ThingySticks/PiBlade/Boards/PiBackPlaneConnector/Images/bottom.png

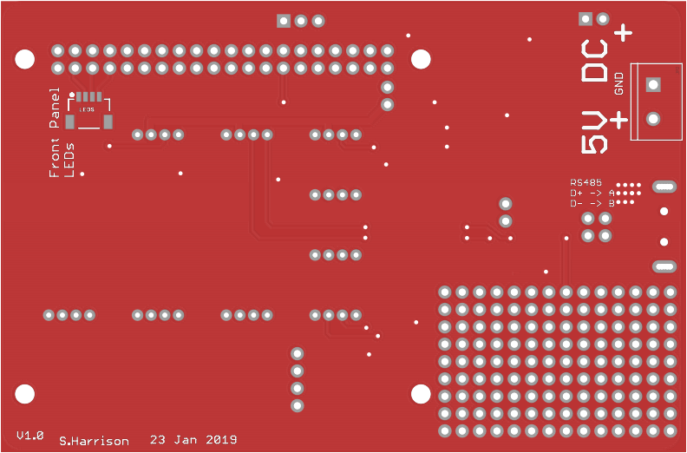
Boards/PiBackPlaneConnector/Images/bottom.png
