ThingySticks/PiBlade/Boards/PiBackPlaneConnector/Images/bottom_copper.png

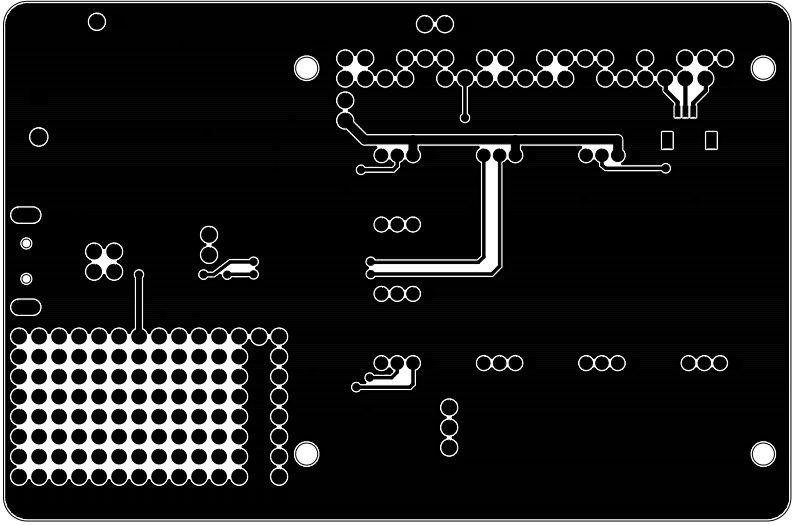
Boards/PiBackPlaneConnector/Images/bottom_copper.png
