ThingySticks/PiBlade/Boards/PiBackPlaneConnector/Images/bottom_silkscreen.png

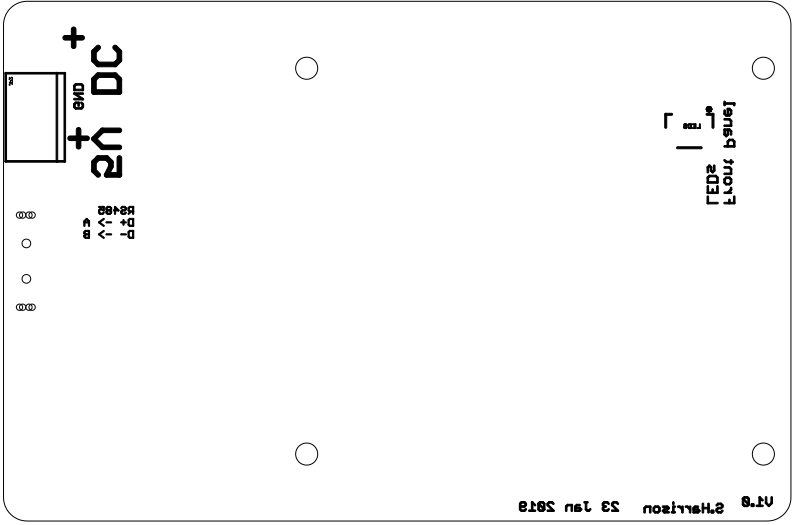
Boards/PiBackPlaneConnector/Images/bottom_silkscreen.png
