ThingySticks/PiBlade/Boards/PiBackPlaneConnector/Images/mill.png

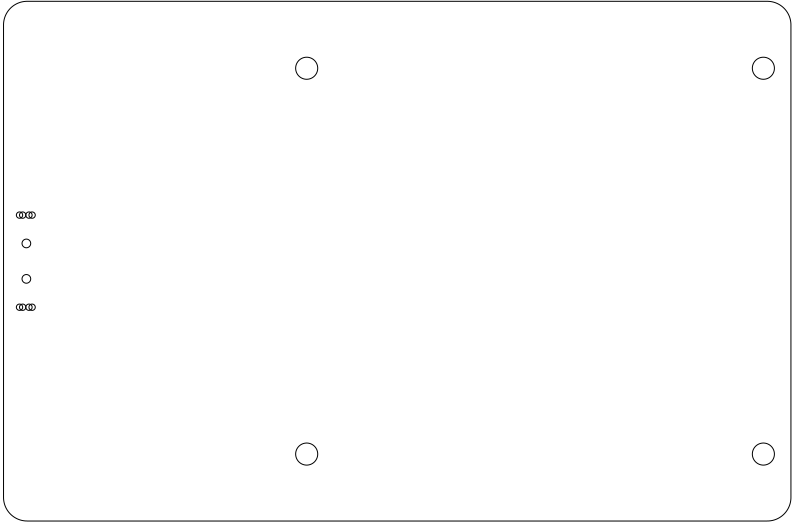
Boards/PiBackPlaneConnector/Images/mill.png
