ThingySticks/PiBlade/Boards/PiBackPlaneConnector/Images/PcbAllLayersDesign.png

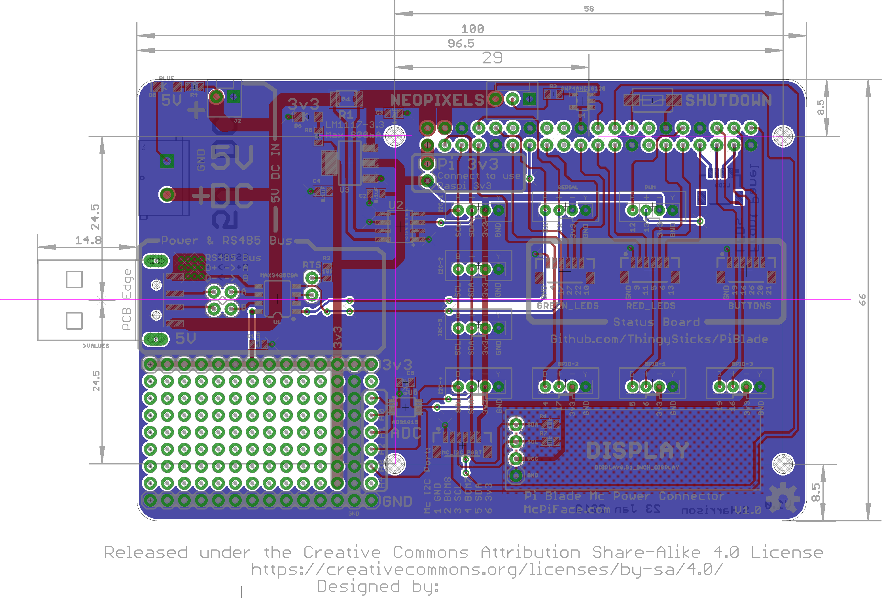
Boards/PiBackPlaneConnector/Images/PcbAllLayersDesign.png
