ThingySticks/PiBlade/Boards/PiBackPlaneConnector/Images/PcbTopDesign.png

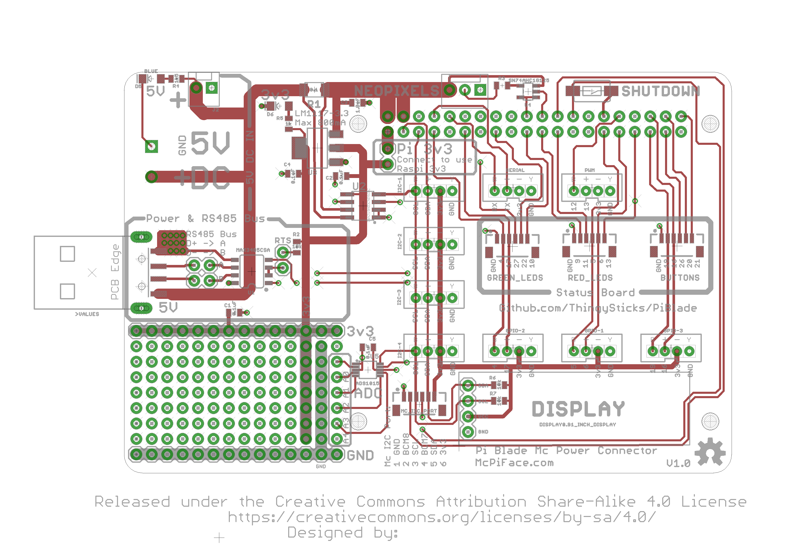
Boards/PiBackPlaneConnector/Images/PcbTopDesign.png
