ThingySticks/PiBlade/Boards/PiBackPlaneConnector/Images/Schematic.png

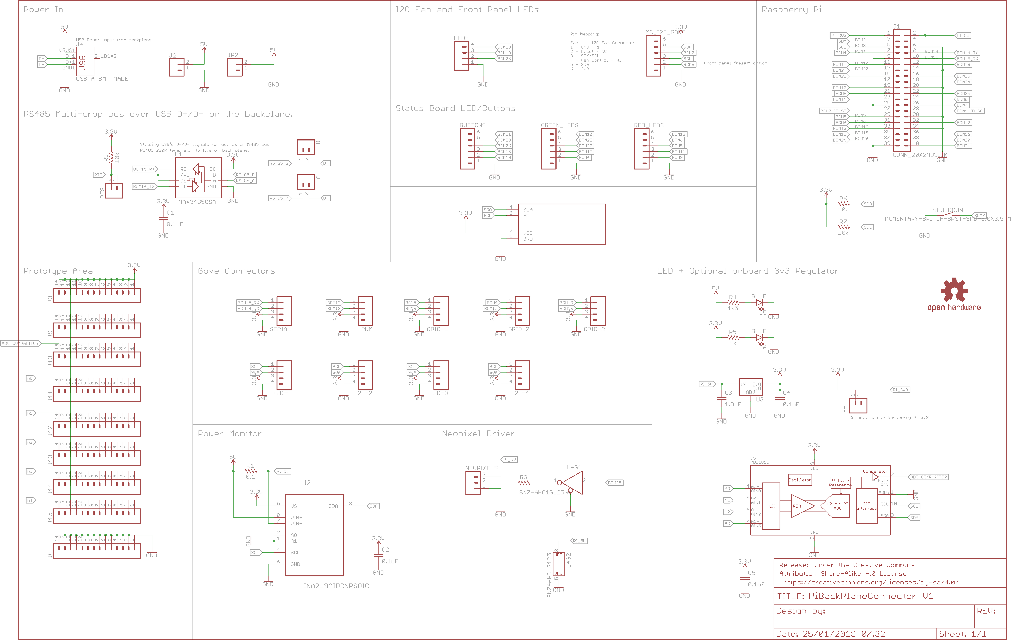
Boards/PiBackPlaneConnector/Images/Schematic.png
