ThingySticks/PiBlade/Boards/PiBackPlaneConnector/Images/top.png

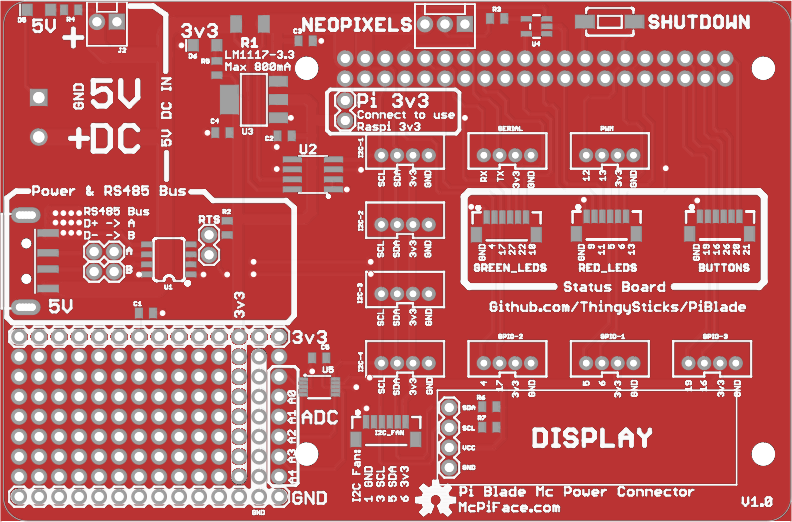
Boards/PiBackPlaneConnector/Images/top.png
