ThingySticks/PiBlade/Boards/PiBackPlaneConnector/Images/top_copper.png

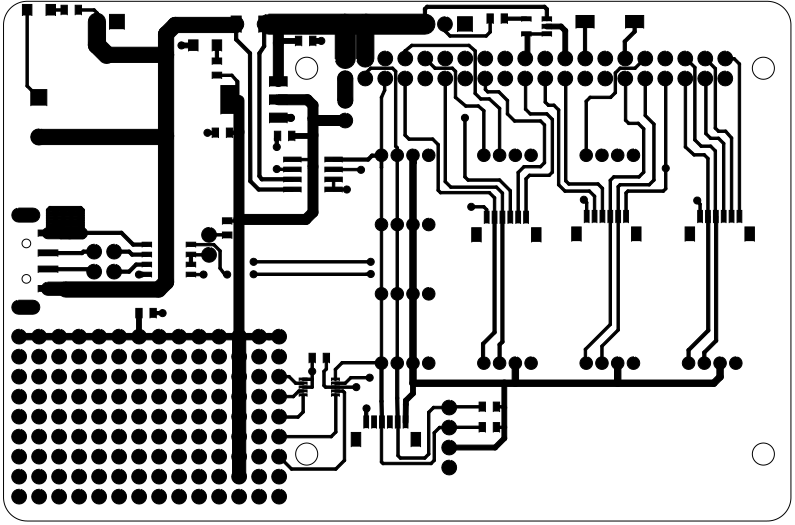
Boards/PiBackPlaneConnector/Images/top_copper.png
