ThingySticks/PiBlade/Boards/PiBackPlaneConnector/Images/top_silkscreen.png

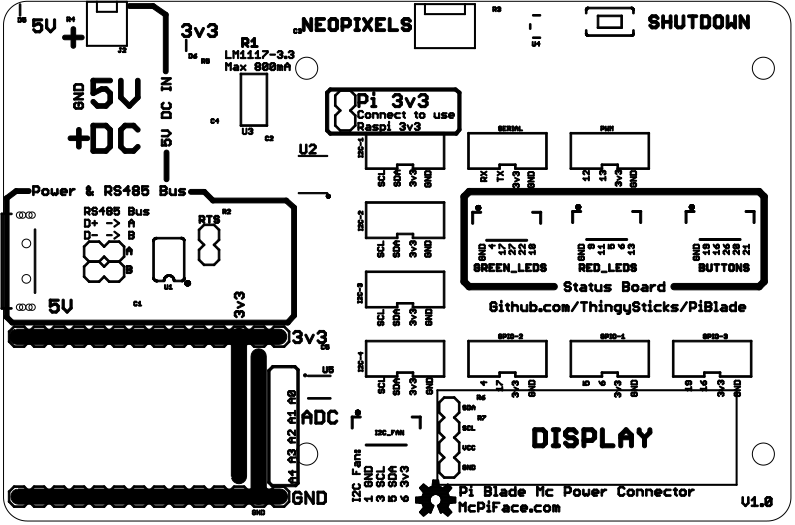
Boards/PiBackPlaneConnector/Images/top_silkscreen.png
