ThingySticks/PiBlade/Boards/PiBladeBackPlane/Images/PcbAllLayersDesign.png

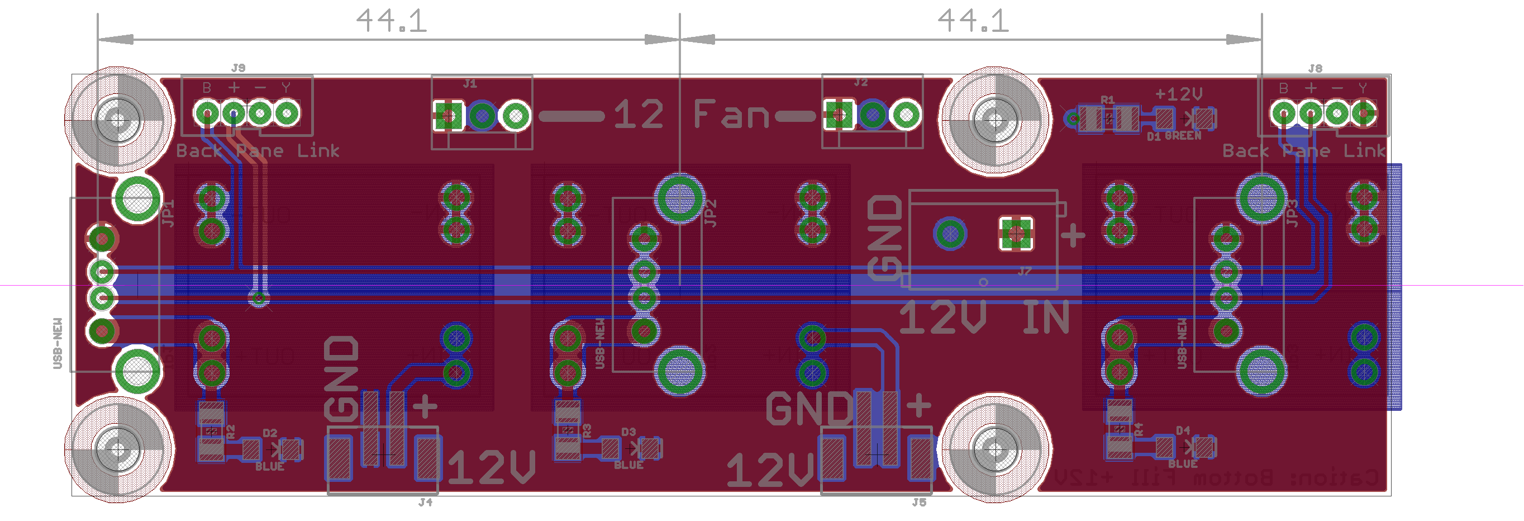
Boards/PiBladeBackPlane/Images/PcbAllLayersDesign.png
