ThingySticks/PiBlade/Boards/PiBladeBackPlane/Images/PcbBottomDesign.png

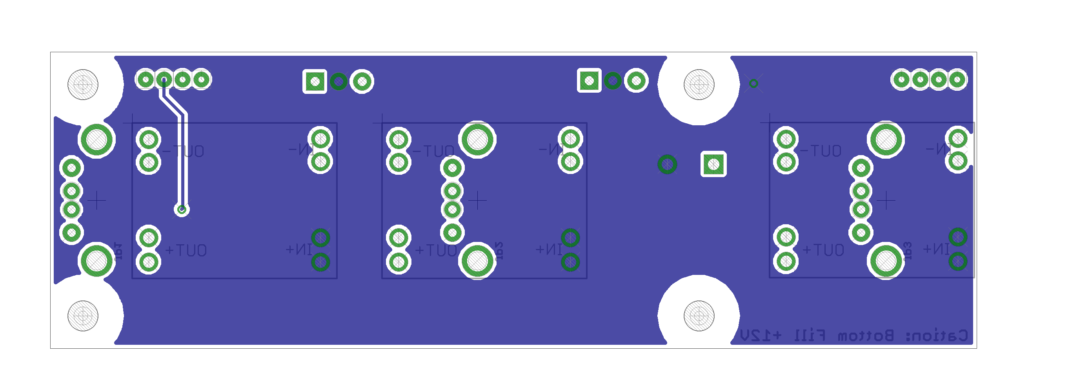
Boards/PiBladeBackPlane/Images/PcbBottomDesign.png
