ThingySticks/PiBlade/Boards/PiBladeBackPlane/Images/PcbTopDesign.png

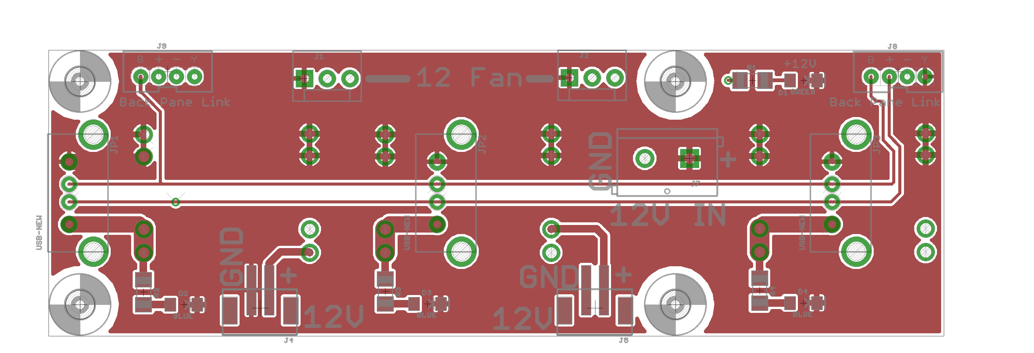
Boards/PiBladeBackPlane/Images/PcbTopDesign.png
