ThingySticks/PiBlade/Boards/PiBladeBackPlane/Images/Schematic.png

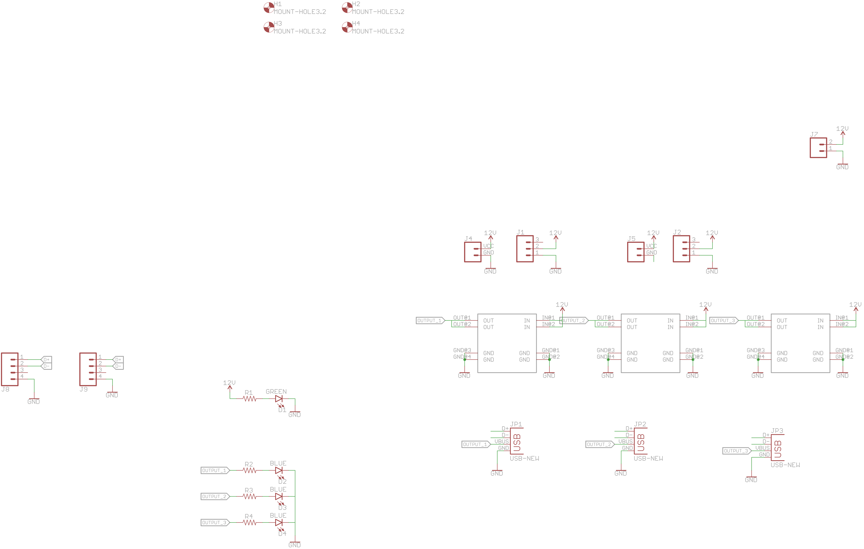
Boards/PiBladeBackPlane/Images/Schematic.png
