ThingySticks/PiBlade/Boards/PSU/Images/bottom.png

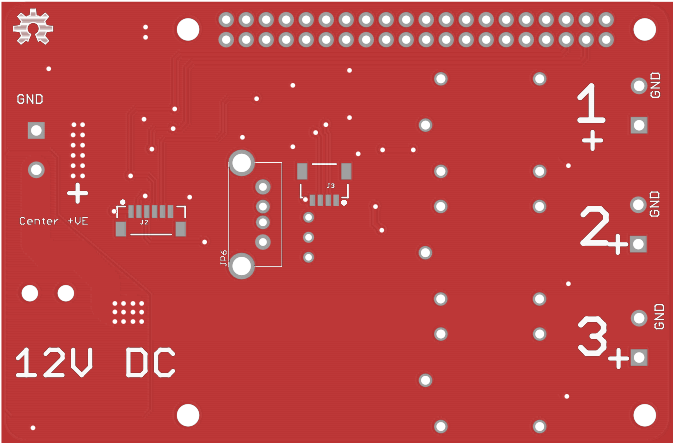
Boards/PSU/Images/bottom.png
