ThingySticks/PiBlade/Boards/PSU/Images/bottom_copper.png

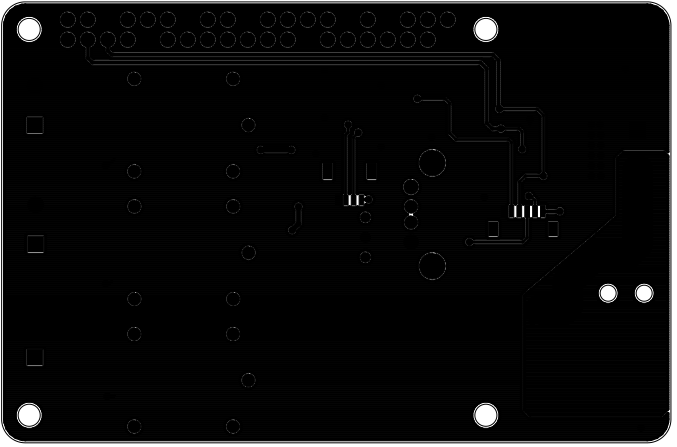
Boards/PSU/Images/bottom_copper.png
