ThingySticks/PiBlade/Boards/PSU/Images/bottom_silkscreen.png

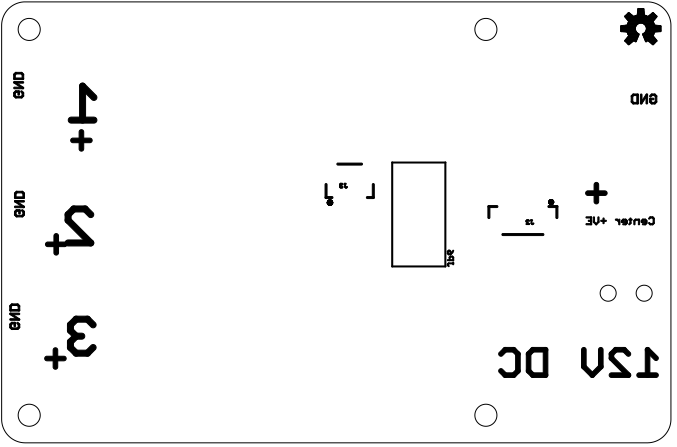
Boards/PSU/Images/bottom_silkscreen.png
