ThingySticks/PiBlade/Boards/PSU/Images/mill.png

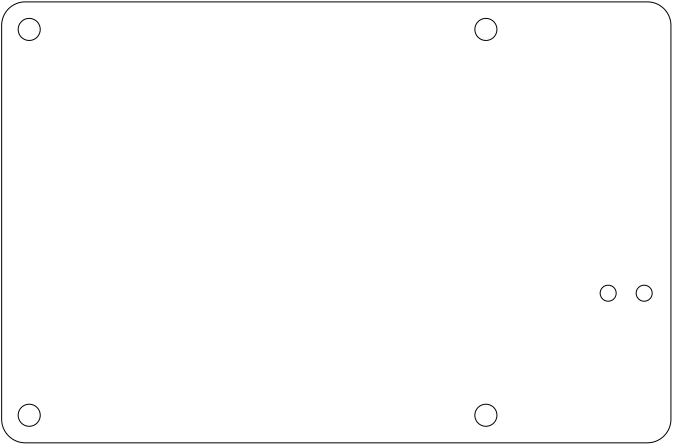
Boards/PSU/Images/mill.png
