ThingySticks/PiBlade/Boards/PSU/Images/PcbAllLayersDesign.png

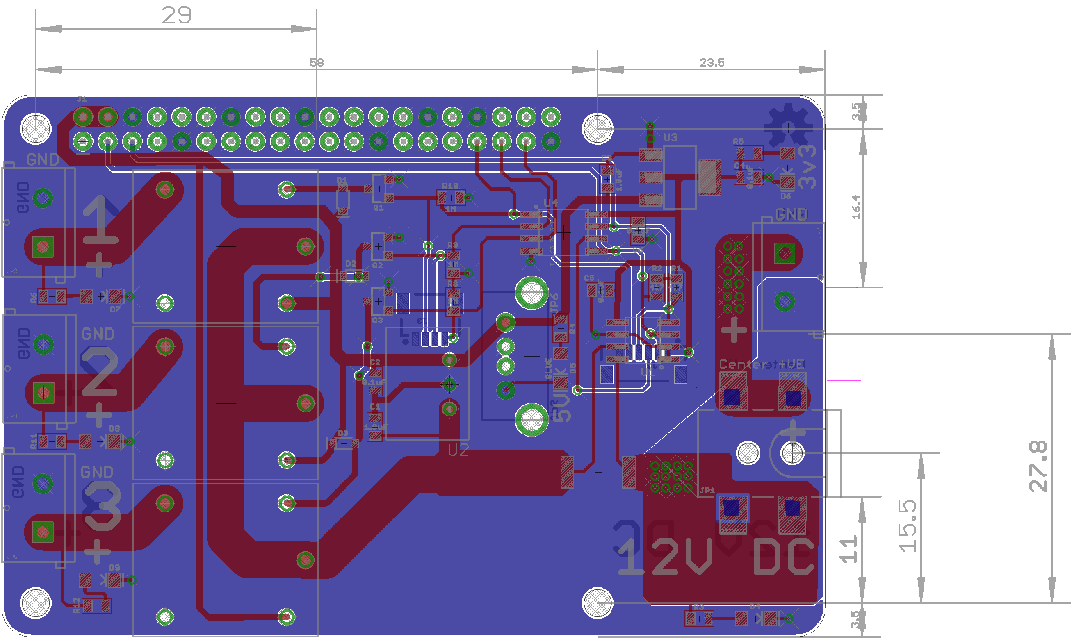
Boards/PSU/Images/PcbAllLayersDesign.png
