ThingySticks/PiBlade/Boards/PSU/Images/PcbBottomDesign.png

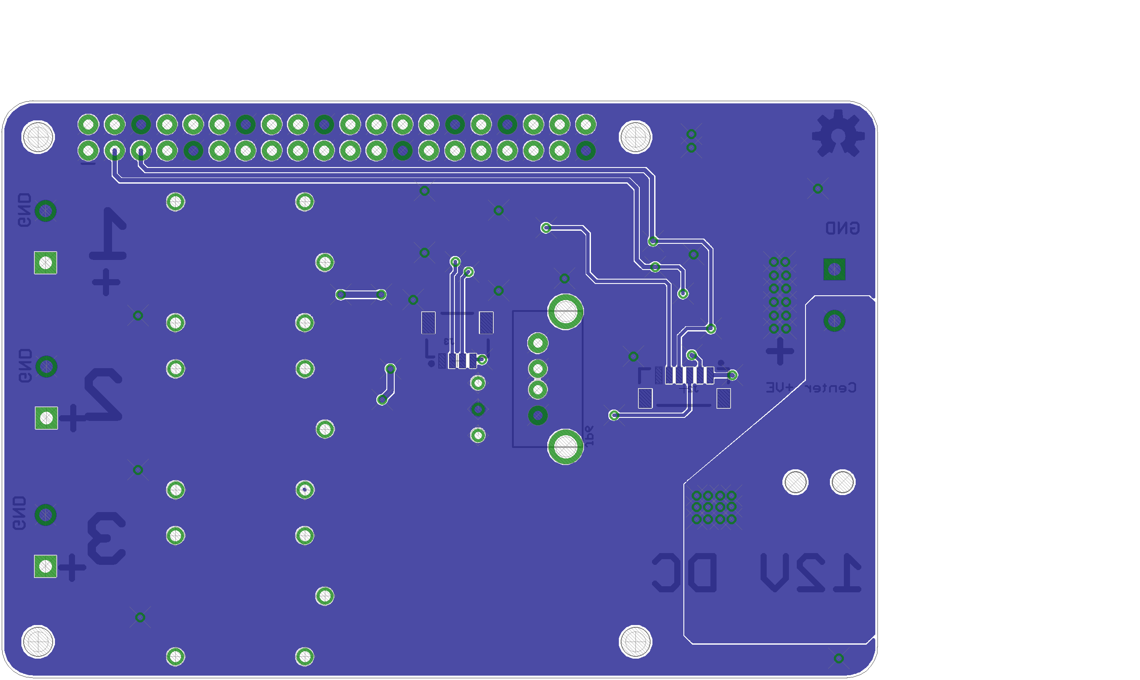
Boards/PSU/Images/PcbBottomDesign.png
