ThingySticks/PiBlade/Boards/PSU/Images/PcbTopDesign.png

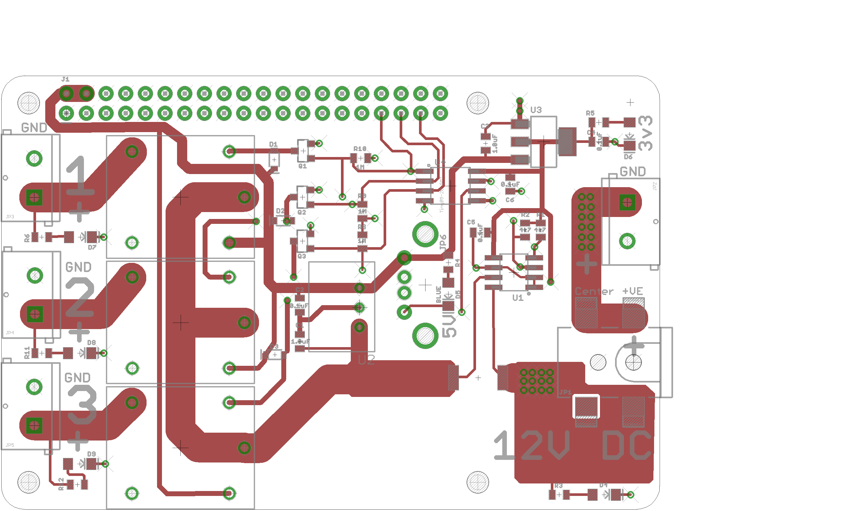
Boards/PSU/Images/PcbTopDesign.png
