ThingySticks/PiBlade/Boards/PSU/Images/Schematic.png

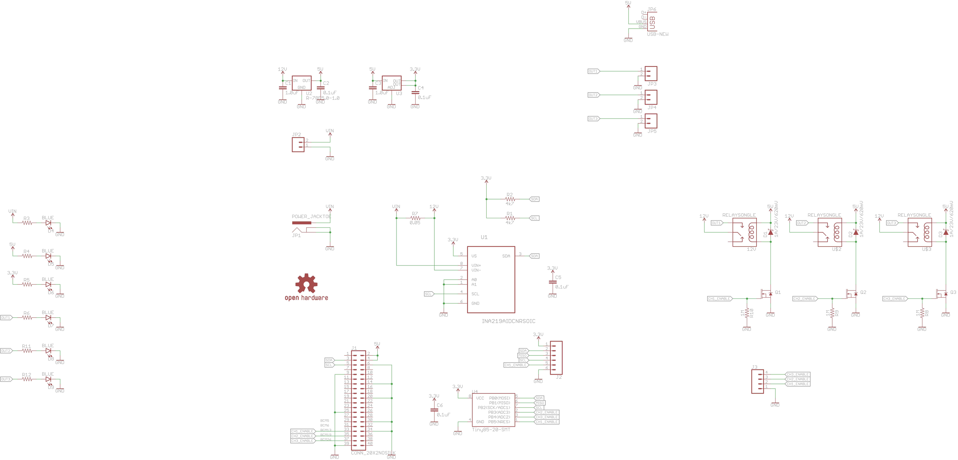
Boards/PSU/Images/Schematic.png
