ThingySticks/PiBlade/Boards/PSU/Images/top.png

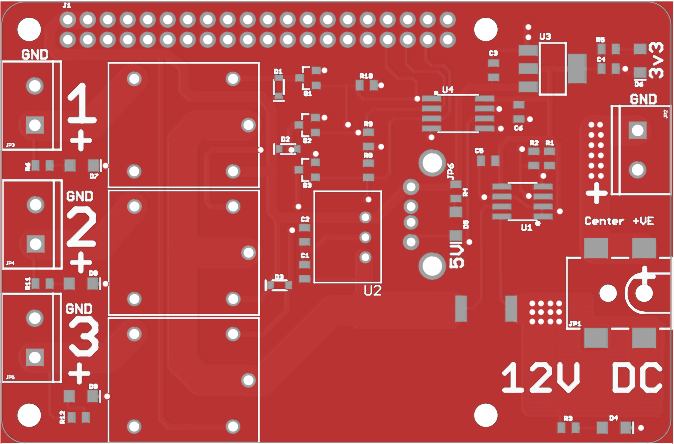
Boards/PSU/Images/top.png
