ThingySticks/PiBlade/Boards/PSU/Images/top_copper.png

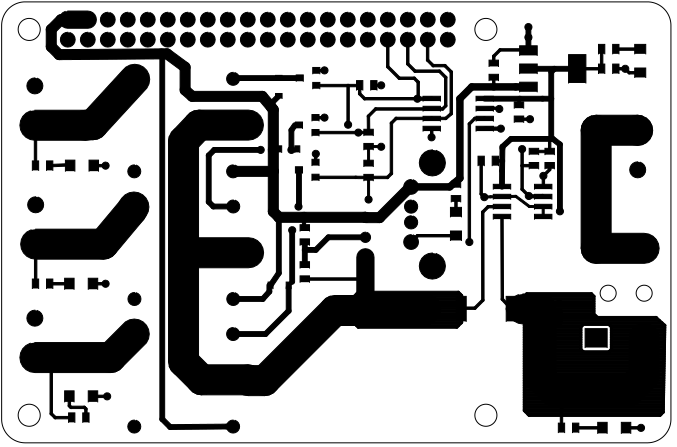
Boards/PSU/Images/top_copper.png
