ThingySticks/PiBlade/Boards/PSU/Images/top_silkscreen.png

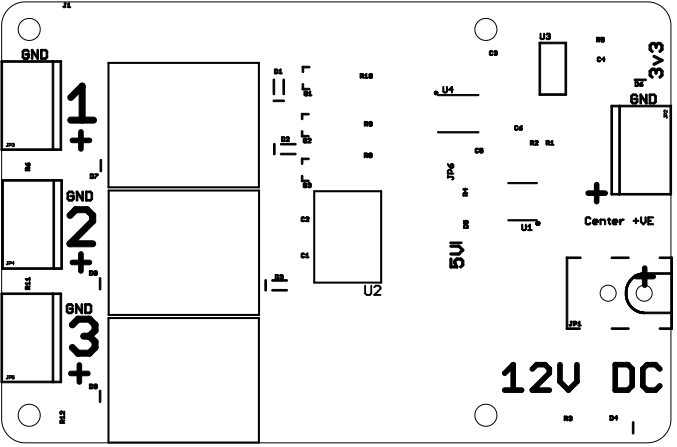
Boards/PSU/Images/top_silkscreen.png
