ThingySticks/PiBlade/FrontPanels/McPiFace/Images/Audio/bottom.png

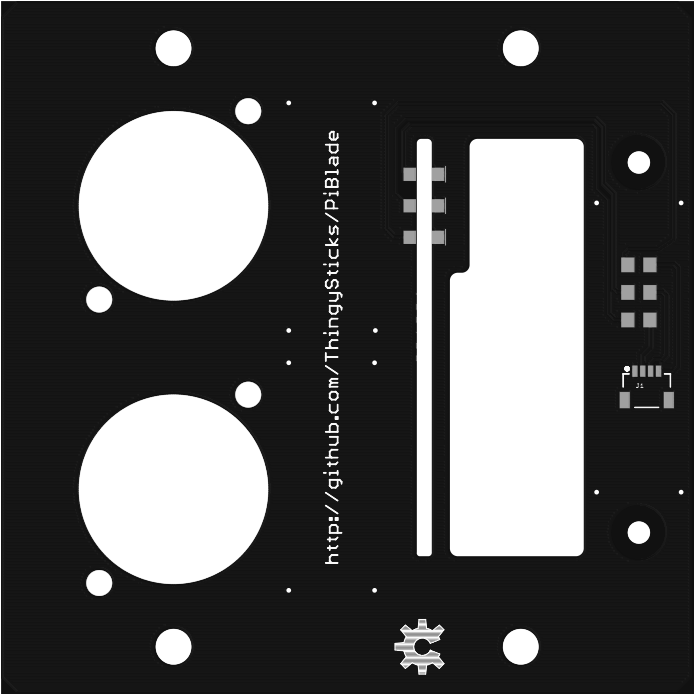
FrontPanels/McPiFace/Images/Audio/bottom.png
