ThingySticks/PiBlade/FrontPanels/McPiFace/Images/Audio/bottom_copper.png

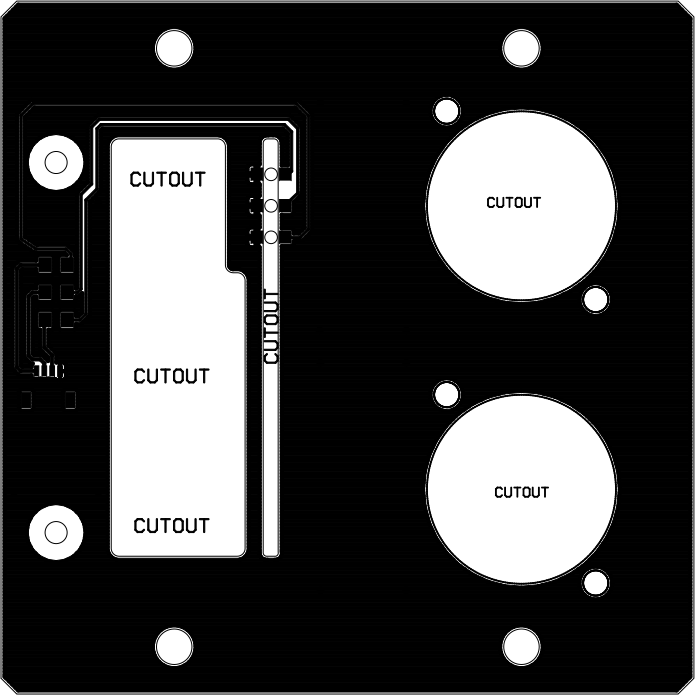
FrontPanels/McPiFace/Images/Audio/bottom_copper.png
