ThingySticks/PiBlade/FrontPanels/McPiFace/Images/Audio/bottom_silkscreen.png

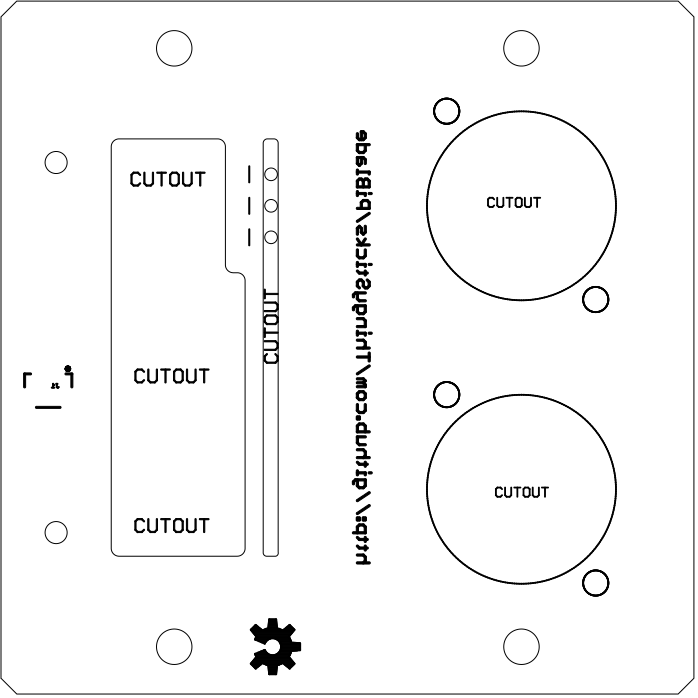
FrontPanels/McPiFace/Images/Audio/bottom_silkscreen.png
