ThingySticks/PiBlade/FrontPanels/McPiFace/Images/Audio/mill.png

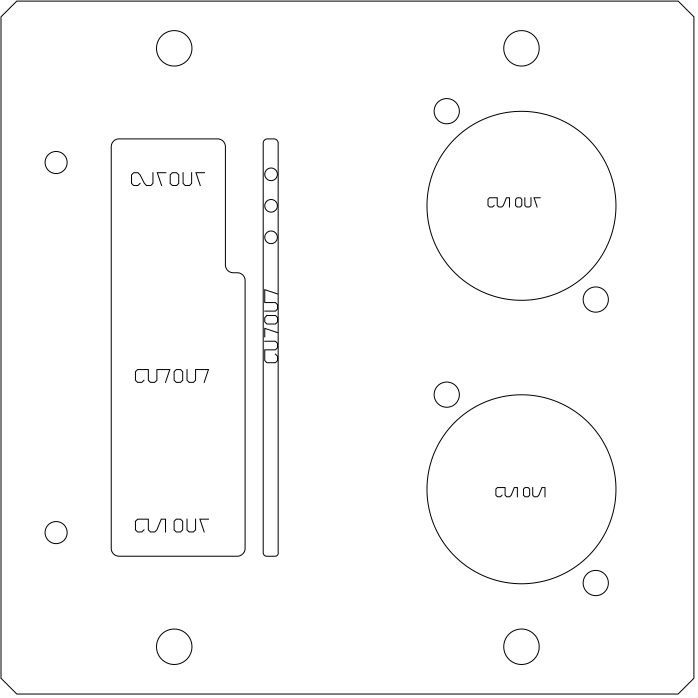
FrontPanels/McPiFace/Images/Audio/mill.png
