ThingySticks/PiBlade/FrontPanels/McPiFace/Images/Audio/PcbAllLayersDesign.png

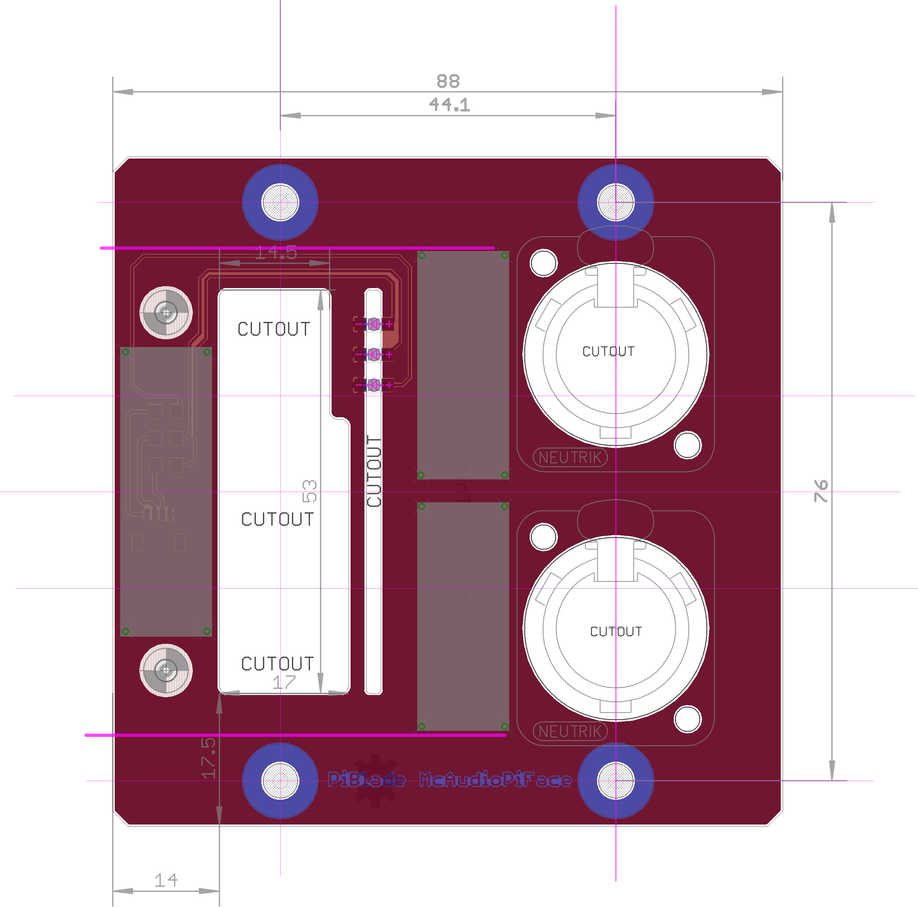
FrontPanels/McPiFace/Images/Audio/PcbAllLayersDesign.png
