ThingySticks/PiBlade/FrontPanels/McPiFace/Images/Audio/Schematic.png

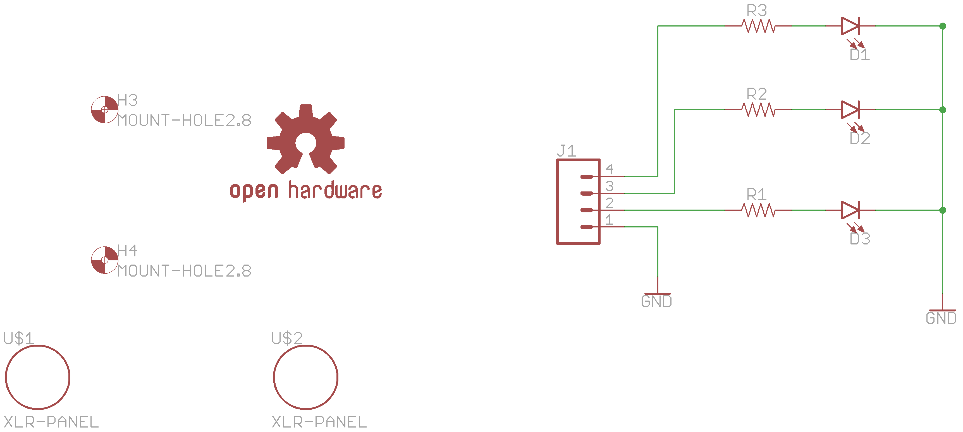
FrontPanels/McPiFace/Images/Audio/Schematic.png
