ThingySticks/PiBlade/FrontPanels/McPiFace/Images/Audio/top.png

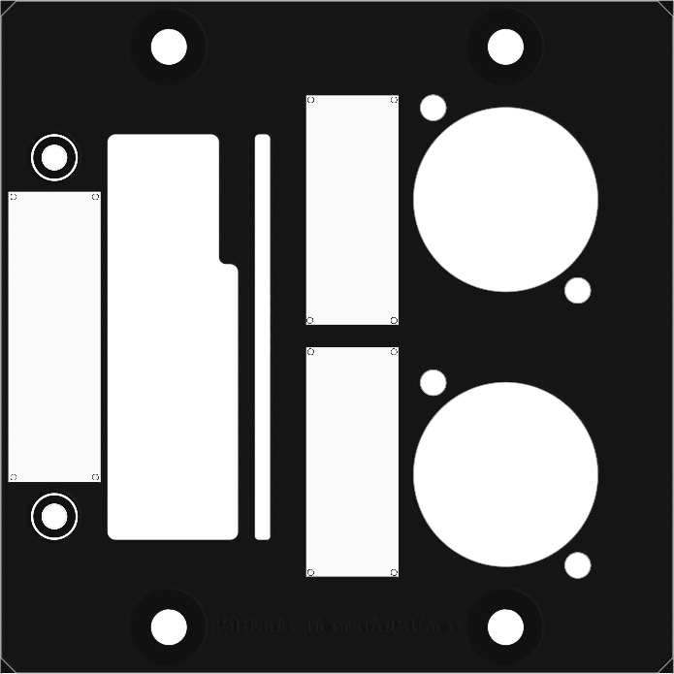
FrontPanels/McPiFace/Images/Audio/top.png
