ThingySticks/PiBlade/FrontPanels/McPiFace/Images/Audio/top_copper.png

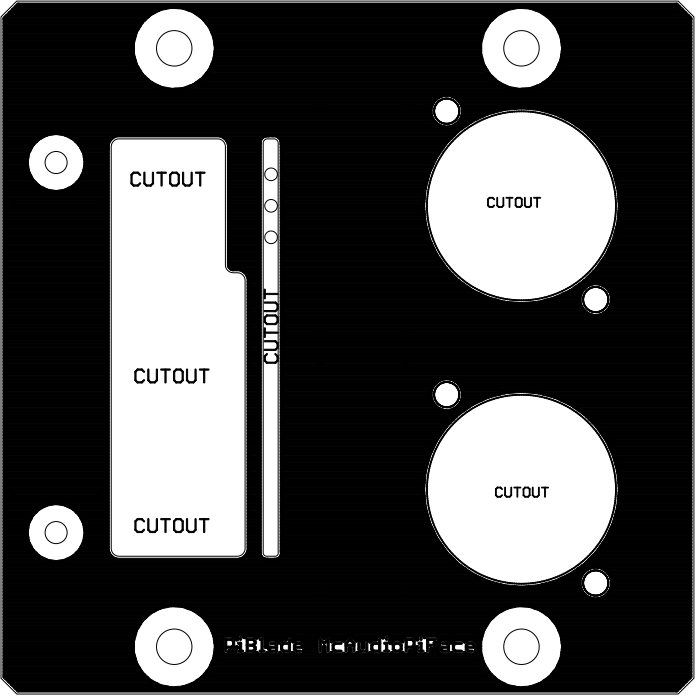
FrontPanels/McPiFace/Images/Audio/top_copper.png
