ThingySticks/PiBlade/FrontPanels/McPiFace/Images/Audio/top_silkscreen.png

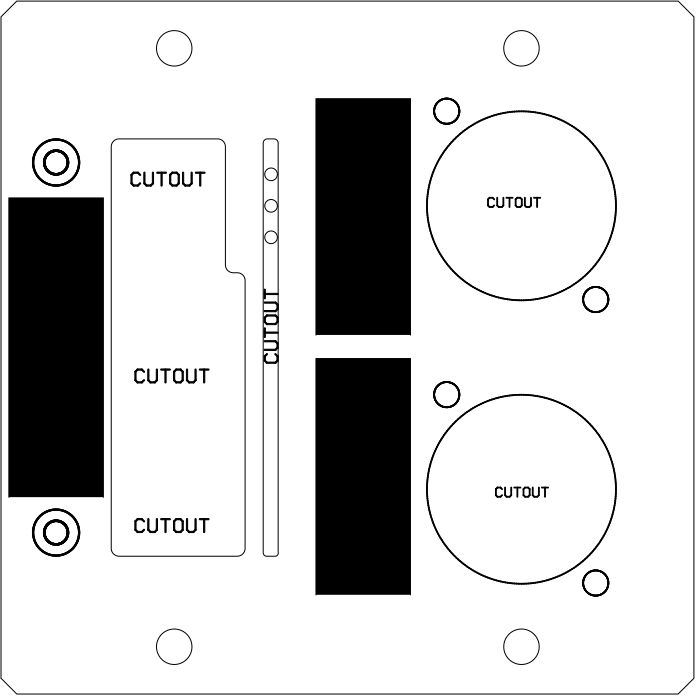
FrontPanels/McPiFace/Images/Audio/top_silkscreen.png
