ThingySticks/PiBlade/FrontPanels/McPiFace/Images/Camera/bottom.png

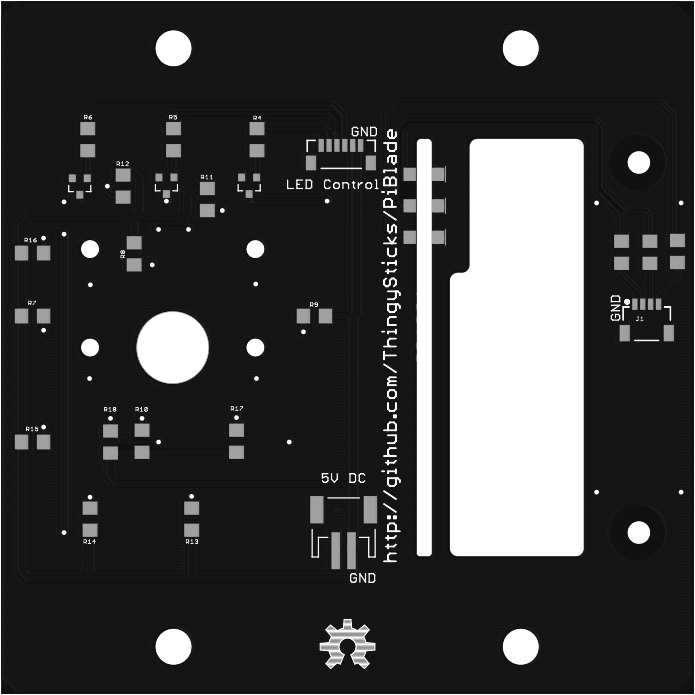
FrontPanels/McPiFace/Images/Camera/bottom.png
