ThingySticks/PiBlade/FrontPanels/McPiFace/Images/Camera/bottom_copper.png

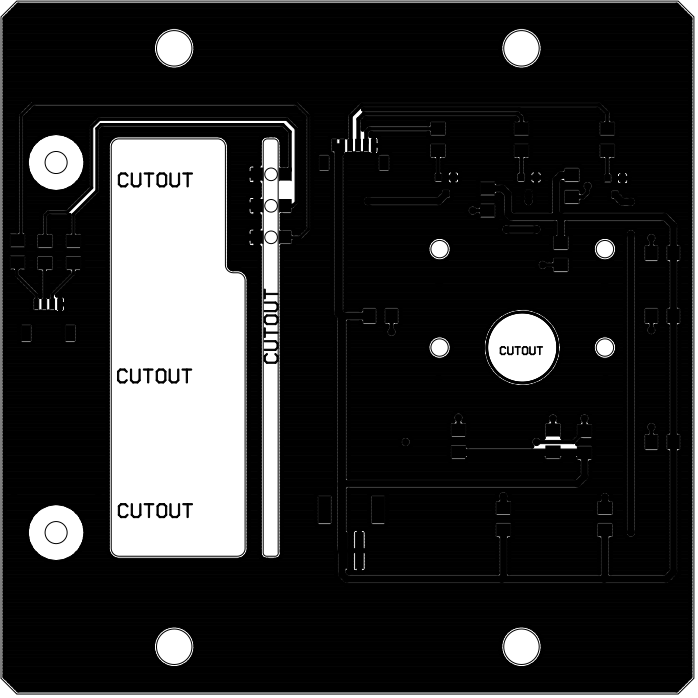
FrontPanels/McPiFace/Images/Camera/bottom_copper.png
