ThingySticks/PiBlade/FrontPanels/McPiFace/Images/Camera/bottom_silkscreen.png

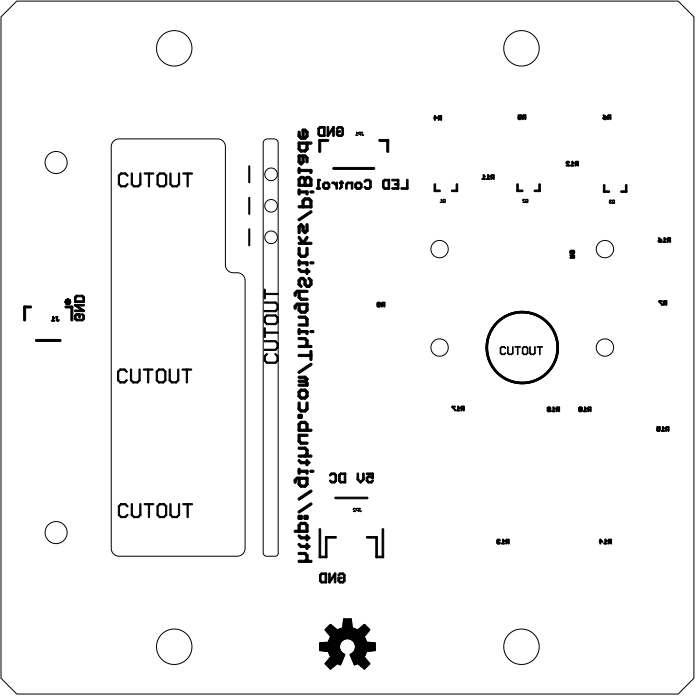
FrontPanels/McPiFace/Images/Camera/bottom_silkscreen.png
