ThingySticks/PiBlade/FrontPanels/McPiFace/Images/Camera/mill.png

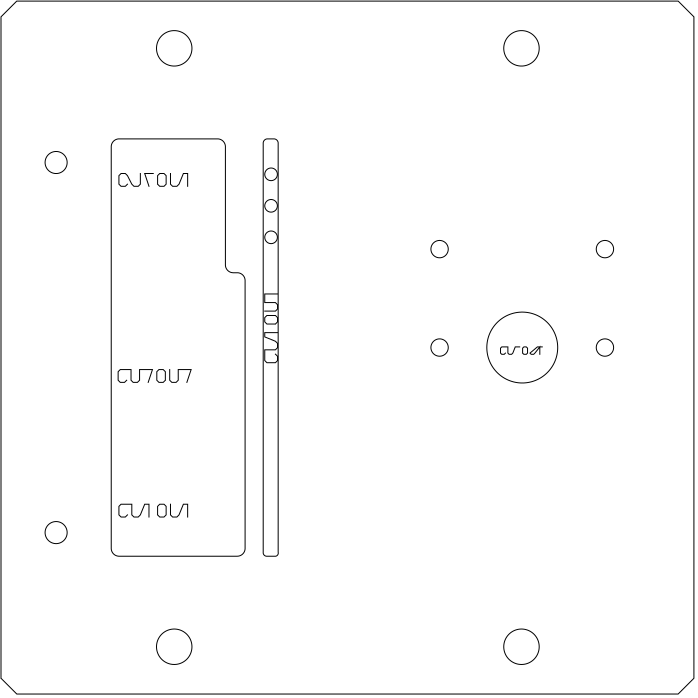
FrontPanels/McPiFace/Images/Camera/mill.png
