ThingySticks/PiBlade/FrontPanels/McPiFace/Images/Camera/PcbAllLayersDesign.png

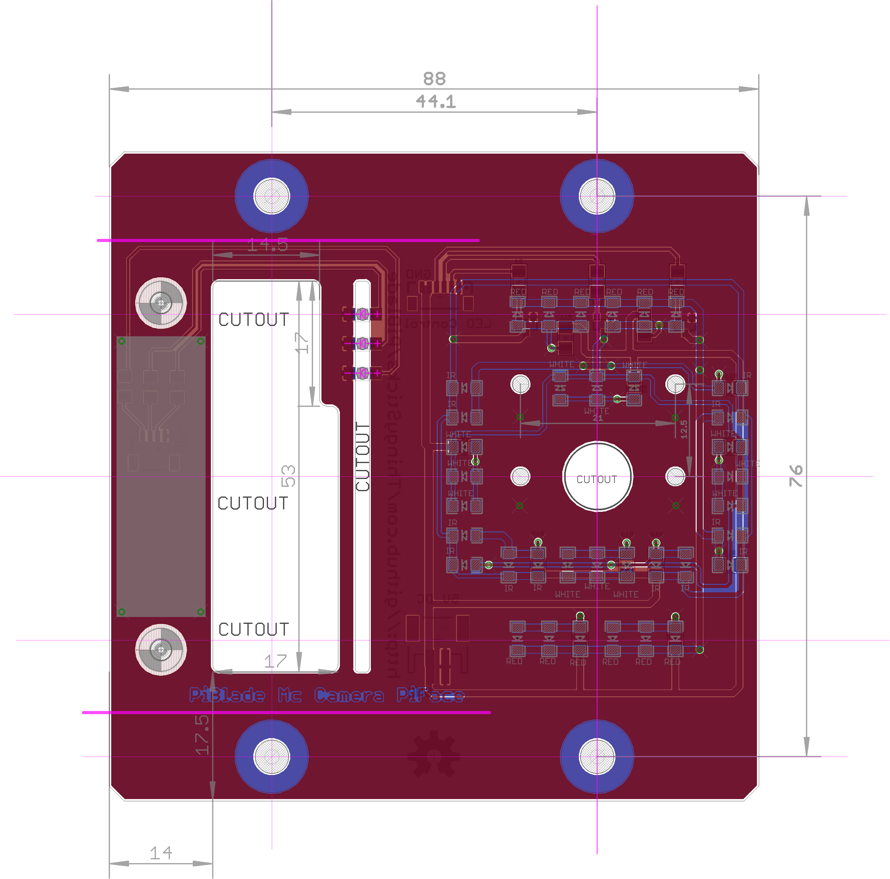
FrontPanels/McPiFace/Images/Camera/PcbAllLayersDesign.png
