ThingySticks/PiBlade/FrontPanels/McPiFace/Images/Camera/PcbBottomDesign.png

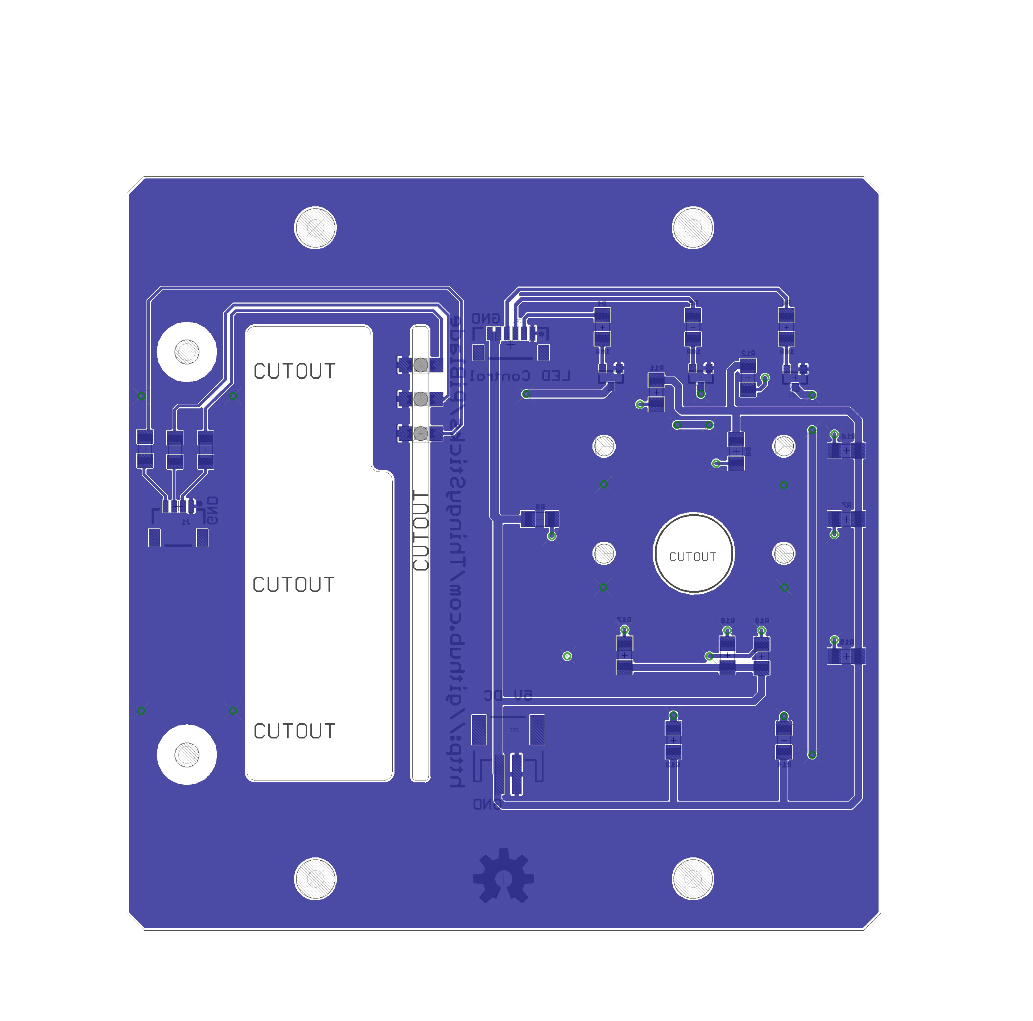
FrontPanels/McPiFace/Images/Camera/PcbBottomDesign.png
