ThingySticks/PiBlade/FrontPanels/McPiFace/Images/Camera/PcbTopDesign.png

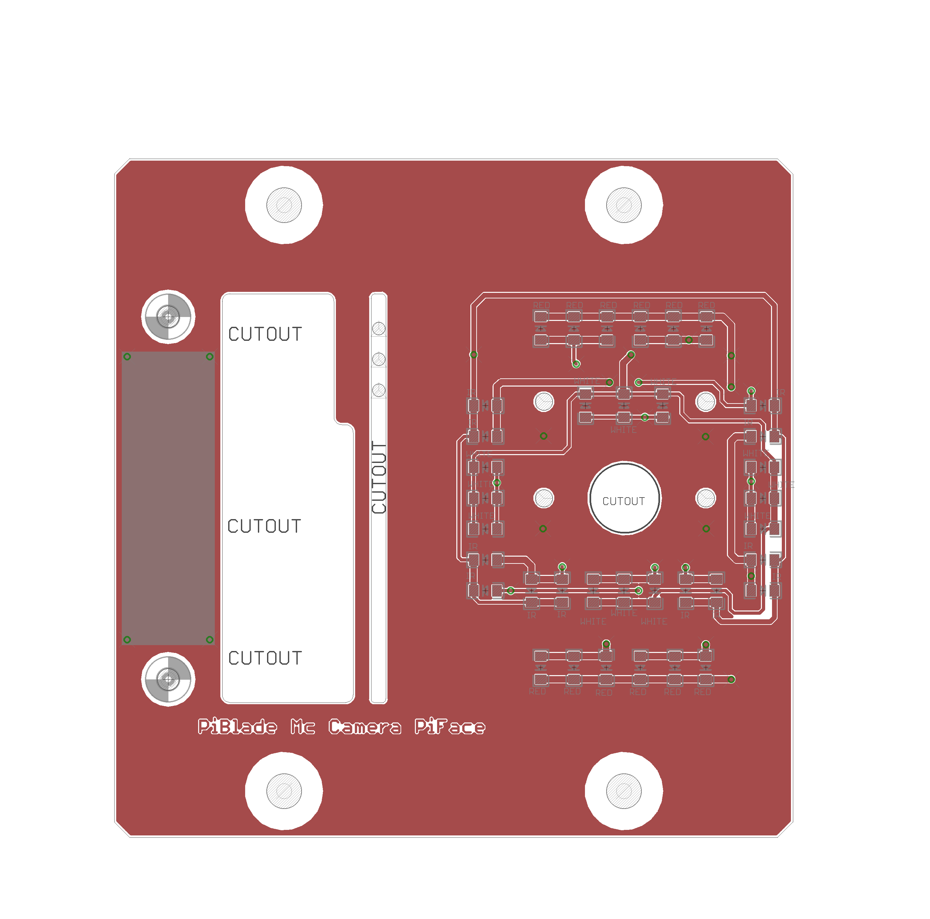
FrontPanels/McPiFace/Images/Camera/PcbTopDesign.png
