ThingySticks/PiBlade/FrontPanels/McPiFace/Images/Camera/Schematic.png

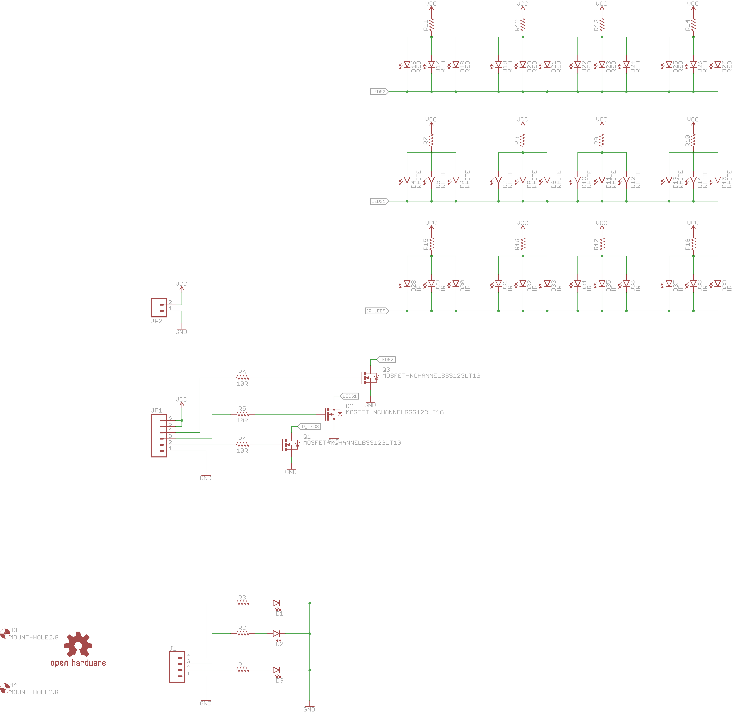
FrontPanels/McPiFace/Images/Camera/Schematic.png
