ThingySticks/PiBlade/FrontPanels/McPiFace/Images/Camera/top.png

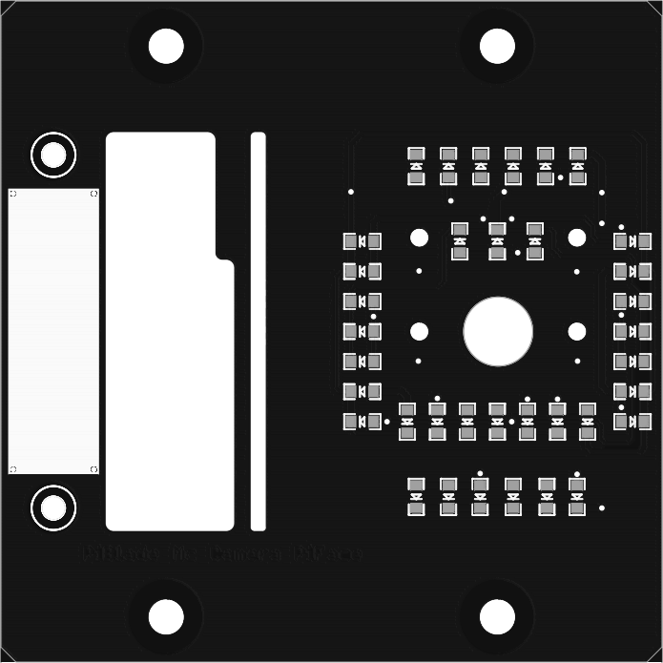
FrontPanels/McPiFace/Images/Camera/top.png
