ThingySticks/PiBlade/FrontPanels/McPiFace/Images/Camera/top_copper.png

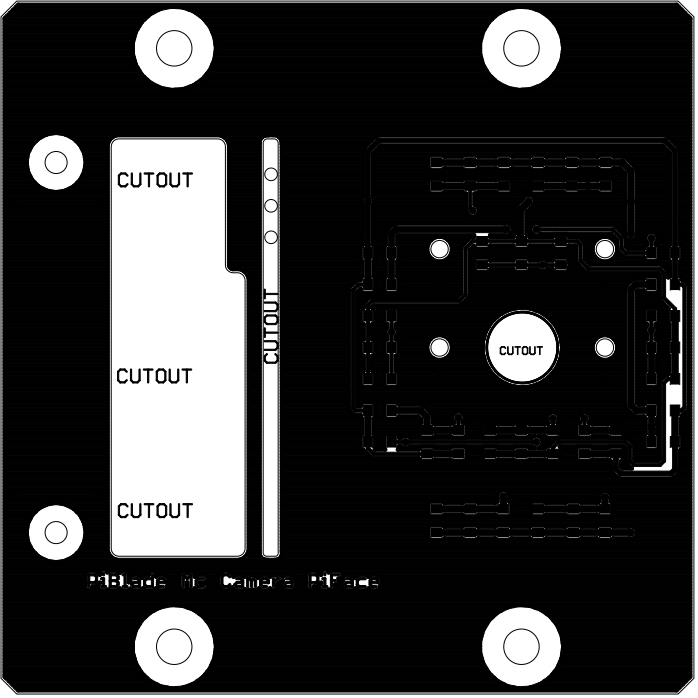
FrontPanels/McPiFace/Images/Camera/top_copper.png
