ThingySticks/PiBlade/FrontPanels/McPiFace/Images/Camera/top_silkscreen.png

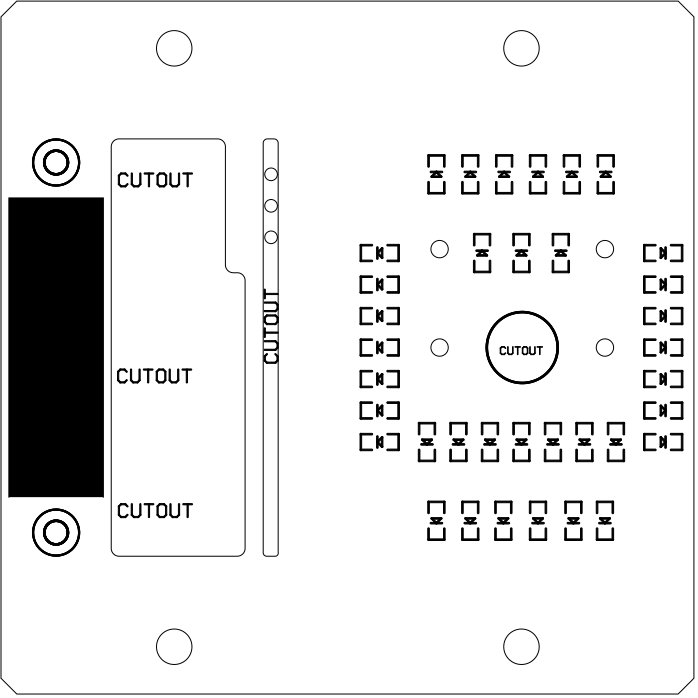
FrontPanels/McPiFace/Images/Camera/top_silkscreen.png
