ThingySticks/PiBlade/FrontPanels/McPiFace/Images/Double - Aerial/bottom.png

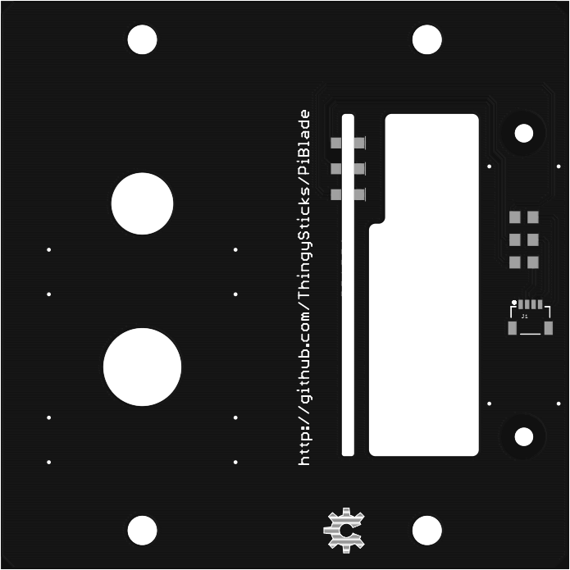
FrontPanels/McPiFace/Images/Double - Aerial/bottom.png
