ThingySticks/PiBlade/FrontPanels/McPiFace/Images/Double - Aerial/bottom_copper.png

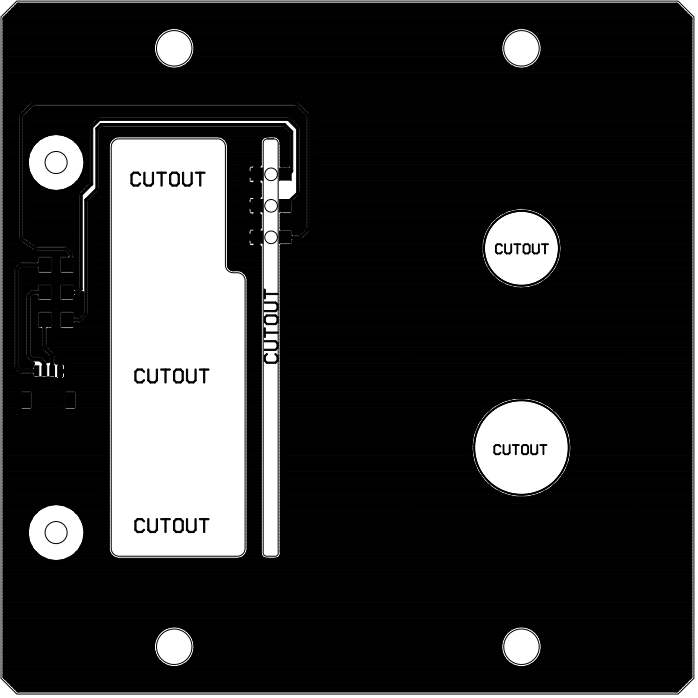
FrontPanels/McPiFace/Images/Double - Aerial/bottom_copper.png
