ThingySticks/PiBlade/FrontPanels/McPiFace/Images/Double - Aerial/bottom_silkscreen.png

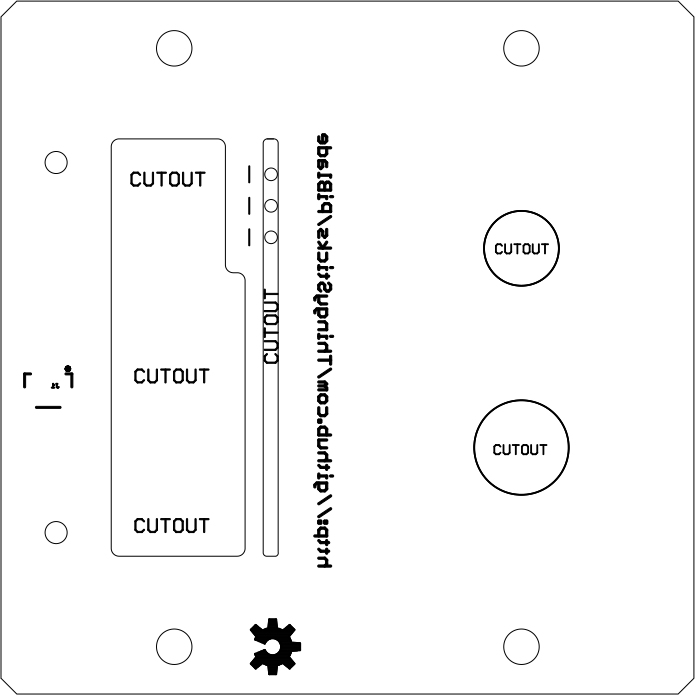
FrontPanels/McPiFace/Images/Double - Aerial/bottom_silkscreen.png
