ThingySticks/PiBlade/FrontPanels/McPiFace/Images/Double - Aerial/mill.png

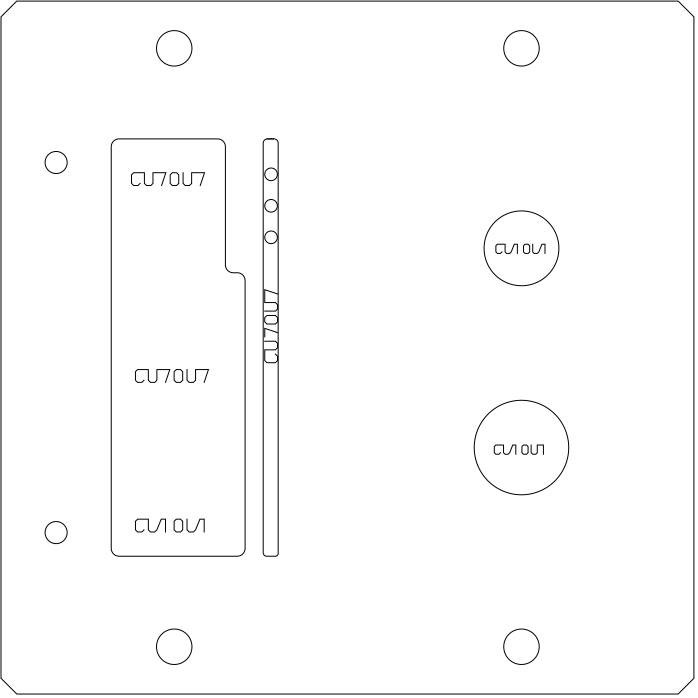
FrontPanels/McPiFace/Images/Double - Aerial/mill.png
