ThingySticks/PiBlade/FrontPanels/McPiFace/Images/Double - Aerial/PcbAllLayersDesign.png

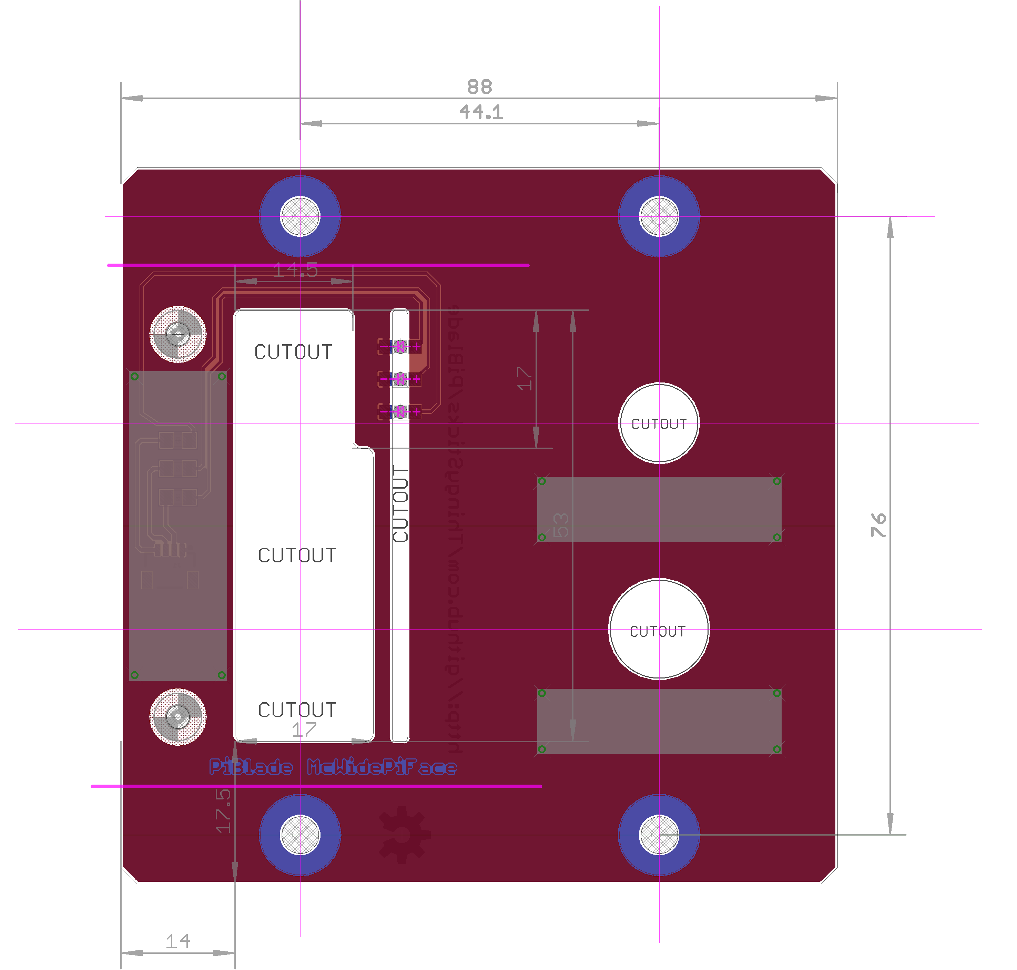
FrontPanels/McPiFace/Images/Double - Aerial/PcbAllLayersDesign.png
