ThingySticks/PiBlade/FrontPanels/McPiFace/Images/Double - Aerial/PcbBottomDesign.png

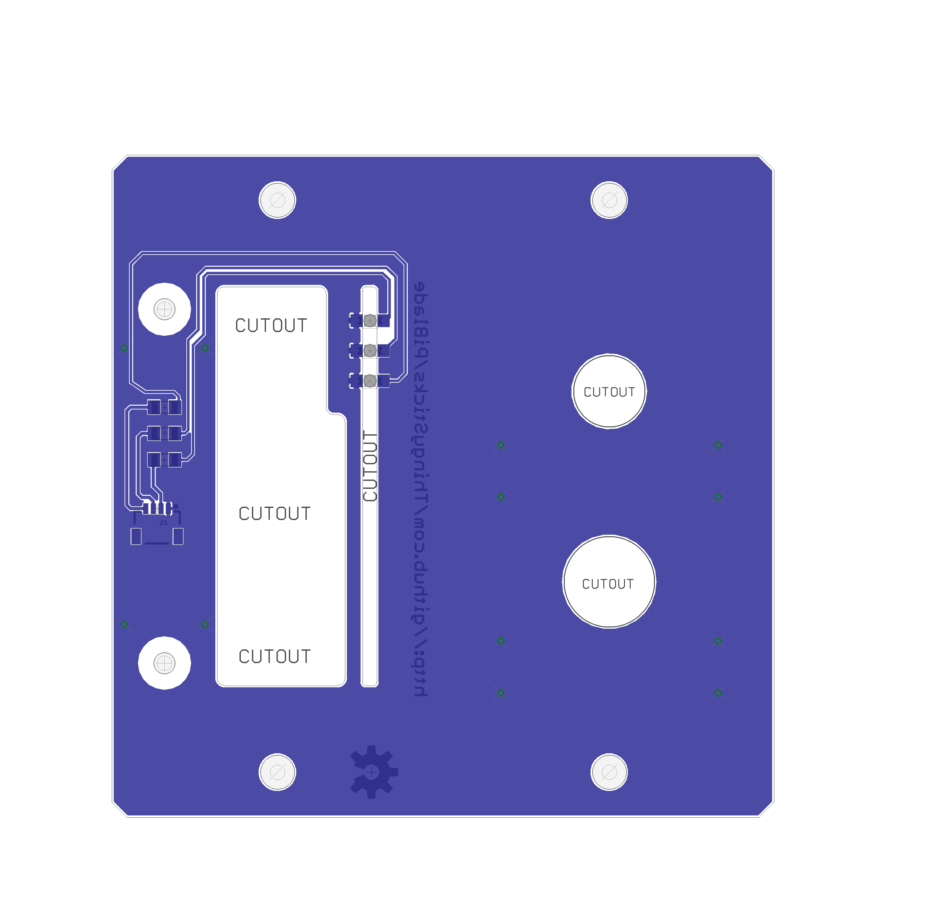
FrontPanels/McPiFace/Images/Double - Aerial/PcbBottomDesign.png
