ThingySticks/PiBlade/FrontPanels/McPiFace/Images/Double - Aerial/Schematic.png

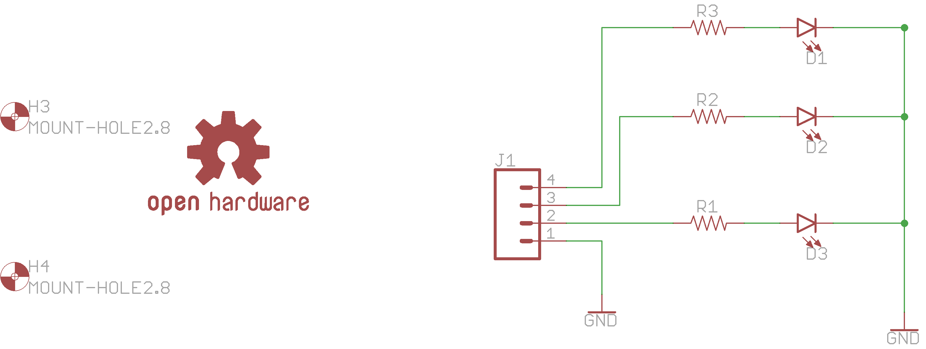
FrontPanels/McPiFace/Images/Double - Aerial/Schematic.png
