ThingySticks/PiBlade/FrontPanels/McPiFace/Images/Double - Aerial/top.png

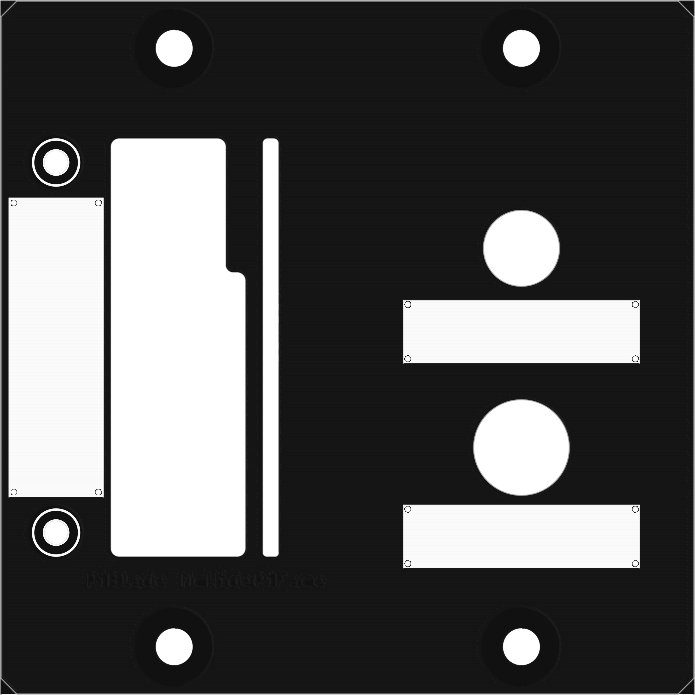
FrontPanels/McPiFace/Images/Double - Aerial/top.png
