ThingySticks/PiBlade/FrontPanels/McPiFace/Images/Double - Aerial/top_copper.png

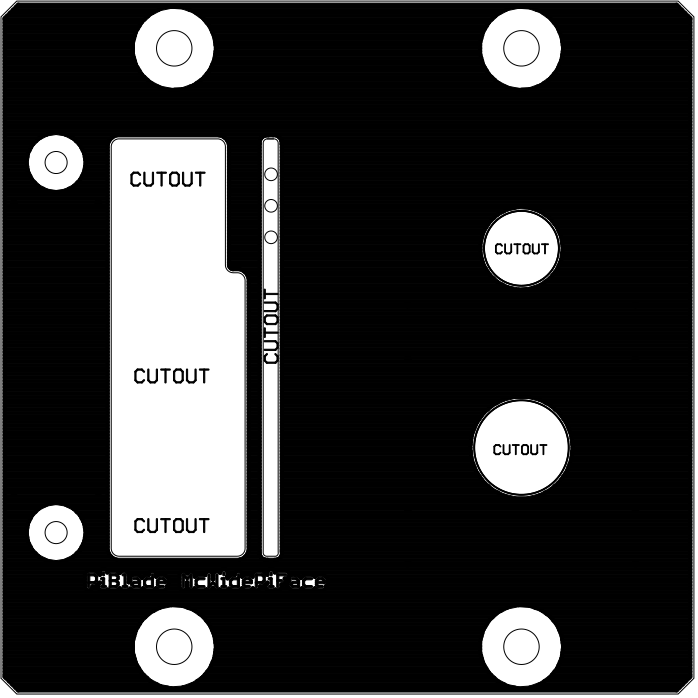
FrontPanels/McPiFace/Images/Double - Aerial/top_copper.png
