ThingySticks/PiBlade/FrontPanels/McPiFace/Images/Double - Aerial/top_silkscreen.png

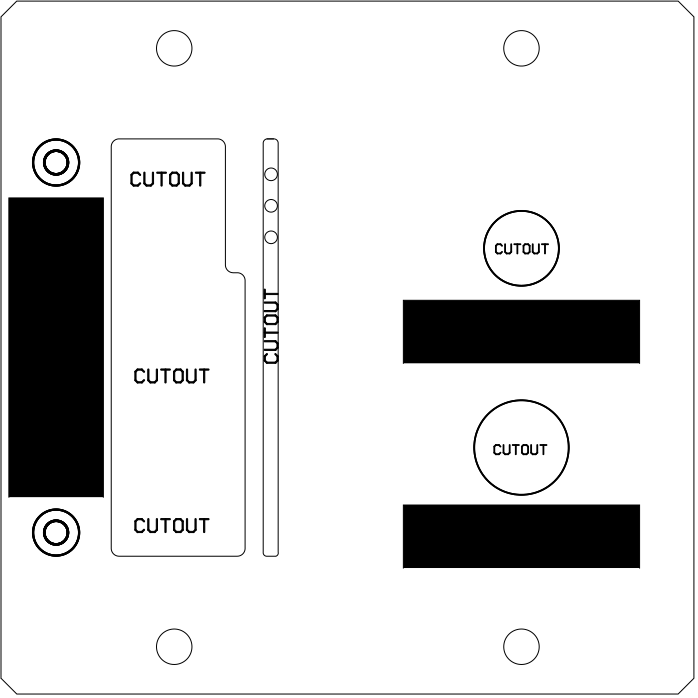
FrontPanels/McPiFace/Images/Double - Aerial/top_silkscreen.png
