ThingySticks/PiBlade/FrontPanels/McPiFace/Images/Environment-V1/bottom.png

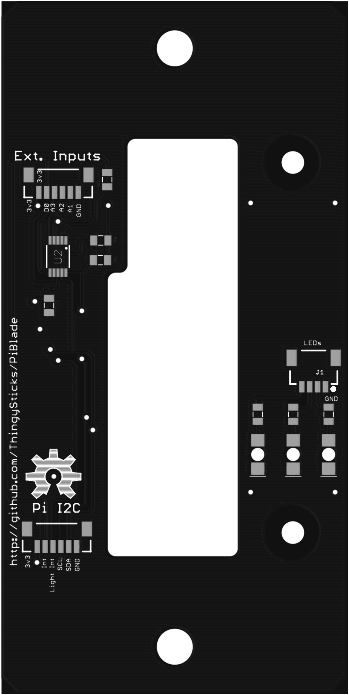
FrontPanels/McPiFace/Images/Environment-V1/bottom.png
