ThingySticks/PiBlade/FrontPanels/McPiFace/Images/Environment-V1/bottom_copper.png

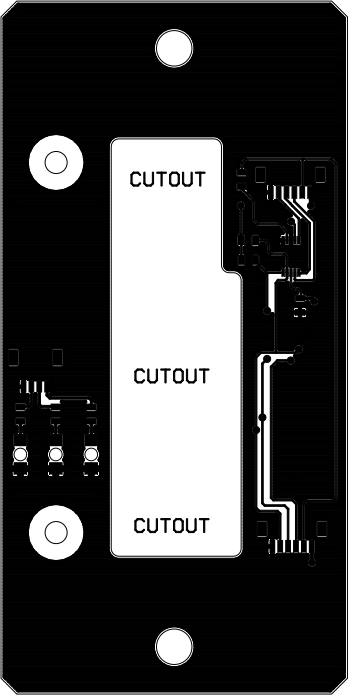
FrontPanels/McPiFace/Images/Environment-V1/bottom_copper.png
