ThingySticks/PiBlade/FrontPanels/McPiFace/Images/Environment-V1/bottom_silkscreen.png

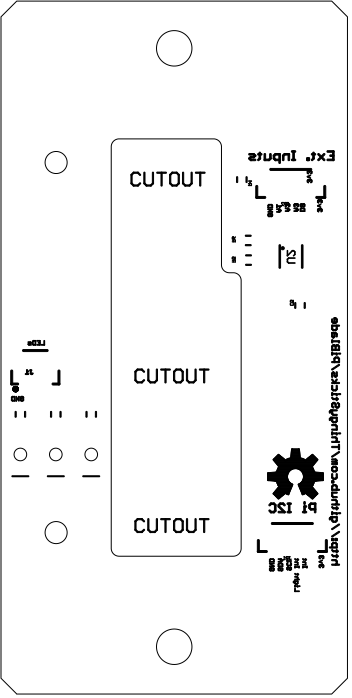
FrontPanels/McPiFace/Images/Environment-V1/bottom_silkscreen.png
