ThingySticks/PiBlade/FrontPanels/McPiFace/Images/Environment-V1/mill.png

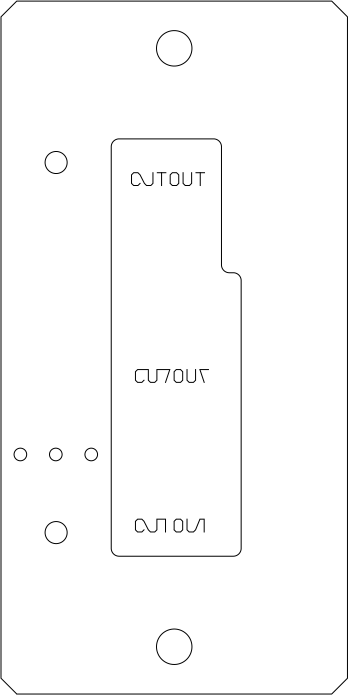
FrontPanels/McPiFace/Images/Environment-V1/mill.png
