ThingySticks/PiBlade/FrontPanels/McPiFace/Images/Environment-V1/PcbAllLayersDesign.png

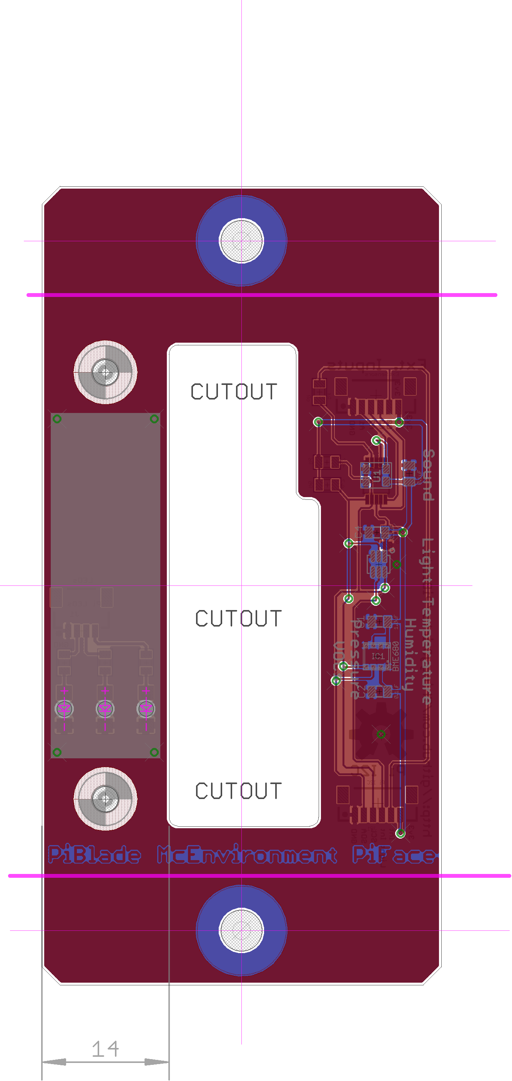
FrontPanels/McPiFace/Images/Environment-V1/PcbAllLayersDesign.png
