ThingySticks/PiBlade/FrontPanels/McPiFace/Images/Environment-V1/Schematic.png

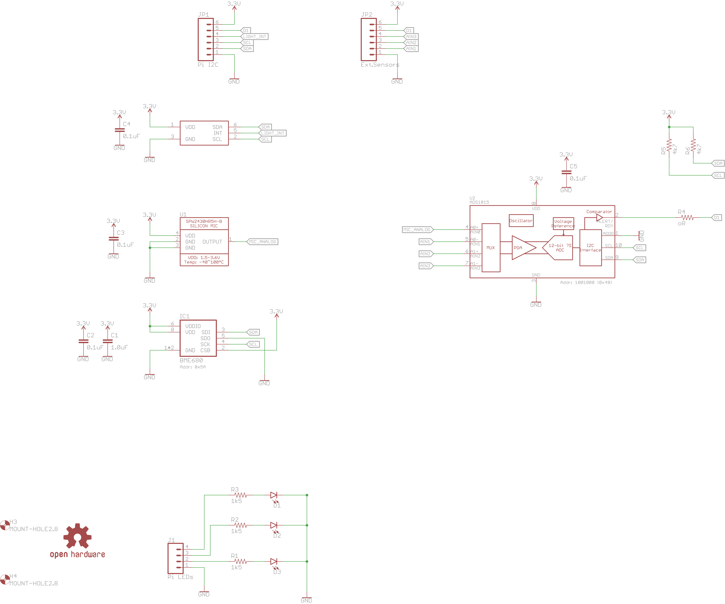
FrontPanels/McPiFace/Images/Environment-V1/Schematic.png
