ThingySticks/PiBlade/FrontPanels/McPiFace/Images/Environment-V1/top.png

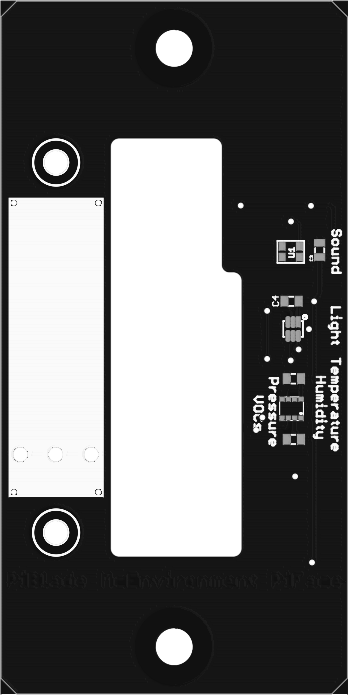
FrontPanels/McPiFace/Images/Environment-V1/top.png
