ThingySticks/PiBlade/FrontPanels/McPiFace/Images/Environment-V1/top_silkscreen.png

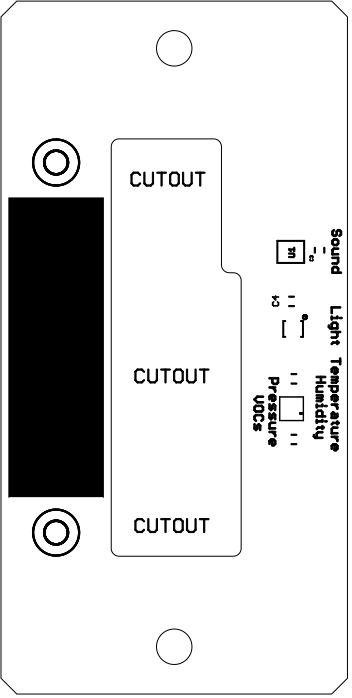
FrontPanels/McPiFace/Images/Environment-V1/top_silkscreen.png
