ThingySticks/PiBlade/FrontPanels/McPiFace/Images/Ethernet/bottom_copper.png

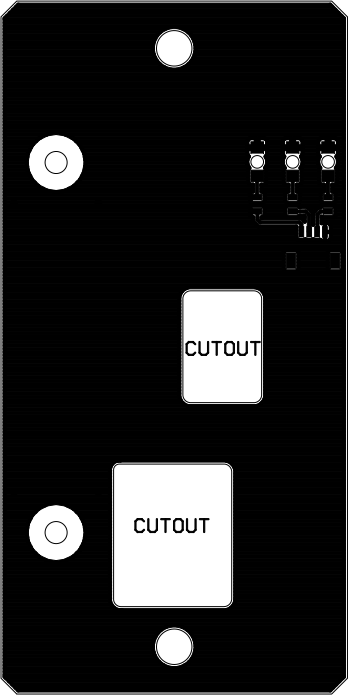
FrontPanels/McPiFace/Images/Ethernet/bottom_copper.png
