ThingySticks/PiBlade/FrontPanels/McPiFace/Images/Ethernet/top_copper.png

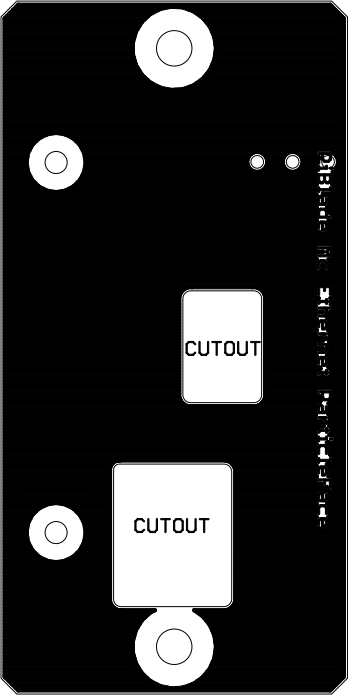
FrontPanels/McPiFace/Images/Ethernet/top_copper.png
