ThingySticks/PiBlade/FrontPanels/McPiFace/Images/Fan-V3/bottom.png

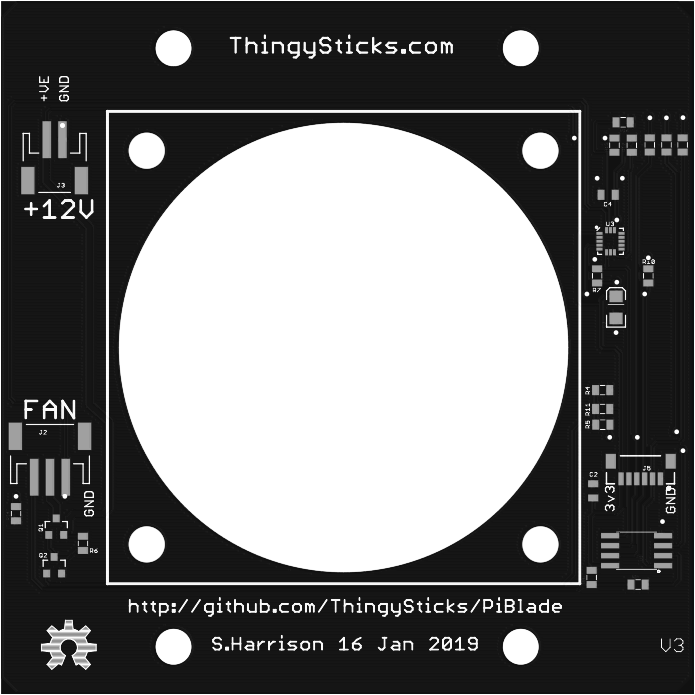
FrontPanels/McPiFace/Images/Fan-V3/bottom.png
