ThingySticks/PiBlade/FrontPanels/McPiFace/Images/Fan-V3/bottom_copper.png

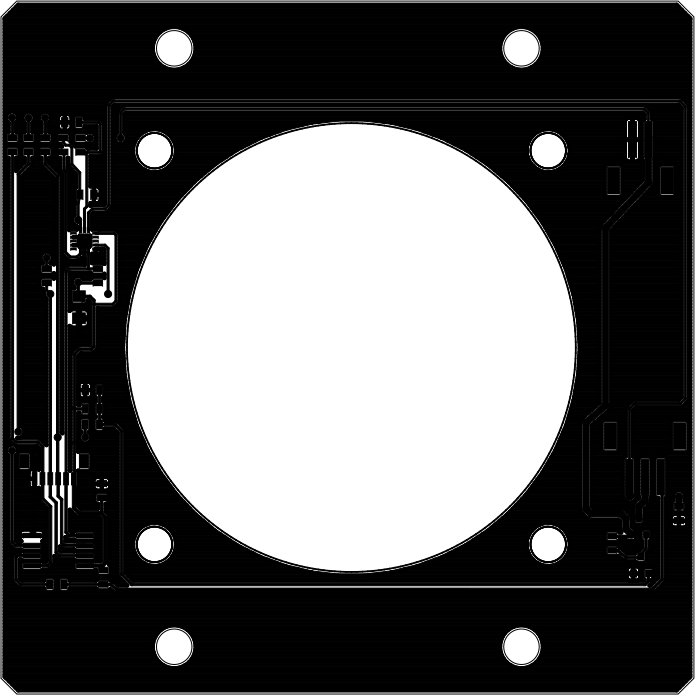
FrontPanels/McPiFace/Images/Fan-V3/bottom_copper.png
