ThingySticks/PiBlade/FrontPanels/McPiFace/Images/Fan-V3/bottom_silkscreen.png

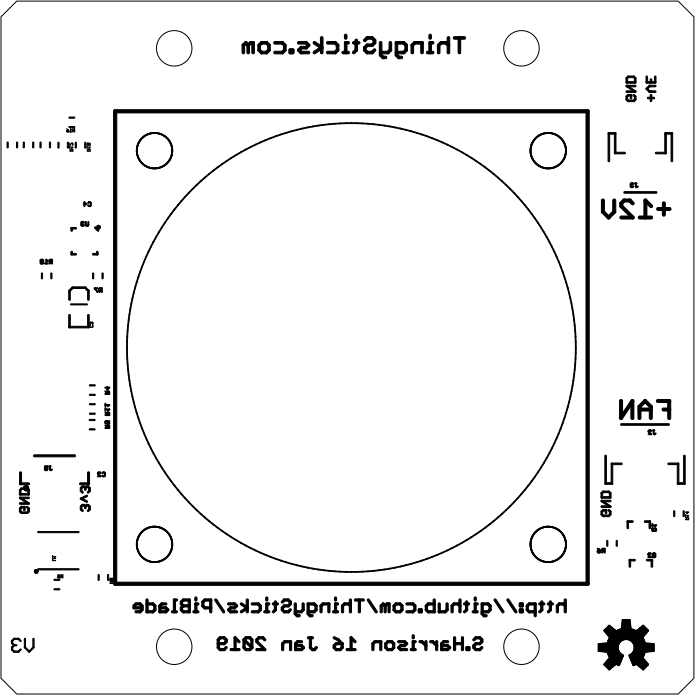
FrontPanels/McPiFace/Images/Fan-V3/bottom_silkscreen.png
