ThingySticks/PiBlade/FrontPanels/McPiFace/Images/Fan-V3/mill.png

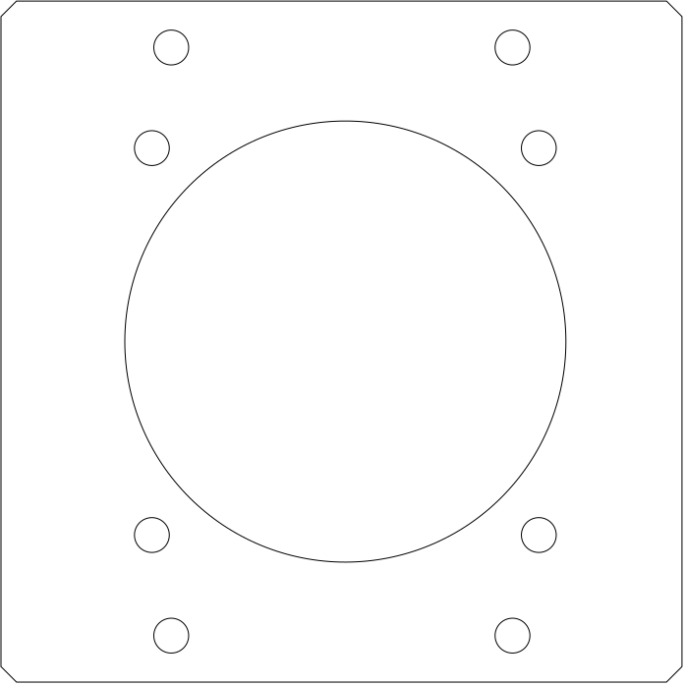
FrontPanels/McPiFace/Images/Fan-V3/mill.png
