ThingySticks/PiBlade/FrontPanels/McPiFace/Images/Fan-V3/PcbBottomDesign.png

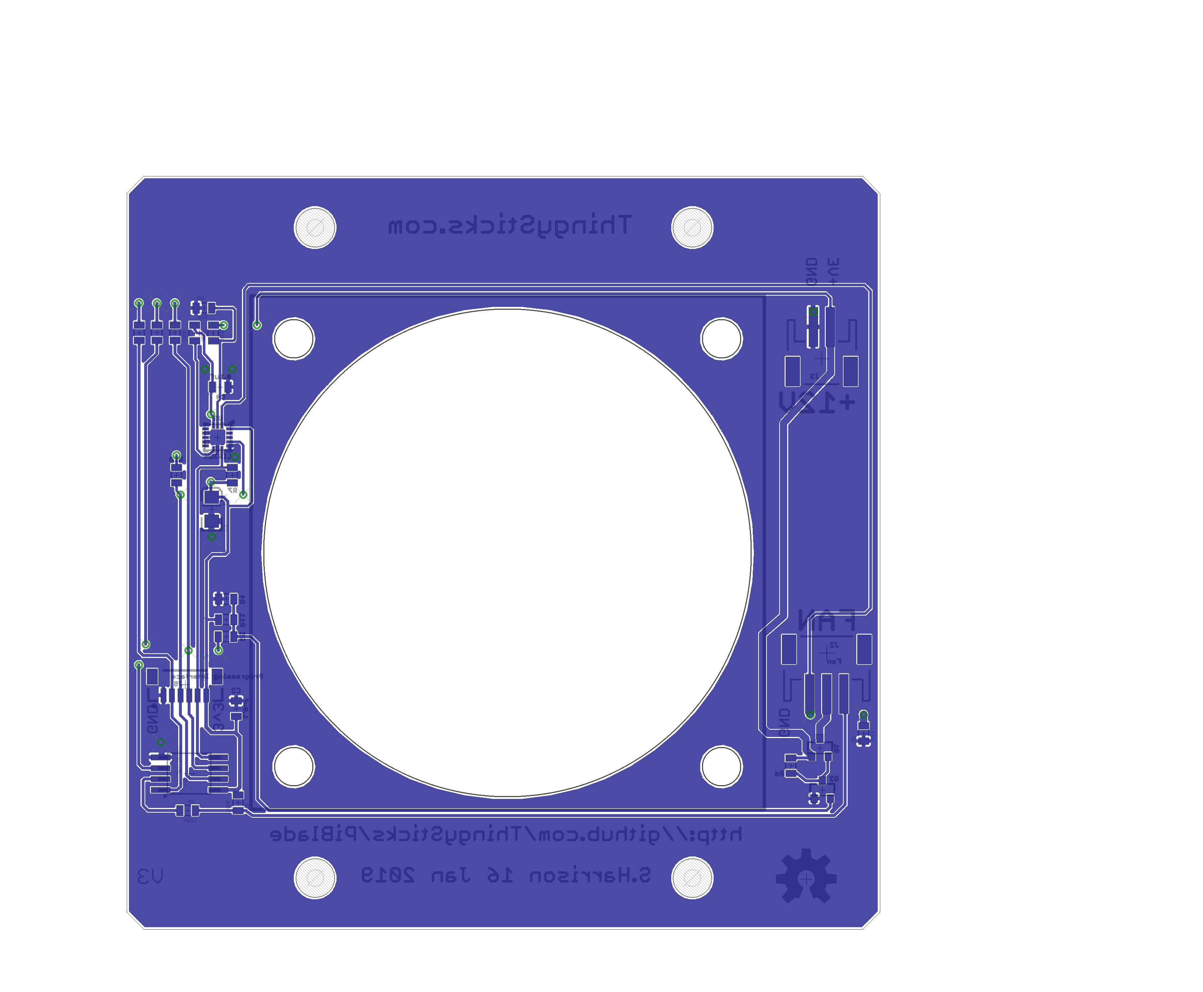
FrontPanels/McPiFace/Images/Fan-V3/PcbBottomDesign.png
