ThingySticks/PiBlade/FrontPanels/McPiFace/Images/Fan-V3/Schematic.png

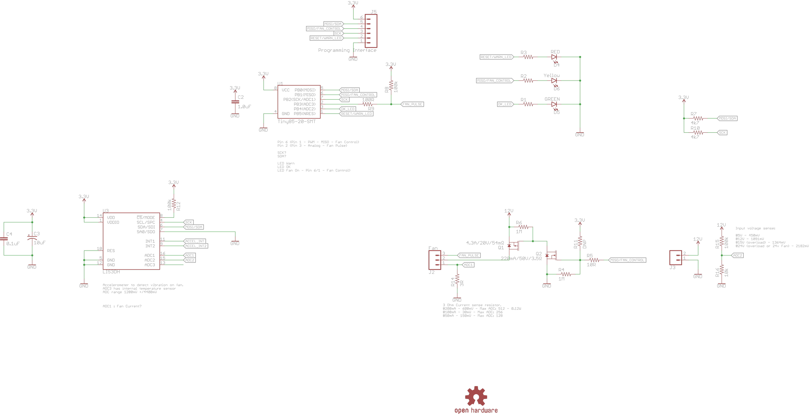
FrontPanels/McPiFace/Images/Fan-V3/Schematic.png
