ThingySticks/PiBlade/FrontPanels/McPiFace/Images/Fan-V3/top_copper.png

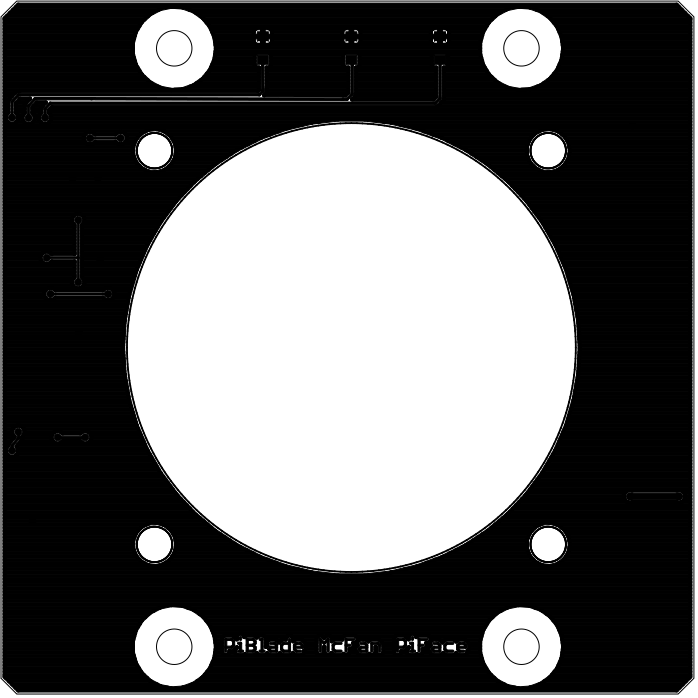
FrontPanels/McPiFace/Images/Fan-V3/top_copper.png
