ThingySticks/PiBlade/FrontPanels/McPiFace/Images/Fan-V3/top_silkscreen.png

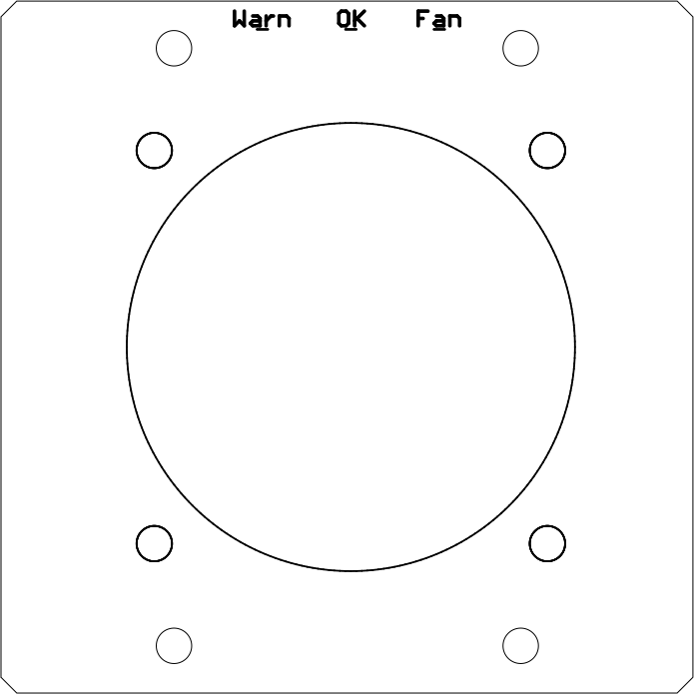
FrontPanels/McPiFace/Images/Fan-V3/top_silkscreen.png
