ThingySticks/PiBlade/FrontPanels/McPiFace/Images/MiniOled-USBCover/bottom.png

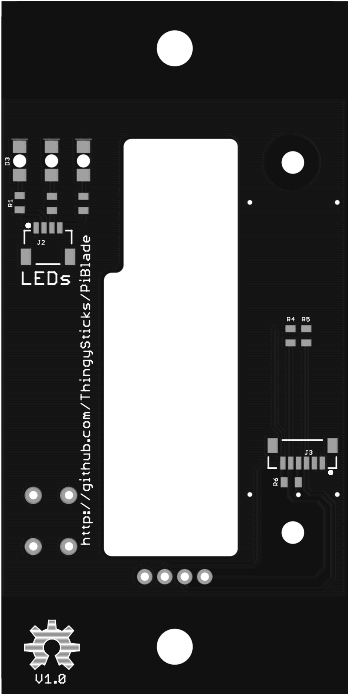
FrontPanels/McPiFace/Images/MiniOled-USBCover/bottom.png
