ThingySticks/PiBlade/FrontPanels/McPiFace/Images/MiniOled-USBCover/bottom_silkscreen.png

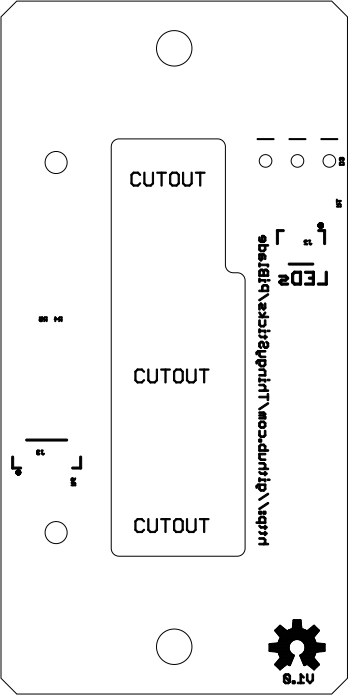
FrontPanels/McPiFace/Images/MiniOled-USBCover/bottom_silkscreen.png
