ThingySticks/PiBlade/FrontPanels/McPiFace/Images/MiniOled-USBCover/PcbAllLayersDesign.png

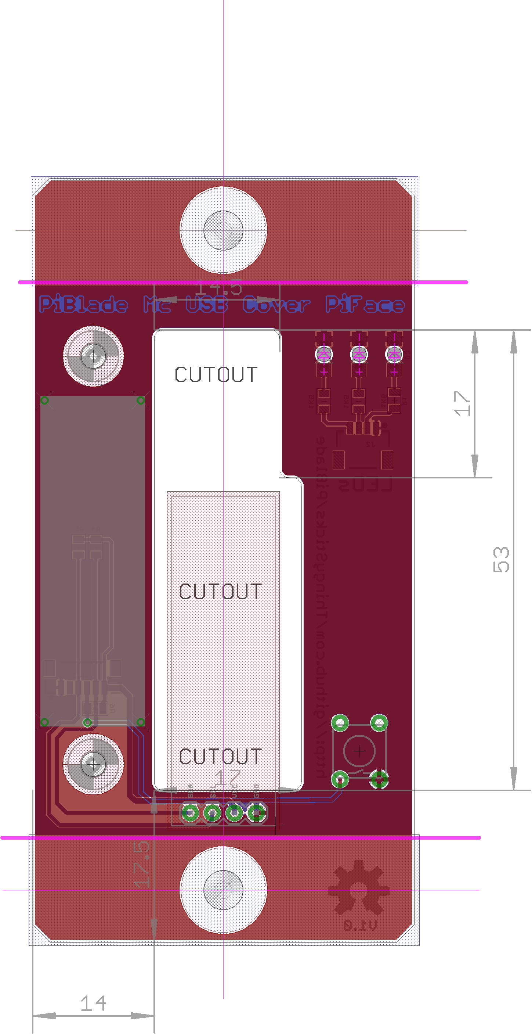
FrontPanels/McPiFace/Images/MiniOled-USBCover/PcbAllLayersDesign.png
