ThingySticks/PiBlade/FrontPanels/McPiFace/Images/MiniOled-USBCover/PcbBottomDesign.png

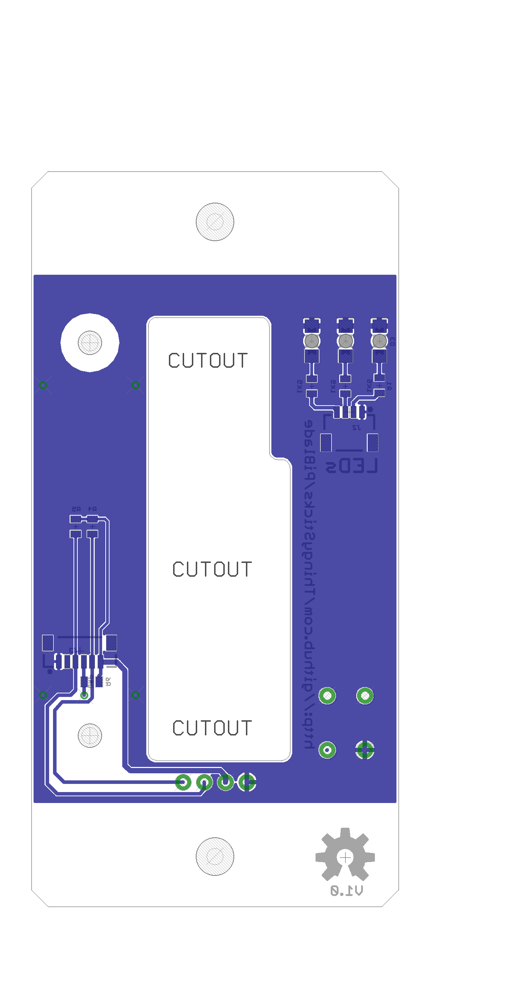
FrontPanels/McPiFace/Images/MiniOled-USBCover/PcbBottomDesign.png
