ThingySticks/PiBlade/FrontPanels/McPiFace/Images/MiniOled-USBCover/PcbTopDesign.png

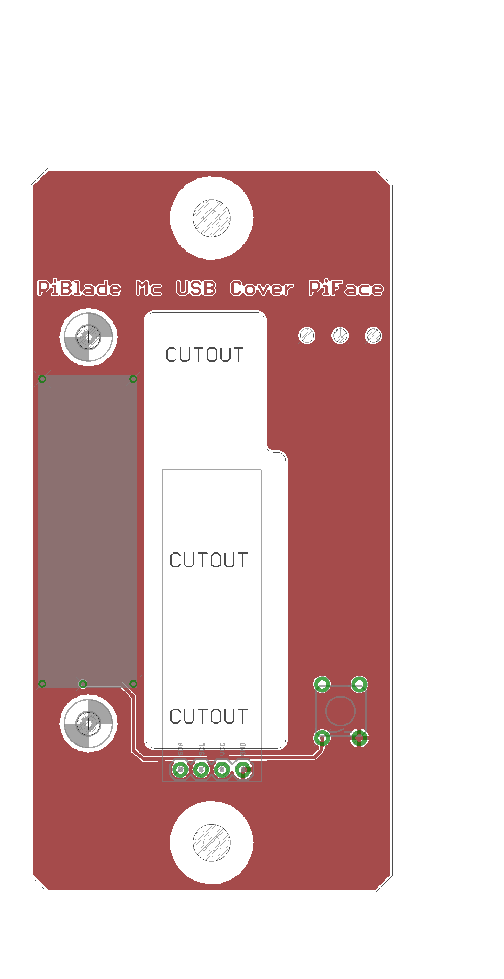
FrontPanels/McPiFace/Images/MiniOled-USBCover/PcbTopDesign.png
