ThingySticks/PiBlade/FrontPanels/McPiFace/Images/MiniOled-USBCover/Schematic.png

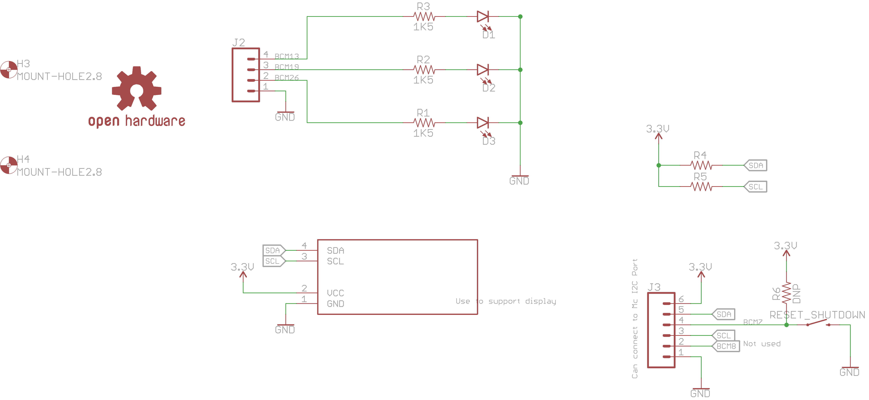
FrontPanels/McPiFace/Images/MiniOled-USBCover/Schematic.png
