ThingySticks/PiBlade/FrontPanels/McPiFace/Images/MiniOled-USBCover/top (1).png

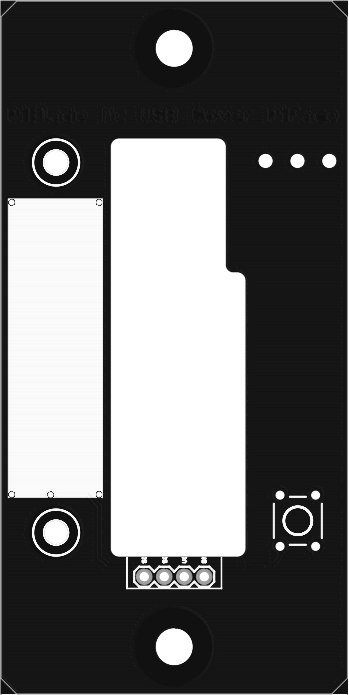
FrontPanels/McPiFace/Images/MiniOled-USBCover/top (1).png
