ThingySticks/PiBlade/FrontPanels/McPiFace/Images/MiniOled-USBCover/top_silkscreen.png

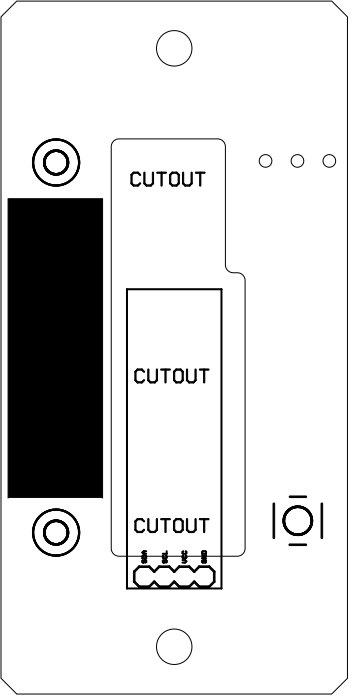
FrontPanels/McPiFace/Images/MiniOled-USBCover/top_silkscreen.png
