ThingySticks/PiBlade/FrontPanels/McPiFace/Images/MiniOled/bottom_silkscreen.png

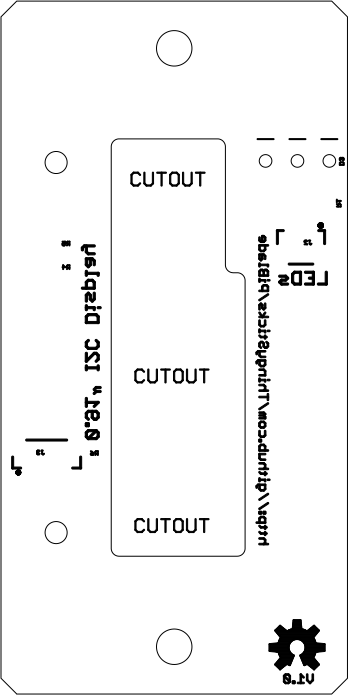
FrontPanels/McPiFace/Images/MiniOled/bottom_silkscreen.png
