ThingySticks/PiBlade/FrontPanels/McPiFace/Images/MiniOled/top.png

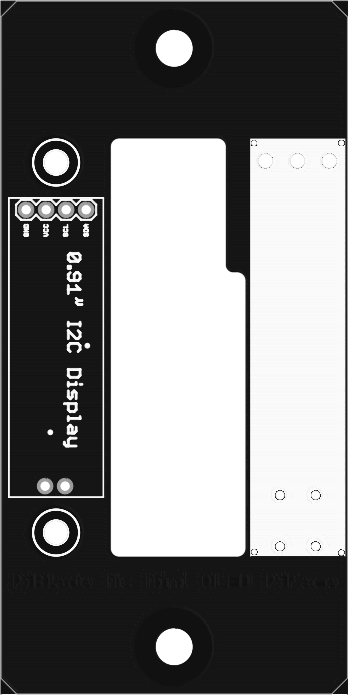
FrontPanels/McPiFace/Images/MiniOled/top.png
