ThingySticks/PiBlade/FrontPanels/McPiFace/Images/MiniOled/top_silkscreen.png

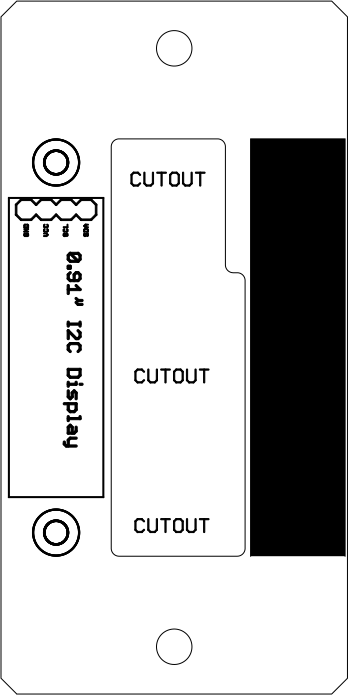
FrontPanels/McPiFace/Images/MiniOled/top_silkscreen.png
