ThingySticks/PiBlade/FrontPanels/McPiFace/Images/ParticleEthernet/PcbAllLayersDesign.png

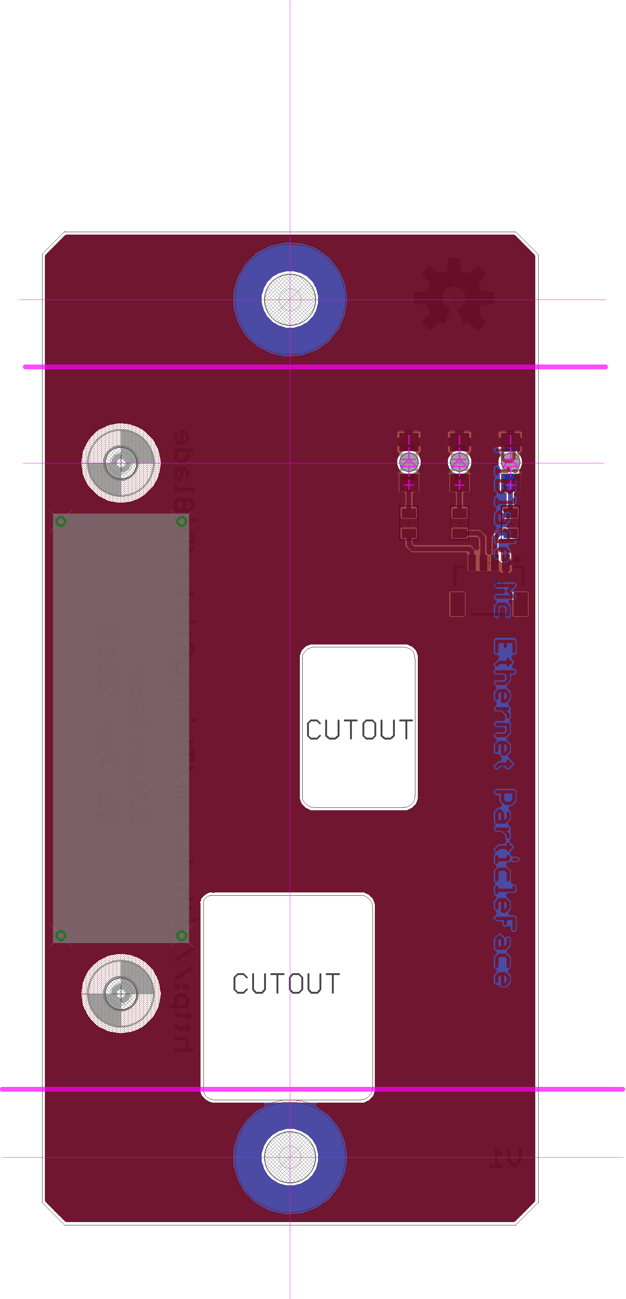
FrontPanels/McPiFace/Images/ParticleEthernet/PcbAllLayersDesign.png
