ThingySticks/PiBlade/FrontPanels/McPiFace/Images/ParticleEthernet/PcbBottomDesign.png

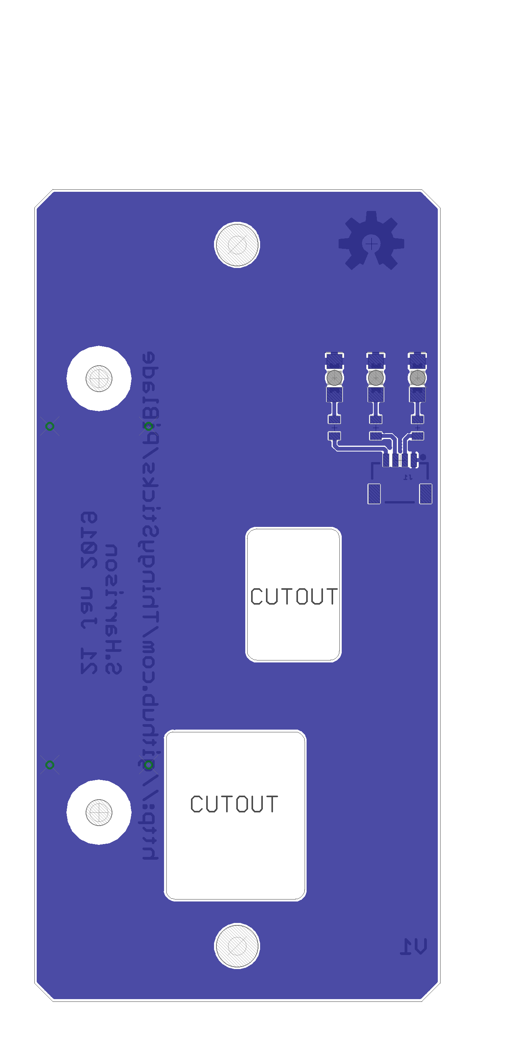
FrontPanels/McPiFace/Images/ParticleEthernet/PcbBottomDesign.png
