ThingySticks/PiBlade/FrontPanels/McPiFace/Images/RGB-V1/bottom.png

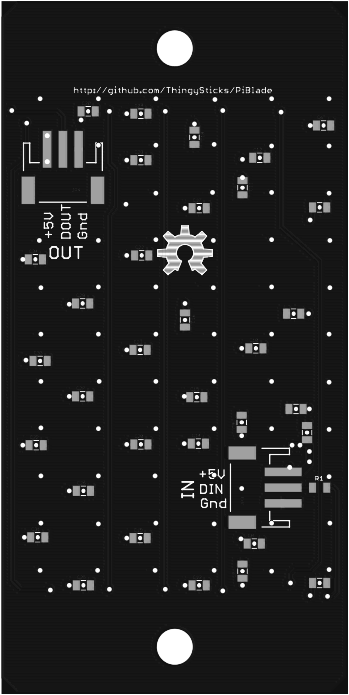
FrontPanels/McPiFace/Images/RGB-V1/bottom.png
