ThingySticks/PiBlade/FrontPanels/McPiFace/Images/RGB-V1/bottom_copper.png

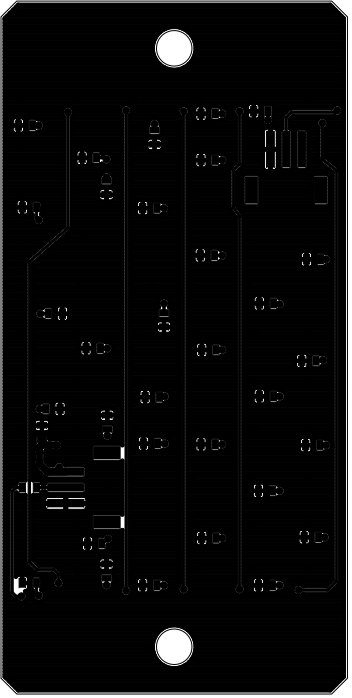
FrontPanels/McPiFace/Images/RGB-V1/bottom_copper.png
