ThingySticks/PiBlade/FrontPanels/McPiFace/Images/RGB-V1/bottom_silkscreen.png

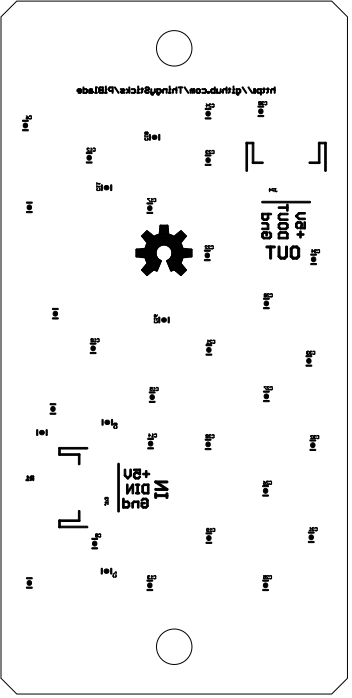
FrontPanels/McPiFace/Images/RGB-V1/bottom_silkscreen.png
