ThingySticks/PiBlade/FrontPanels/McPiFace/Images/RGB-V1/mill.png

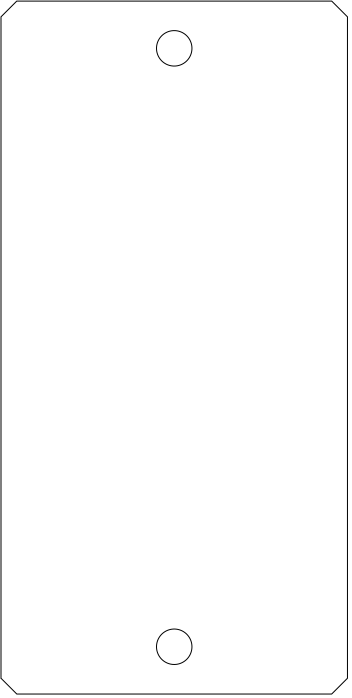
FrontPanels/McPiFace/Images/RGB-V1/mill.png
