ThingySticks/PiBlade/FrontPanels/McPiFace/Images/RGB-V1/PcbAllLayersDesign.png

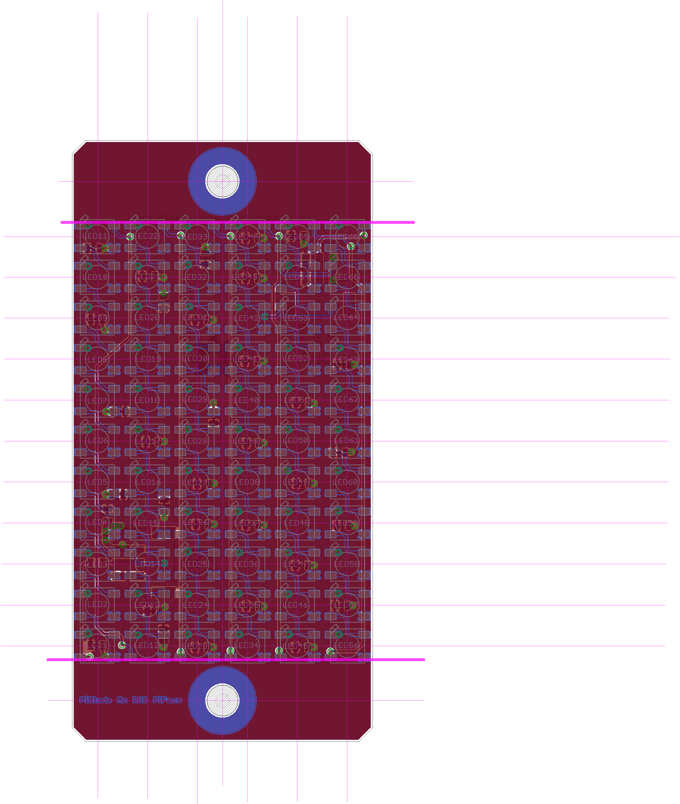
FrontPanels/McPiFace/Images/RGB-V1/PcbAllLayersDesign.png
