ThingySticks/PiBlade/FrontPanels/McPiFace/Images/RGB-V1/PcbBottomDesign.png

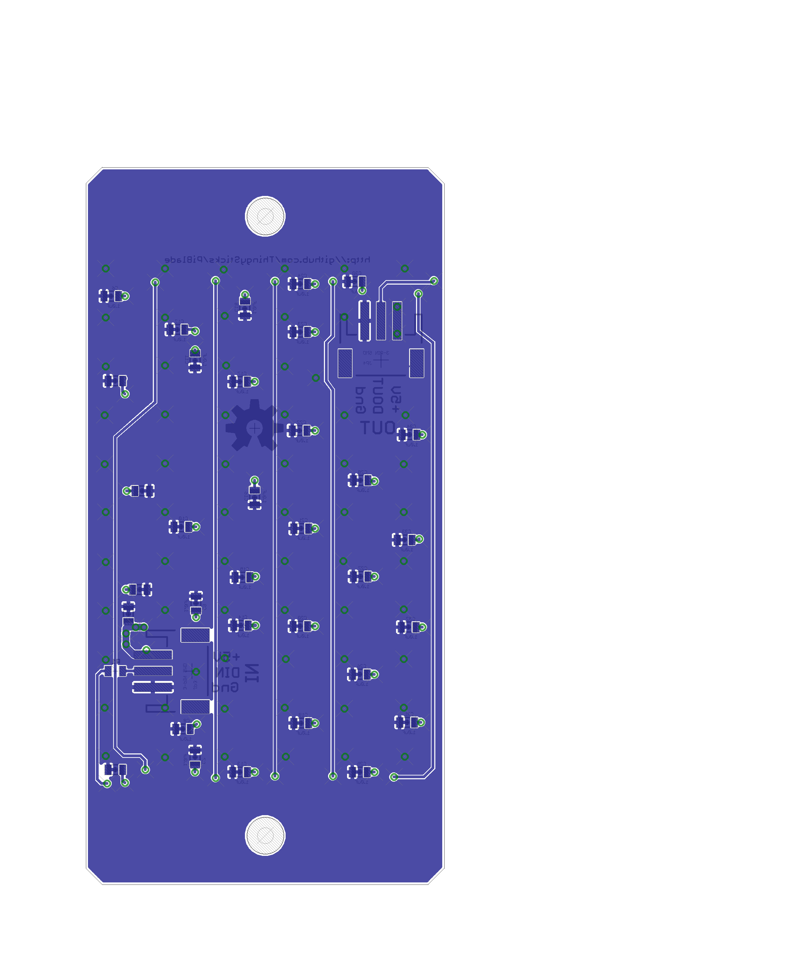
FrontPanels/McPiFace/Images/RGB-V1/PcbBottomDesign.png
