ThingySticks/PiBlade/FrontPanels/McPiFace/Images/RGB-V1/PcbTopDesign.png

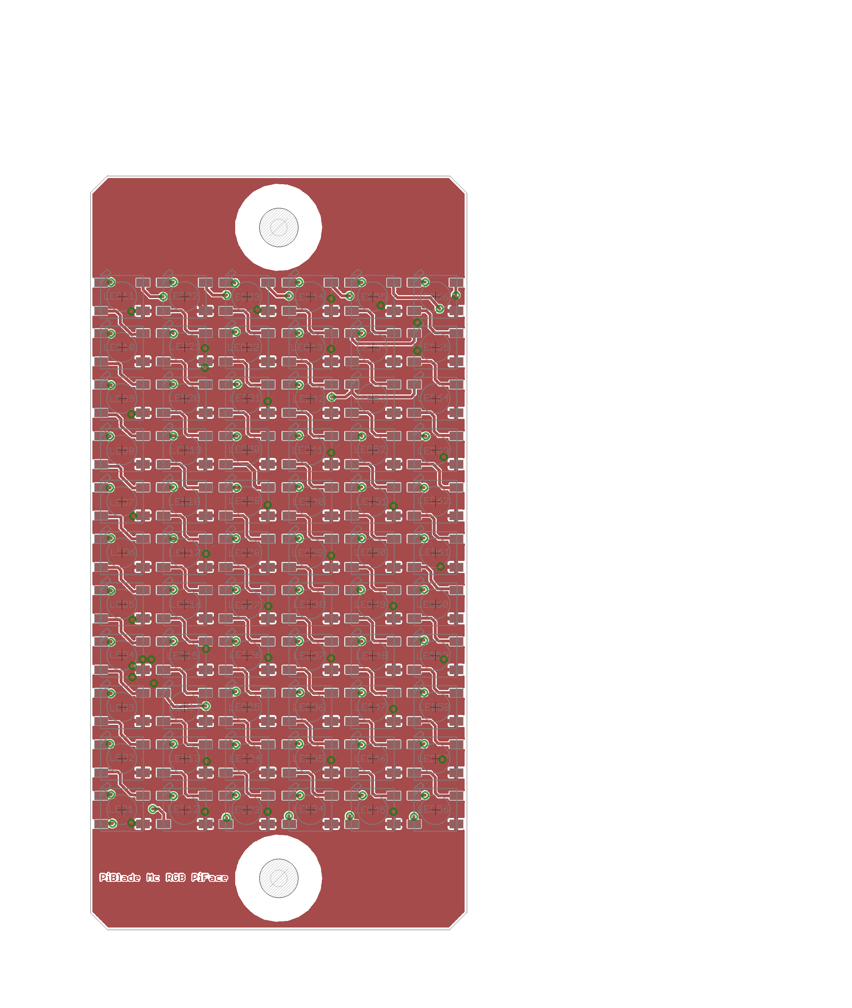
FrontPanels/McPiFace/Images/RGB-V1/PcbTopDesign.png
