ThingySticks/PiBlade/FrontPanels/McPiFace/Images/RGB-V1/top.png

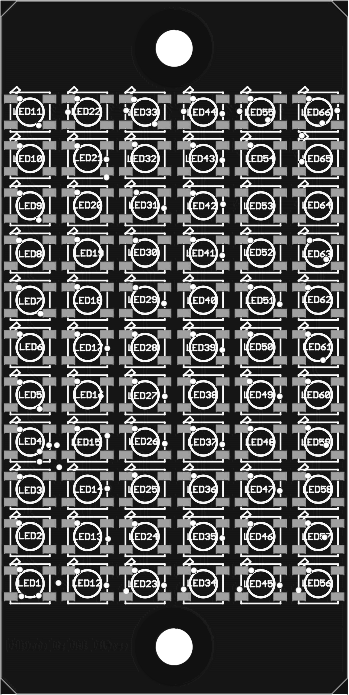
FrontPanels/McPiFace/Images/RGB-V1/top.png
