ThingySticks/PiBlade/FrontPanels/McPiFace/Images/RGB-V1/top_copper.png

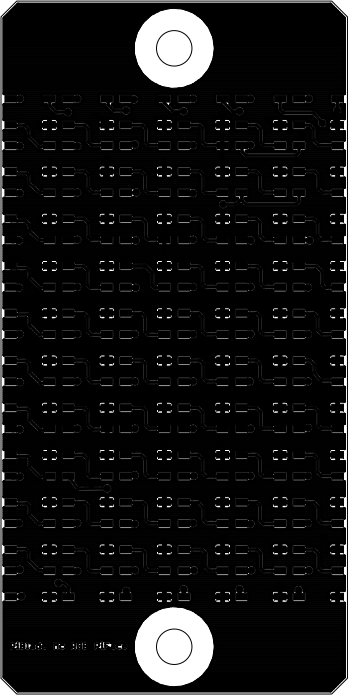
FrontPanels/McPiFace/Images/RGB-V1/top_copper.png
