ThingySticks/PiBlade/FrontPanels/McPiFace/Images/RGB-V1/top_silkscreen.png

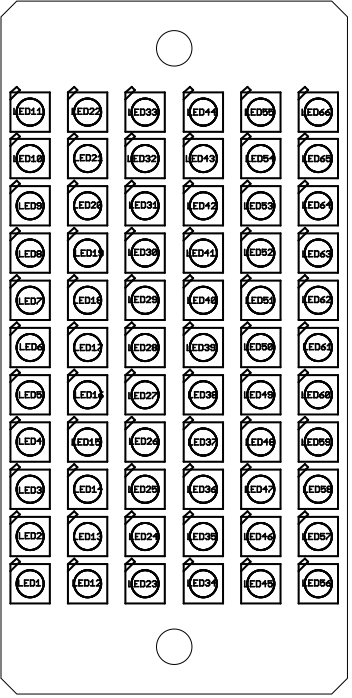
FrontPanels/McPiFace/Images/RGB-V1/top_silkscreen.png
