ThingySticks/PiBlade/FrontPanels/McPiFace/Images/SevenSegment/bottom.png

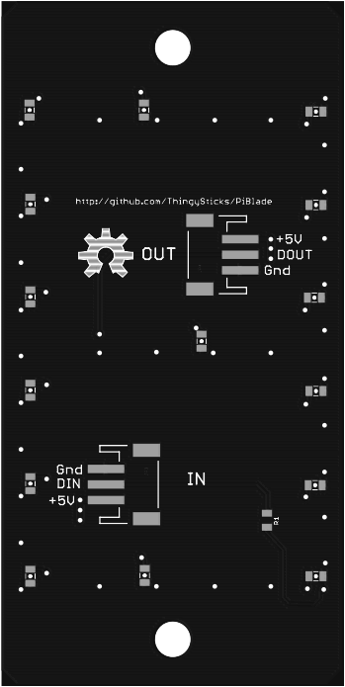
FrontPanels/McPiFace/Images/SevenSegment/bottom.png
