ThingySticks/PiBlade/FrontPanels/McPiFace/Images/SevenSegment/bottom_copper.png

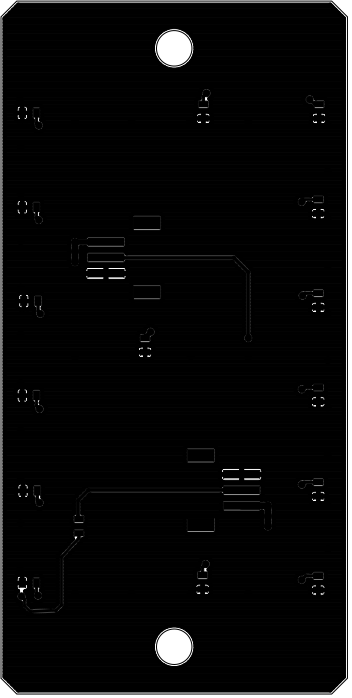
FrontPanels/McPiFace/Images/SevenSegment/bottom_copper.png
