ThingySticks/PiBlade/FrontPanels/McPiFace/Images/SevenSegment/bottom_silkscreen.png

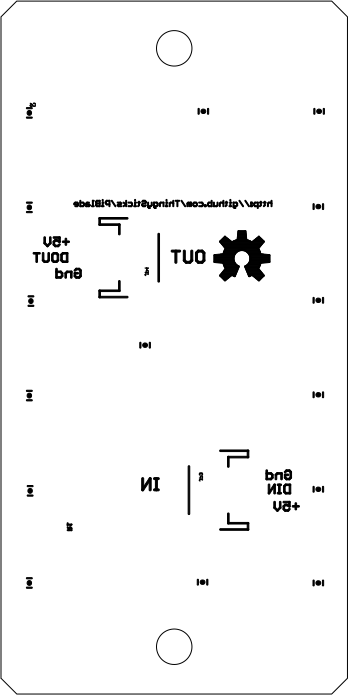
FrontPanels/McPiFace/Images/SevenSegment/bottom_silkscreen.png
