ThingySticks/PiBlade/FrontPanels/McPiFace/Images/SevenSegment/PcbAllLayersDesign.png

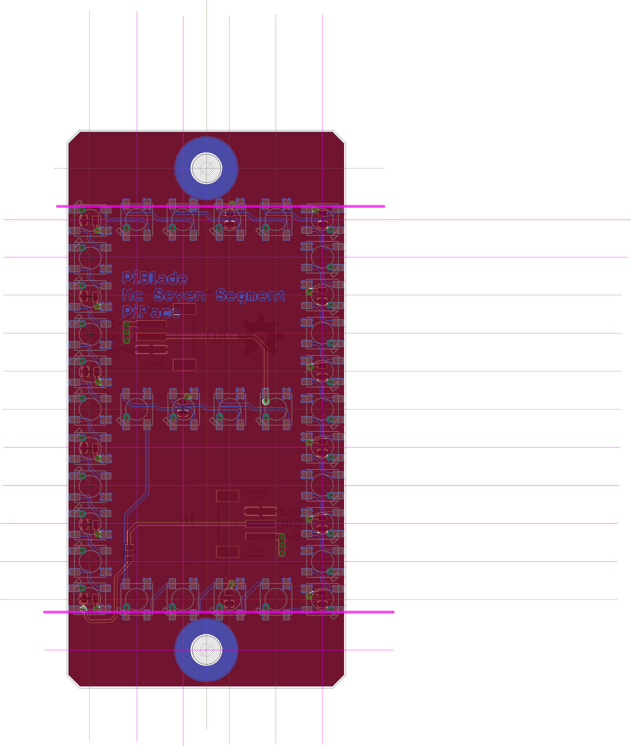
FrontPanels/McPiFace/Images/SevenSegment/PcbAllLayersDesign.png
