ThingySticks/PiBlade/FrontPanels/McPiFace/Images/SevenSegment/PcbBottomDesign.png

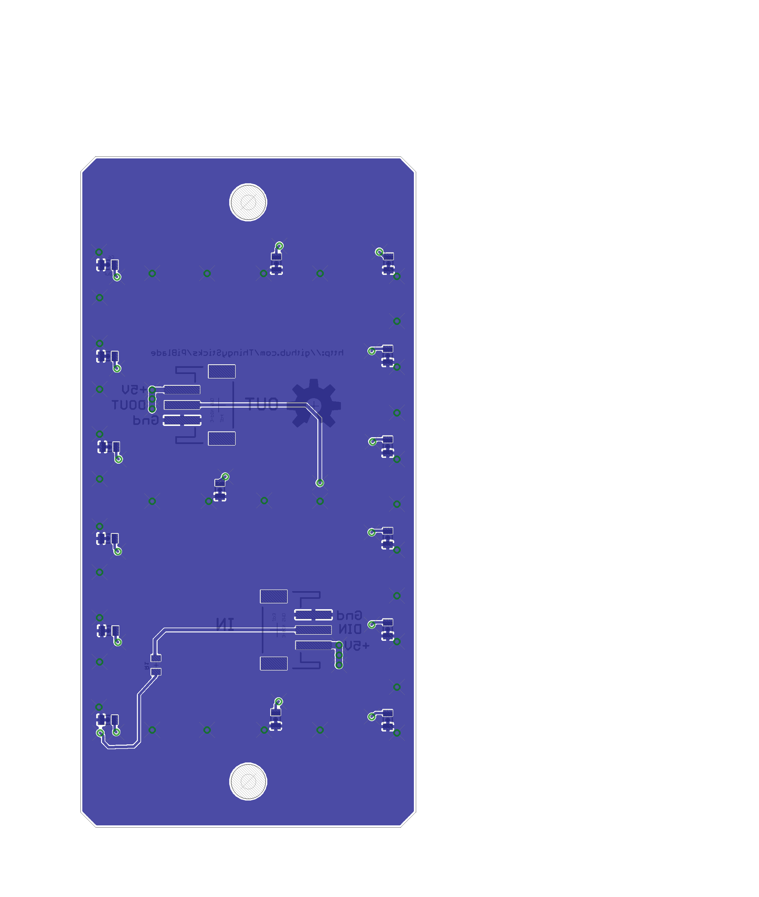
FrontPanels/McPiFace/Images/SevenSegment/PcbBottomDesign.png
