ThingySticks/PiBlade/FrontPanels/McPiFace/Images/SevenSegment/Schematic.png

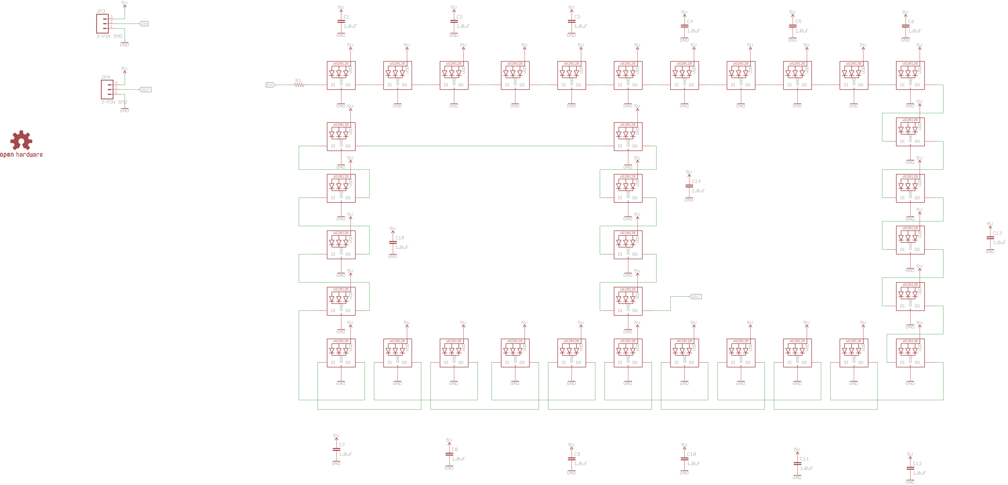
FrontPanels/McPiFace/Images/SevenSegment/Schematic.png
