ThingySticks/PiBlade/FrontPanels/McPiFace/Images/SevenSegment/top.png

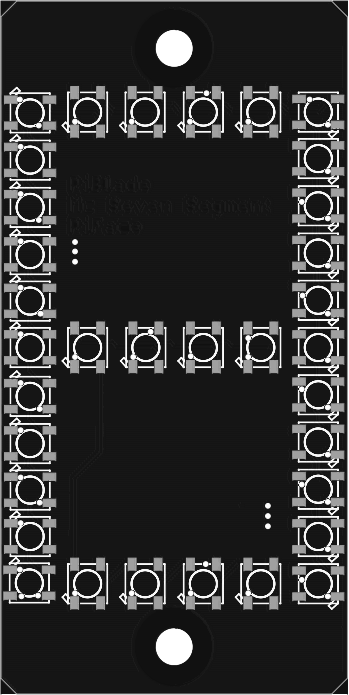
FrontPanels/McPiFace/Images/SevenSegment/top.png
