ThingySticks/PiBlade/FrontPanels/McPiFace/Images/SevenSegment/top_copper.png

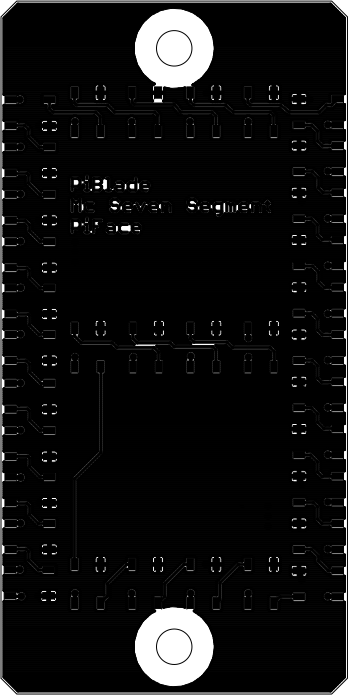
FrontPanels/McPiFace/Images/SevenSegment/top_copper.png
