ThingySticks/PiBlade/FrontPanels/McPiFace/Images/SevenSegment/top_silkscreen.png

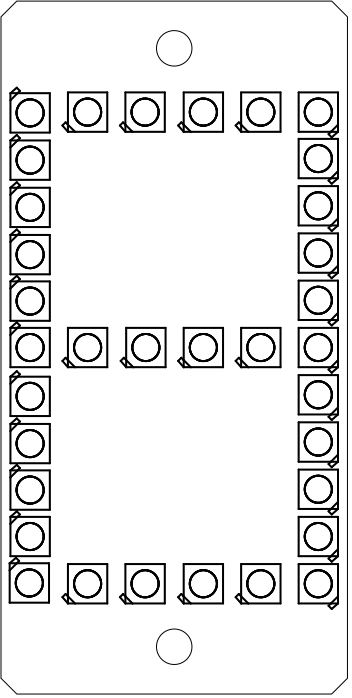
FrontPanels/McPiFace/Images/SevenSegment/top_silkscreen.png
