ThingySticks/PiBlade/FrontPanels/McPiFace/Images/Status/bottom.png

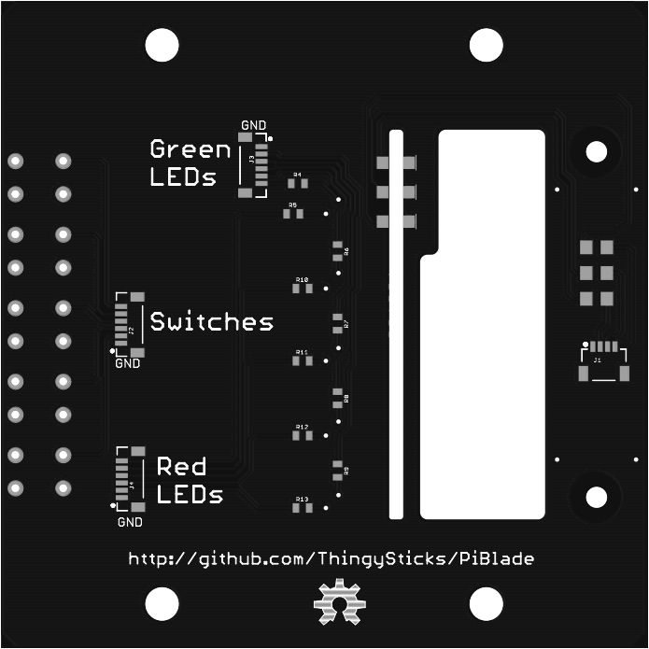
FrontPanels/McPiFace/Images/Status/bottom.png
