ThingySticks/PiBlade/FrontPanels/McPiFace/Images/Status/bottom_copper.png

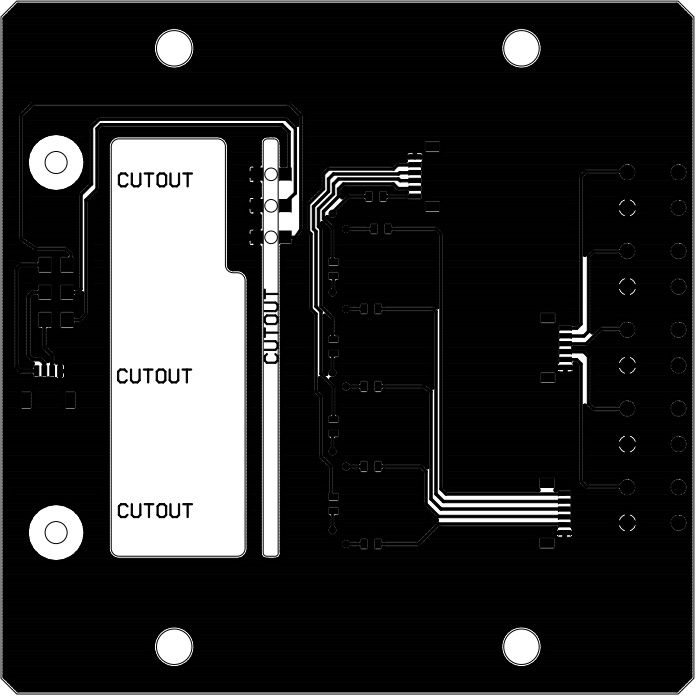
FrontPanels/McPiFace/Images/Status/bottom_copper.png
