ThingySticks/PiBlade/FrontPanels/McPiFace/Images/Status/bottom_silkscreen.png

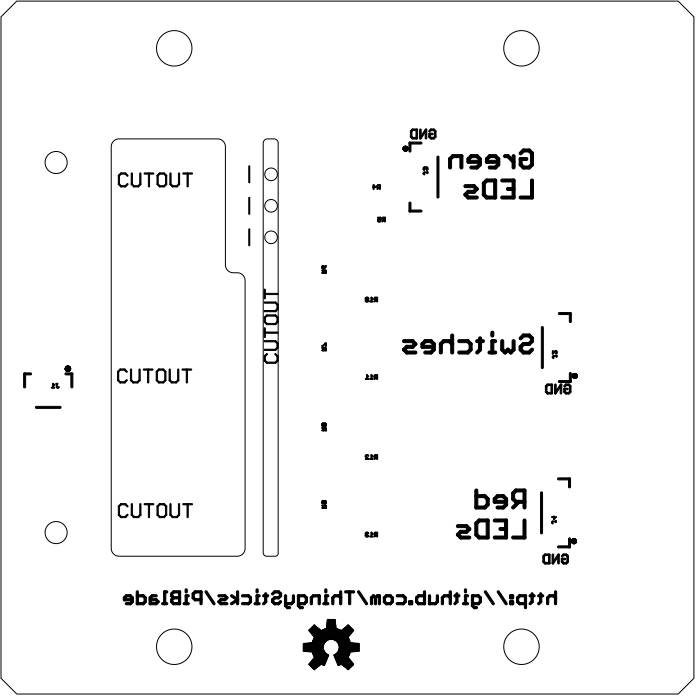
FrontPanels/McPiFace/Images/Status/bottom_silkscreen.png
