ThingySticks/PiBlade/FrontPanels/McPiFace/Images/Status/mill.png

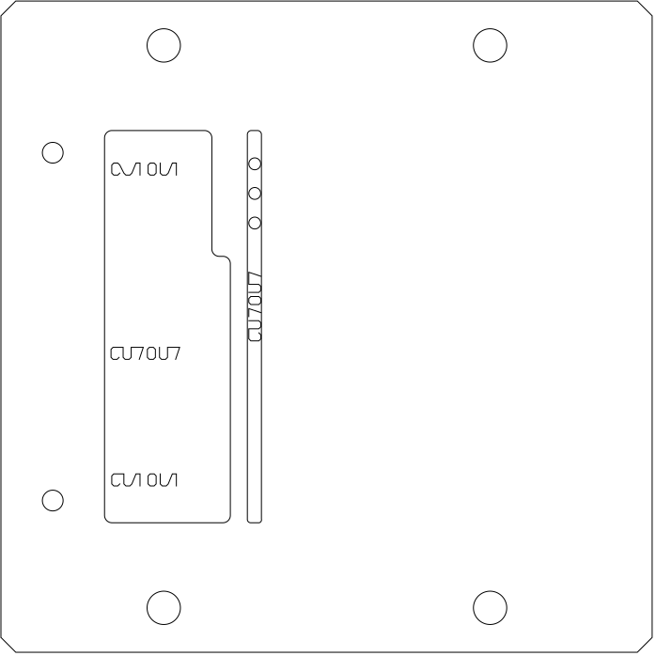
FrontPanels/McPiFace/Images/Status/mill.png
