ThingySticks/PiBlade/FrontPanels/McPiFace/Images/Status/PcbAllLayersDesign.png

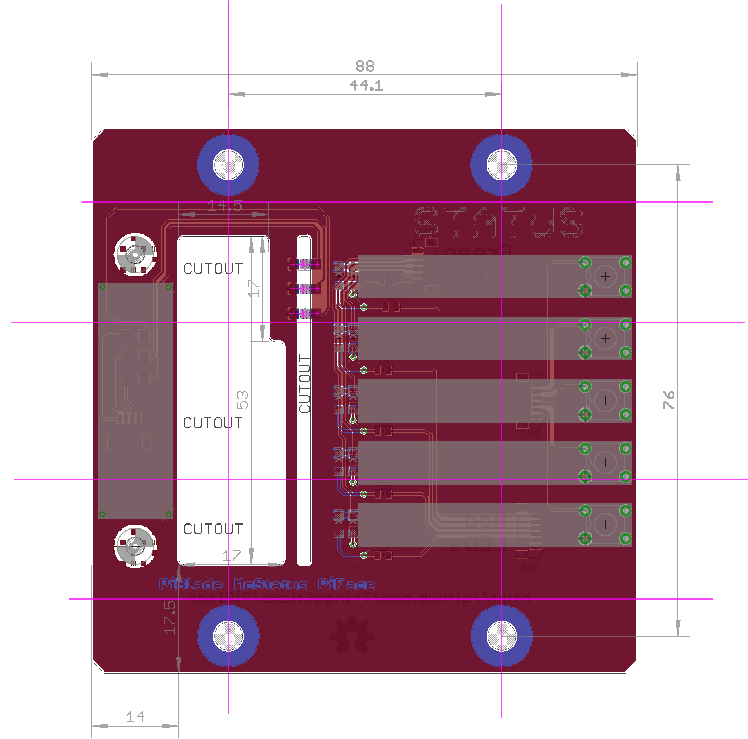
FrontPanels/McPiFace/Images/Status/PcbAllLayersDesign.png
