ThingySticks/PiBlade/FrontPanels/McPiFace/Images/Status/PcbBottomDesign.png

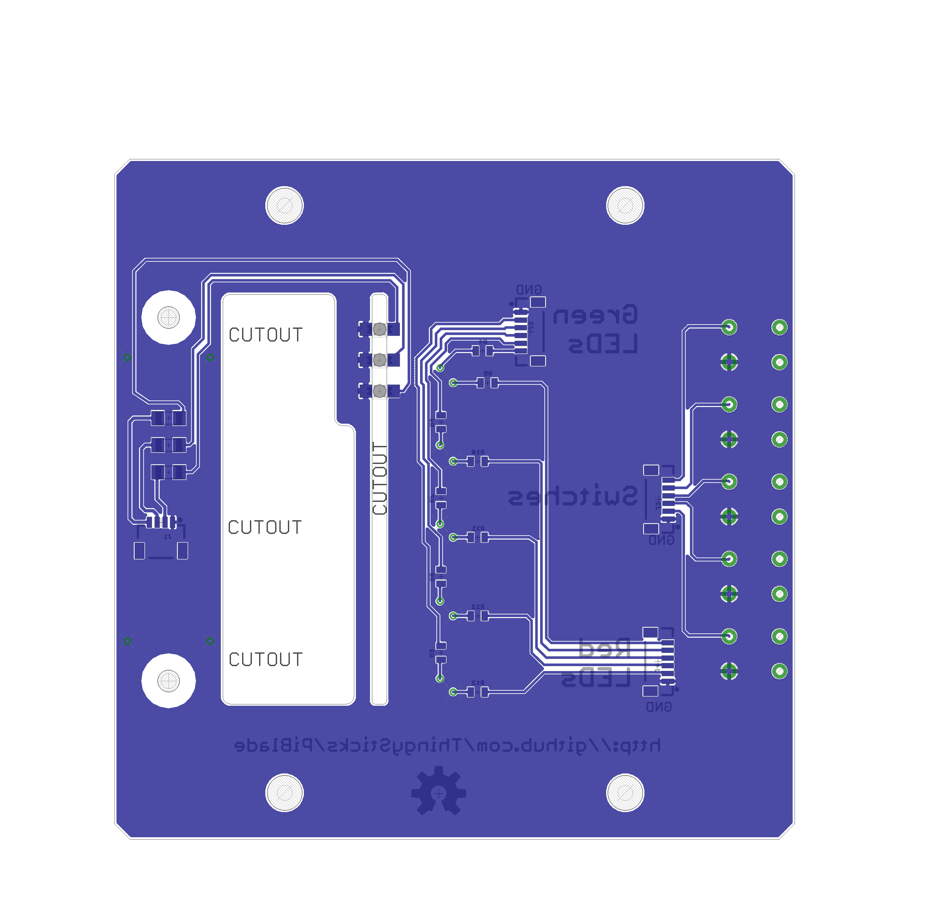
FrontPanels/McPiFace/Images/Status/PcbBottomDesign.png
