ThingySticks/PiBlade/FrontPanels/McPiFace/Images/Status/PcbTopDesign.png

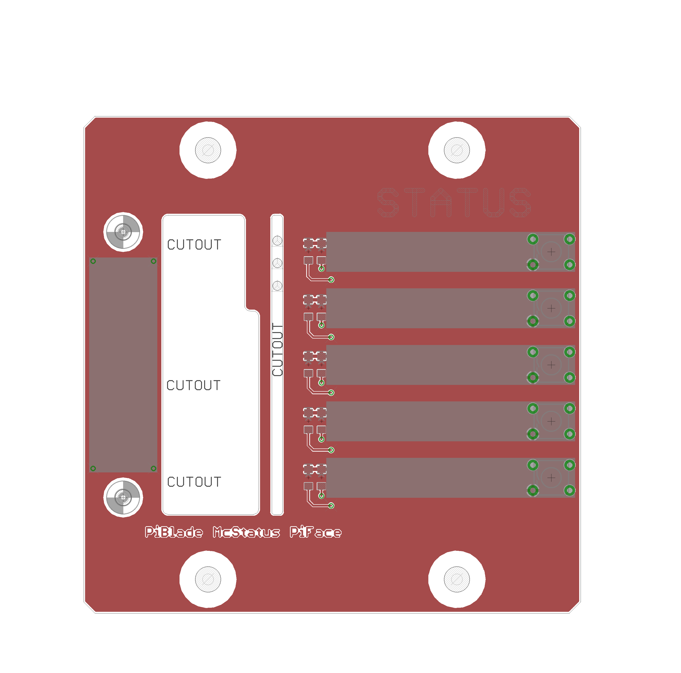
FrontPanels/McPiFace/Images/Status/PcbTopDesign.png
