ThingySticks/PiBlade/FrontPanels/McPiFace/Images/Status/Schematic.png

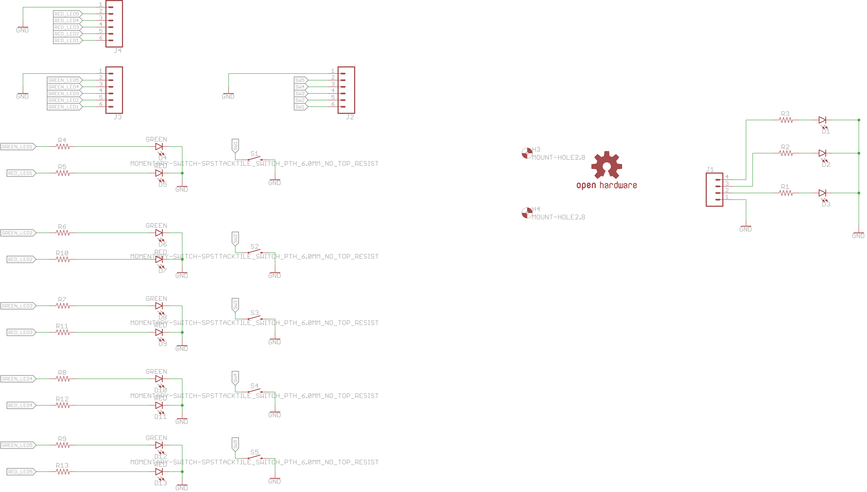
FrontPanels/McPiFace/Images/Status/Schematic.png
