ThingySticks/PiBlade/FrontPanels/McPiFace/Images/Status/top.png

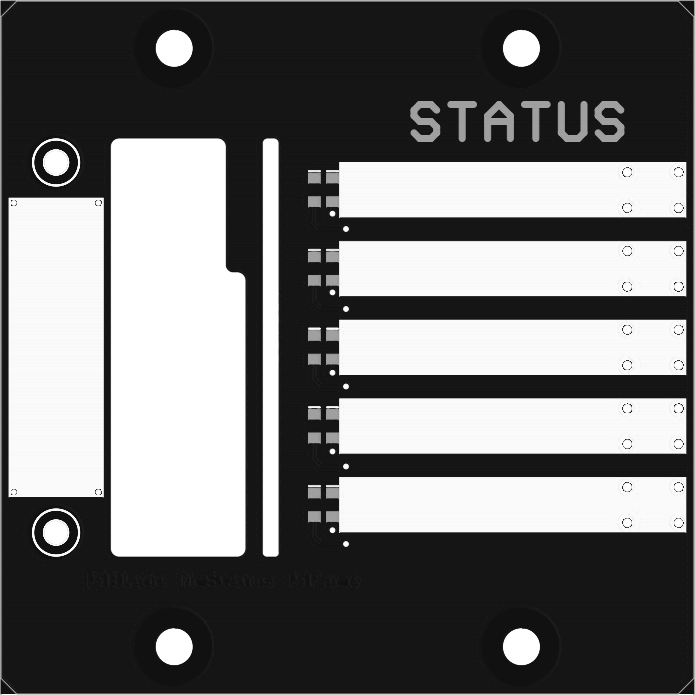
FrontPanels/McPiFace/Images/Status/top.png
