ThingySticks/PiBlade/FrontPanels/McPiFace/Images/Status/top_copper.png

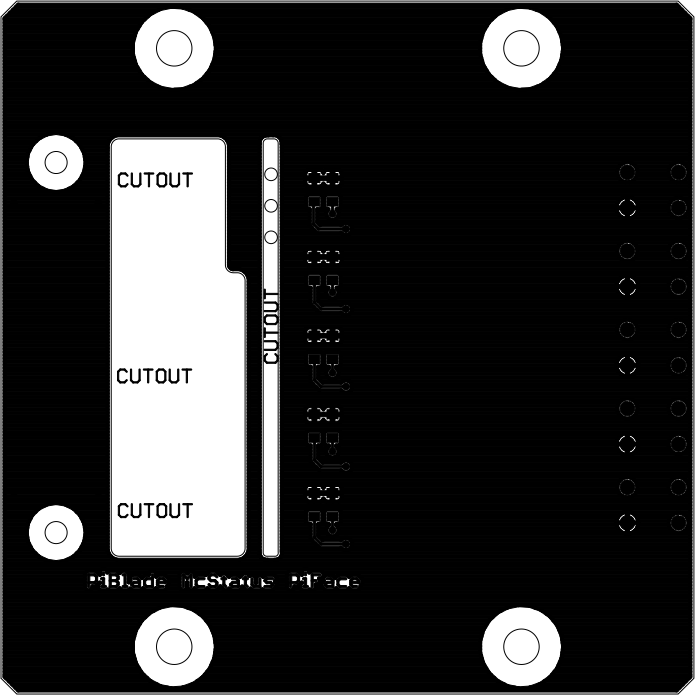
FrontPanels/McPiFace/Images/Status/top_copper.png
