ThingySticks/PiBlade/FrontPanels/McPiFace/Images/Status/top_silkscreen.png

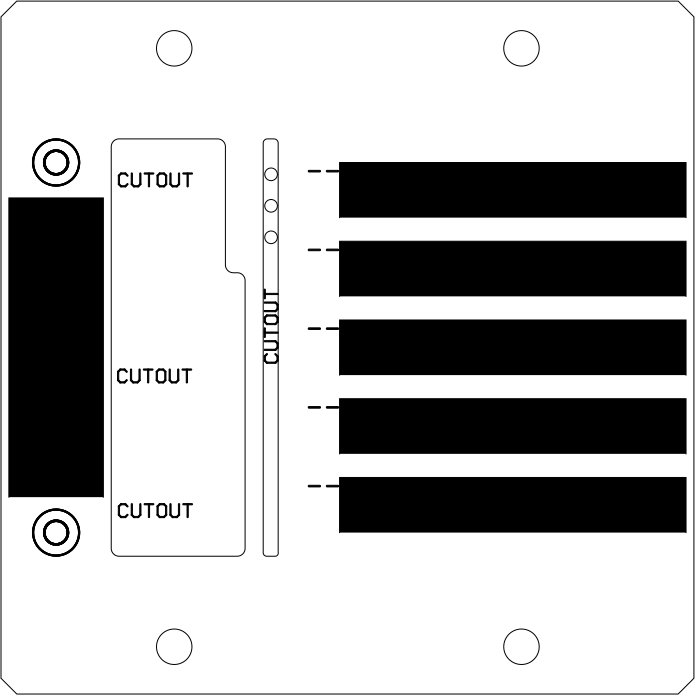
FrontPanels/McPiFace/Images/Status/top_silkscreen.png
