ThingySticks/PiBlade/FrontPanels/McPiFace/Images/TFT/bottom.png

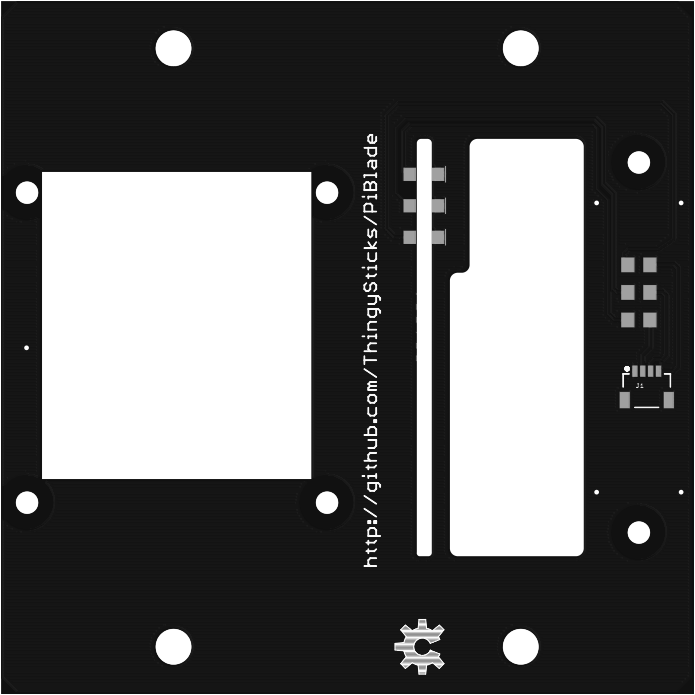
FrontPanels/McPiFace/Images/TFT/bottom.png
