ThingySticks/PiBlade/FrontPanels/McPiFace/Images/TFT/bottom_copper.png

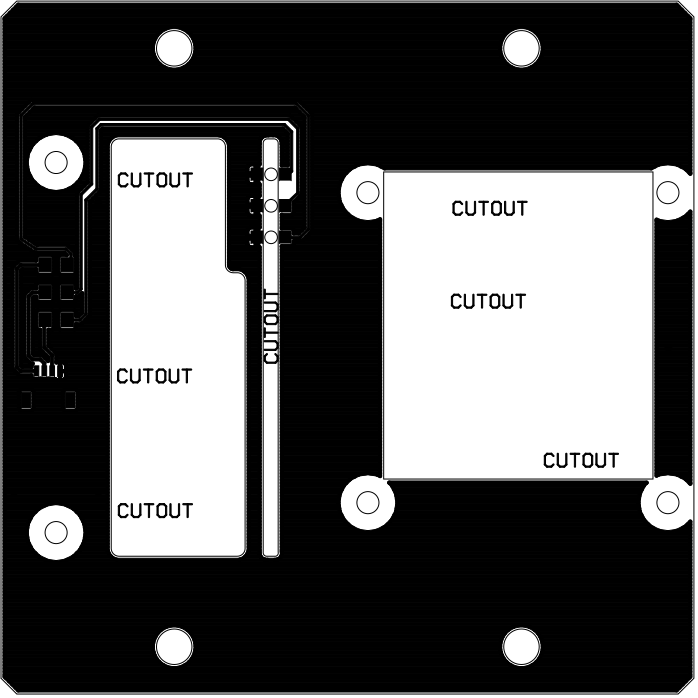
FrontPanels/McPiFace/Images/TFT/bottom_copper.png
