ThingySticks/PiBlade/FrontPanels/McPiFace/Images/TFT/bottom_silkscreen.png

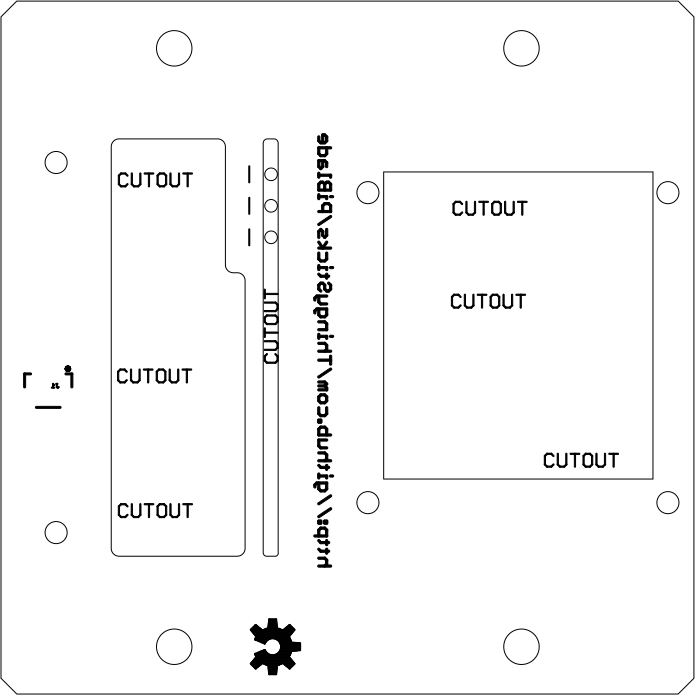
FrontPanels/McPiFace/Images/TFT/bottom_silkscreen.png
