ThingySticks/PiBlade/FrontPanels/McPiFace/Images/TFT/mill.png

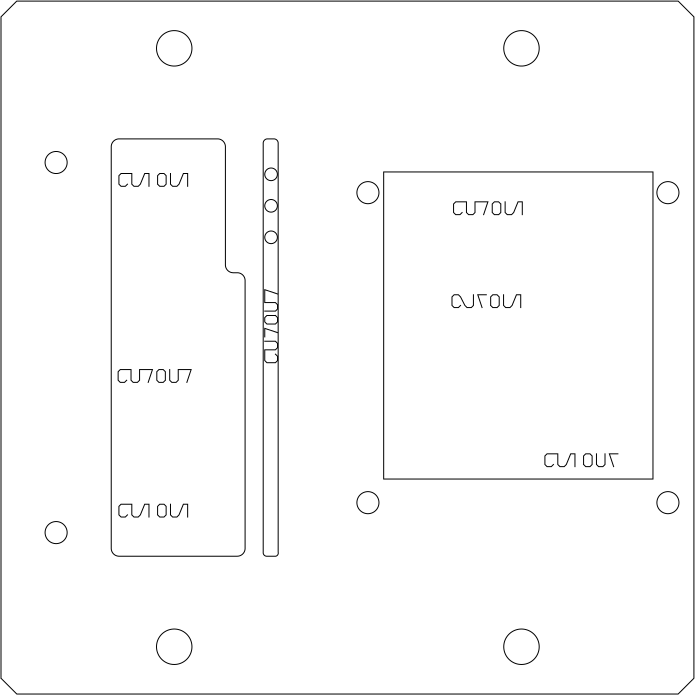
FrontPanels/McPiFace/Images/TFT/mill.png
