ThingySticks/PiBlade/FrontPanels/McPiFace/Images/TFT/PcbAllLayersDesign.png

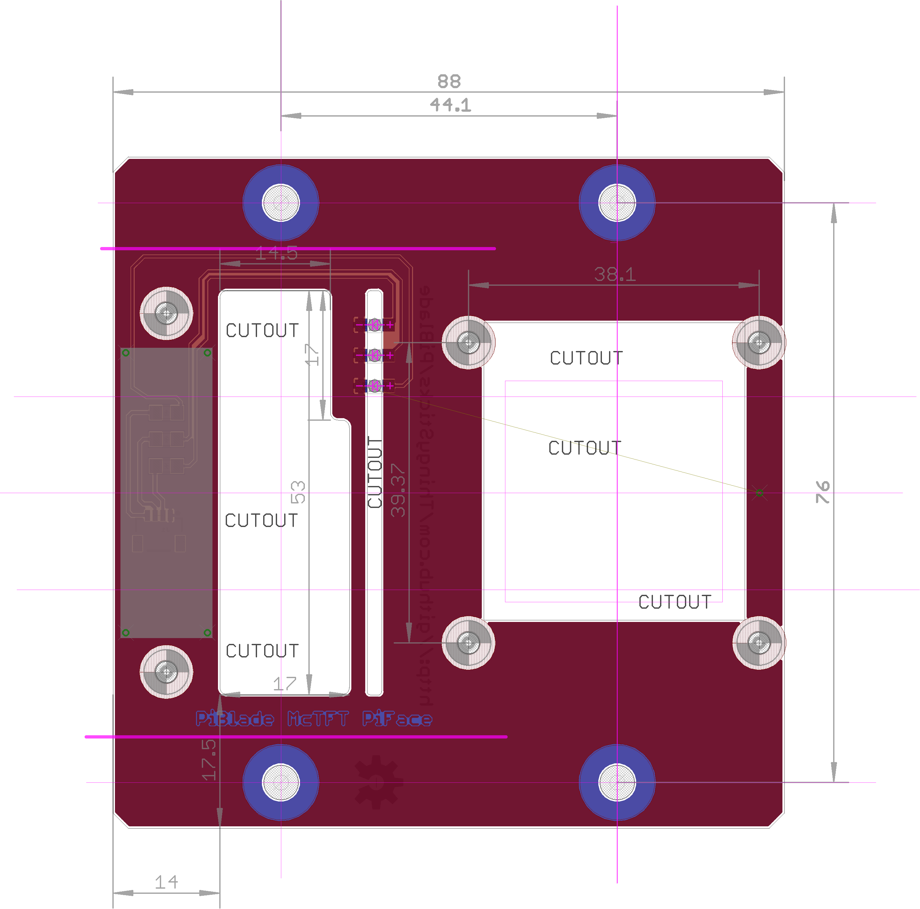
FrontPanels/McPiFace/Images/TFT/PcbAllLayersDesign.png
