ThingySticks/PiBlade/FrontPanels/McPiFace/Images/TFT/PcbBottomDesign.png

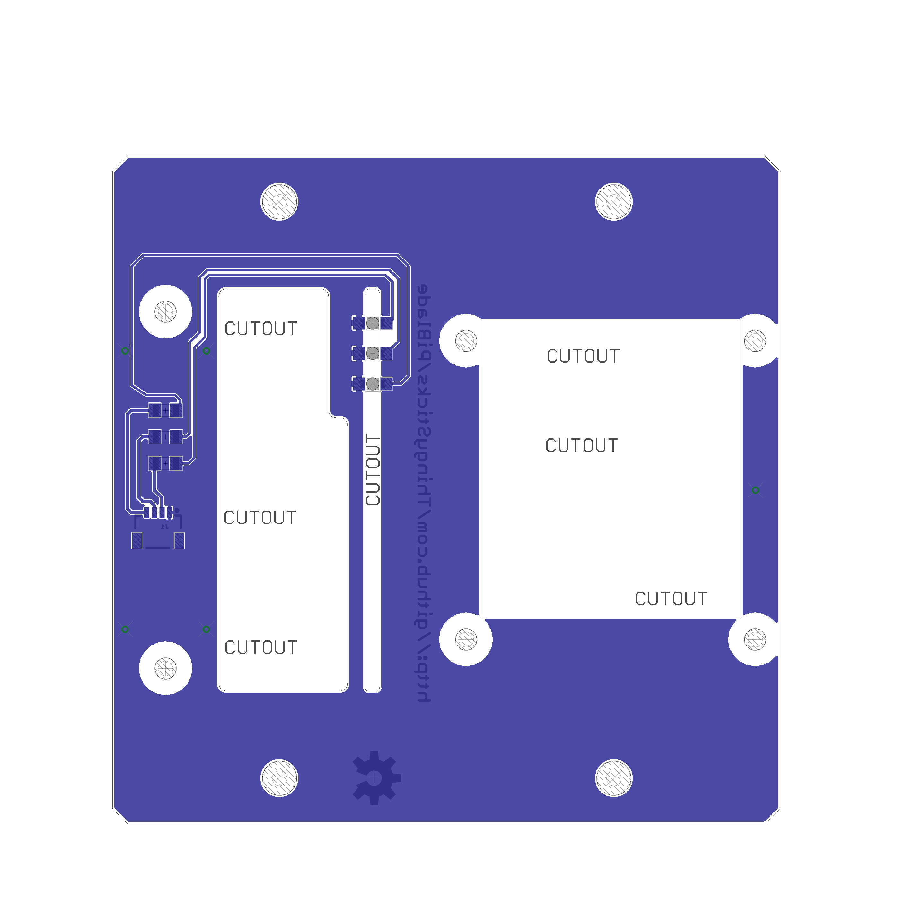
FrontPanels/McPiFace/Images/TFT/PcbBottomDesign.png
