ThingySticks/PiBlade/FrontPanels/McPiFace/Images/TFT/PcbTopDesign.png

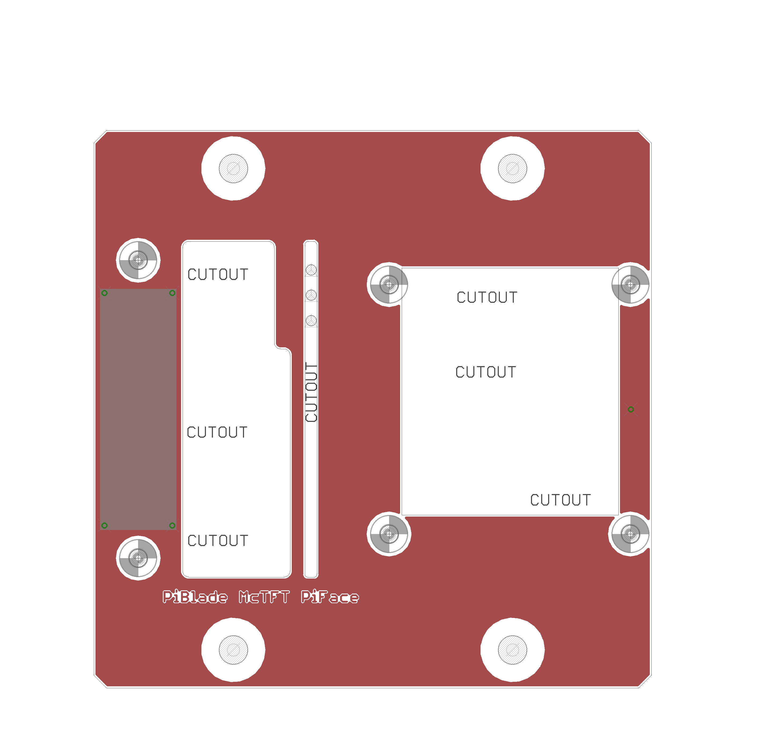
FrontPanels/McPiFace/Images/TFT/PcbTopDesign.png
