ThingySticks/PiBlade/FrontPanels/McPiFace/Images/TFT/Schematic.png

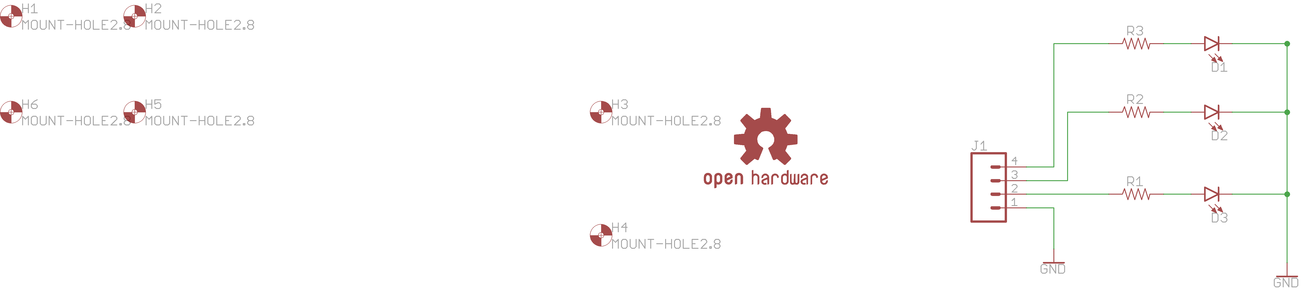
FrontPanels/McPiFace/Images/TFT/Schematic.png
