ThingySticks/PiBlade/FrontPanels/McPiFace/Images/TFT/top.png

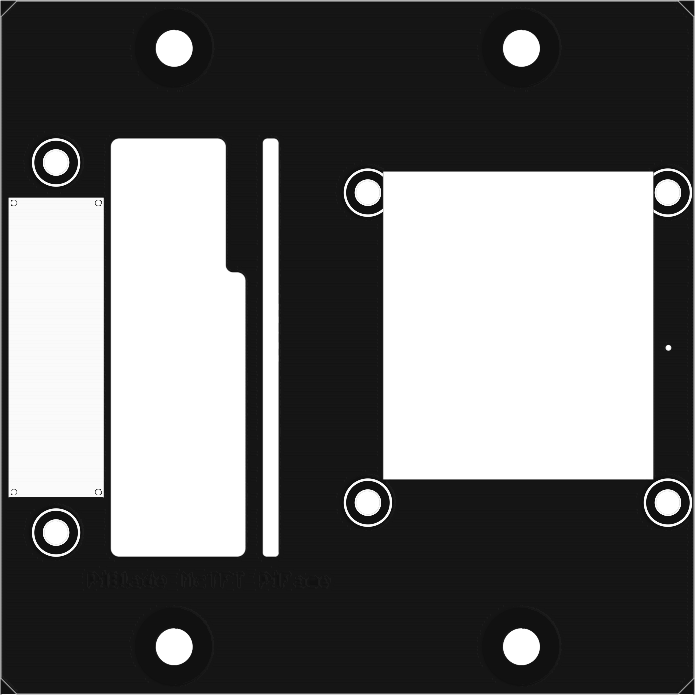
FrontPanels/McPiFace/Images/TFT/top.png
