ThingySticks/PiBlade/FrontPanels/McPiFace/Images/TFT/top_copper.png

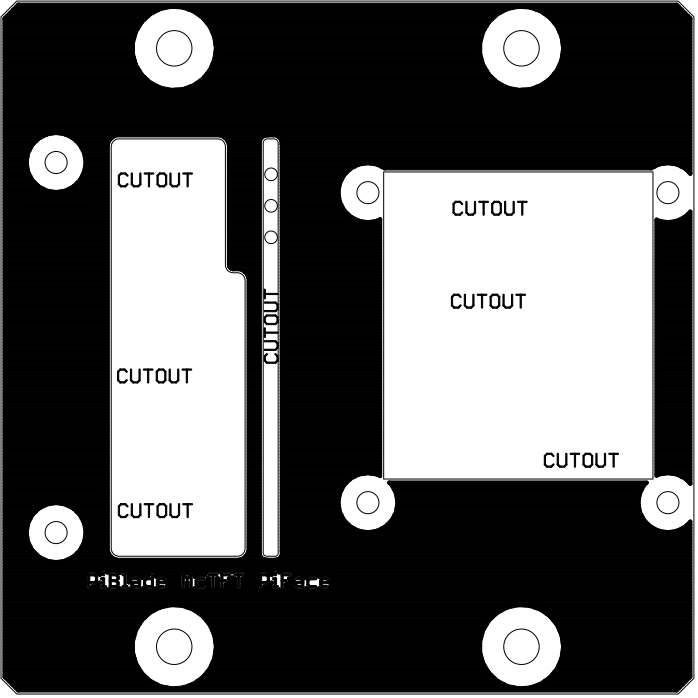
FrontPanels/McPiFace/Images/TFT/top_copper.png
