ThingySticks/PiBlade/FrontPanels/McPiFace/Images/TFT/top_silkscreen (1).png

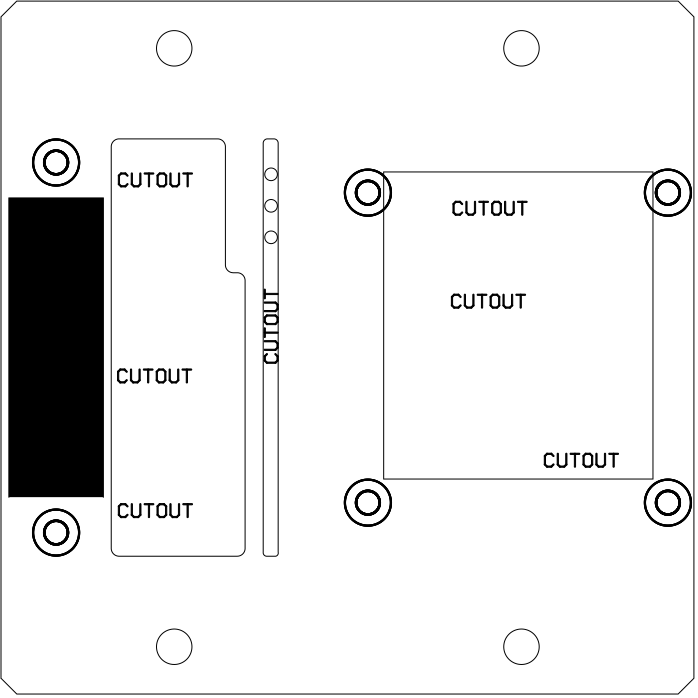
FrontPanels/McPiFace/Images/TFT/top_silkscreen (1).png
