ThingySticks/PiBlade/Boards/PSU/Images/bottom_soldermask.png

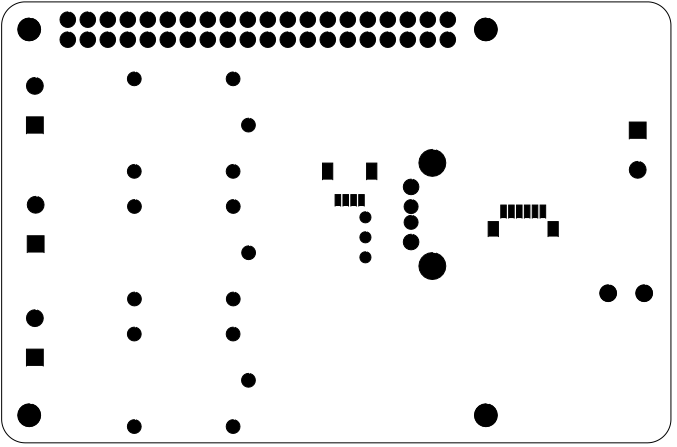
Boards/PSU/Images/bottom_soldermask.png
