ThingySticks/PiBlade/Boards/PSU/Images/top_soldermask.png

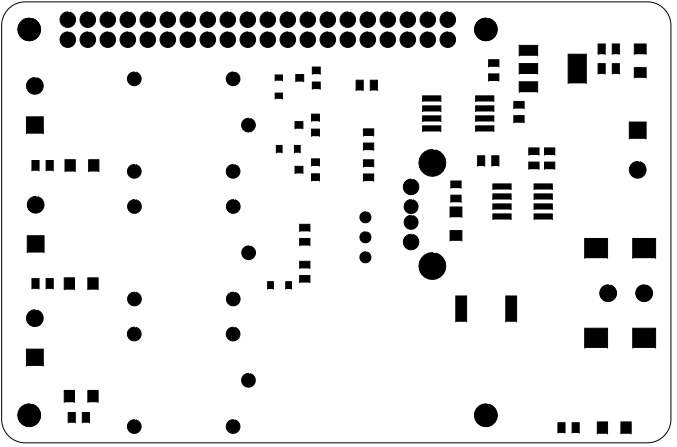
Boards/PSU/Images/top_soldermask.png
