ThingySticks/PiBlade/FrontPanels/McPiFace/Images/Environment-V1/top_soldermask.png

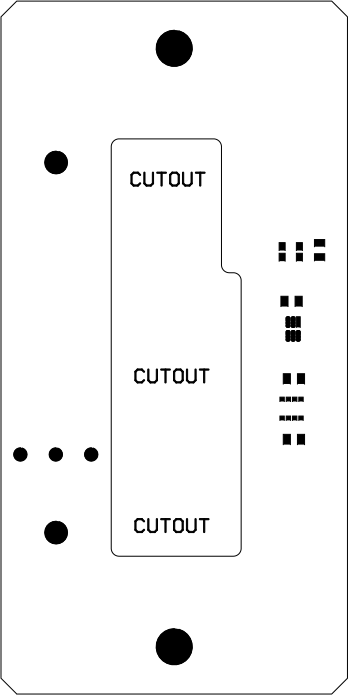
FrontPanels/McPiFace/Images/Environment-V1/top_soldermask.png
