ThingySticks/PiBlade/FrontPanels/McPiFace/Images/Status/top_soldermask.png

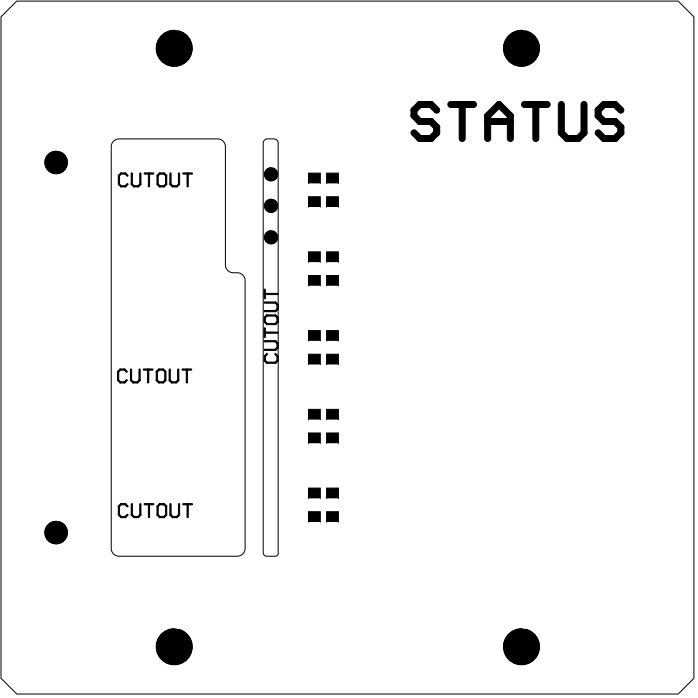
FrontPanels/McPiFace/Images/Status/top_soldermask.png
