ThingySticks/PiBlade/FrontPanels/McPiFace/McPiFace-60mmFan-V1.brd

## EAGLE design FrontPanels/McPiFace/McPiFace-60mmFan-V1.brd (2019-01-14, an earlier design)

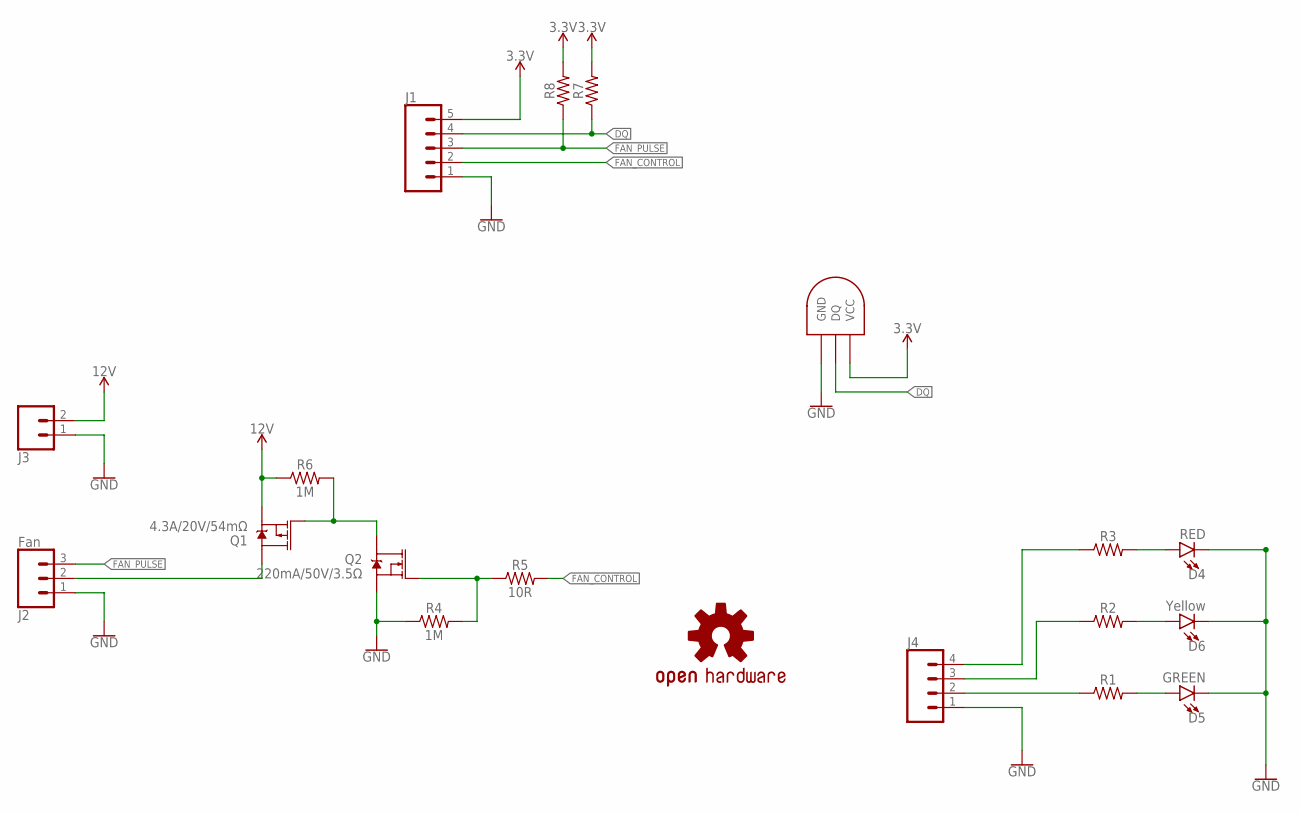
[picture p161: schematic McPiFace-60mmFan-V1.sch]

Parts:
D4: RED; LED-1206
D5: GREEN; LED-1206
D6: Yellow; LED-1206
J1: CONN_05SMD; 1X05_1MM
J2: Fan; JST-3-SMD
J3: CONN_02-JST-2MM-SMT; JST-2-SMD
J4: CONN_04SMD2; 1X04_1MM_RA
LOGO1: OSHW-LOGOL; OSHW-LOGO-L
Q1: 4.3A/20V/54mΩ; SOT23-3
Q2: 220mA/50V/3.5Ω; SOT23-3
R1, R2, R3: 1206
R4, R6: 1M; 0805
R5: 10R; 0805
R7, R8: 0805
U$1: DS1820SOIC; DS18B20_SOIC

Connections:
3.3V: J1.5, R7.2, R8.2, U$1.VCC
12V: J3.2 (1), Q1.2 (S), R6.1
DQ: J1.4, R7.1, U$1.DQ
FAN_CONTROL: J1.2, R5.2
FAN_PULSE: J1.3, J2.3 (1), R8.1
GND: D4.C, D5.C, D6.C, J1.1, J2.1 (3), J3.1 (2), J4.1, Q2.2 (S), R4.1, U$1.GND
unnamed: D4.A, R3.2
unnamed: D6.A, R2.2
unnamed: D5.A, R1.2
unnamed: J4.2, R1.1
unnamed: J4.3, R2.1
unnamed: J4.4, R3.1
unnamed: J2.2, Q1.3 (D)
unnamed: Q1.1 (G), Q2.3 (D), R6.2
unnamed: Q2.1 (G), R4.2, R5.1

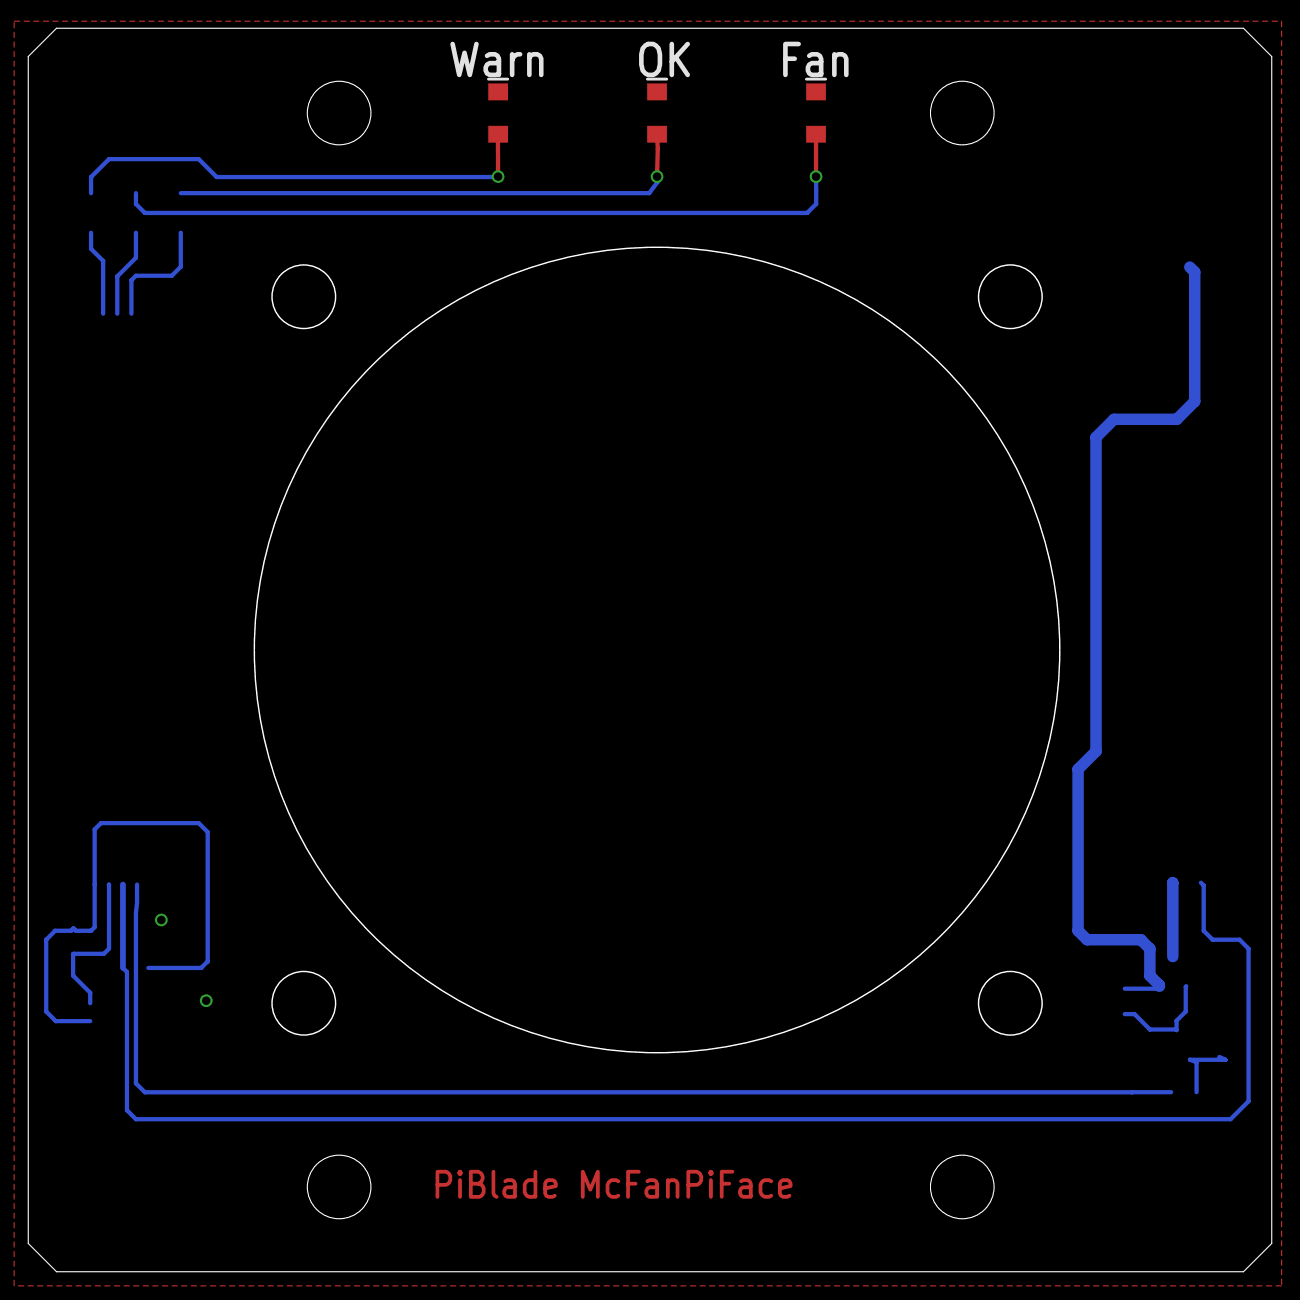
[picture p162: board McPiFace-60mmFan-V1.brd from above]

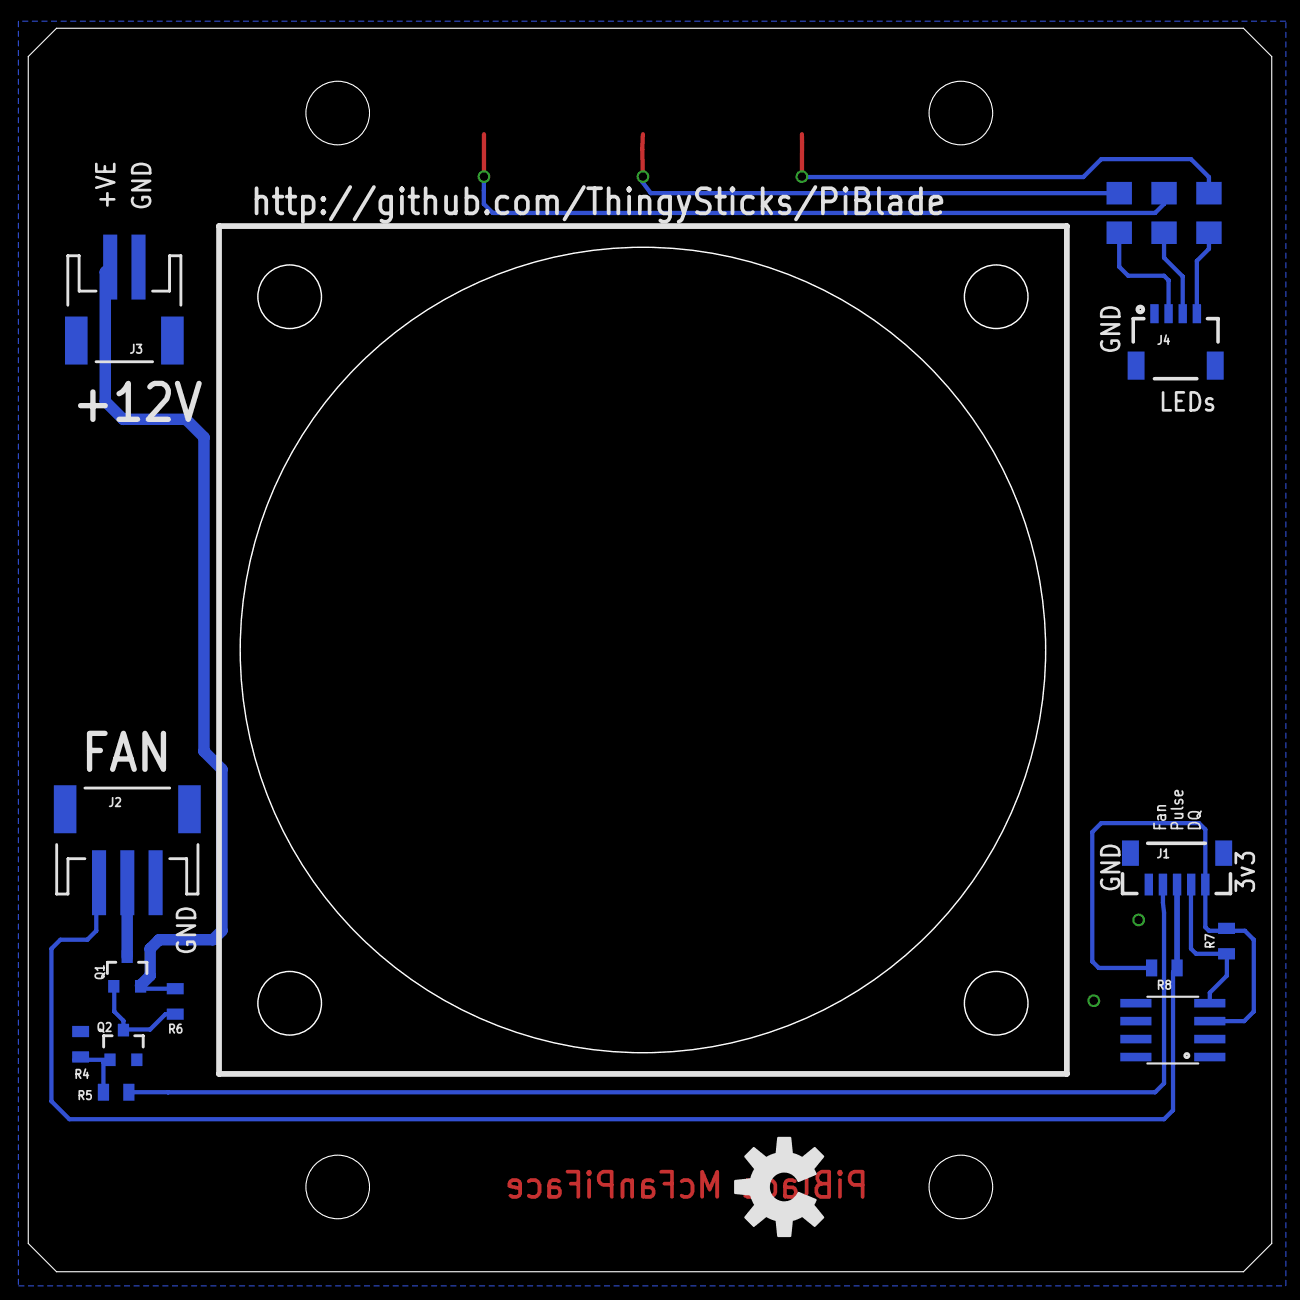
[picture p163: board McPiFace-60mmFan-V1.brd from below]

Board: 2 copper layers, 88.0 x 88.0 mm, 19 parts (16 on the bottom side), 15 nets.
