ThingySticks/PiBlade/FrontPanels/McPiFace/McPiFace-Status-V1.brd

## EAGLE design FrontPanels/McPiFace/McPiFace-Status-V1.brd (2019-01-14)

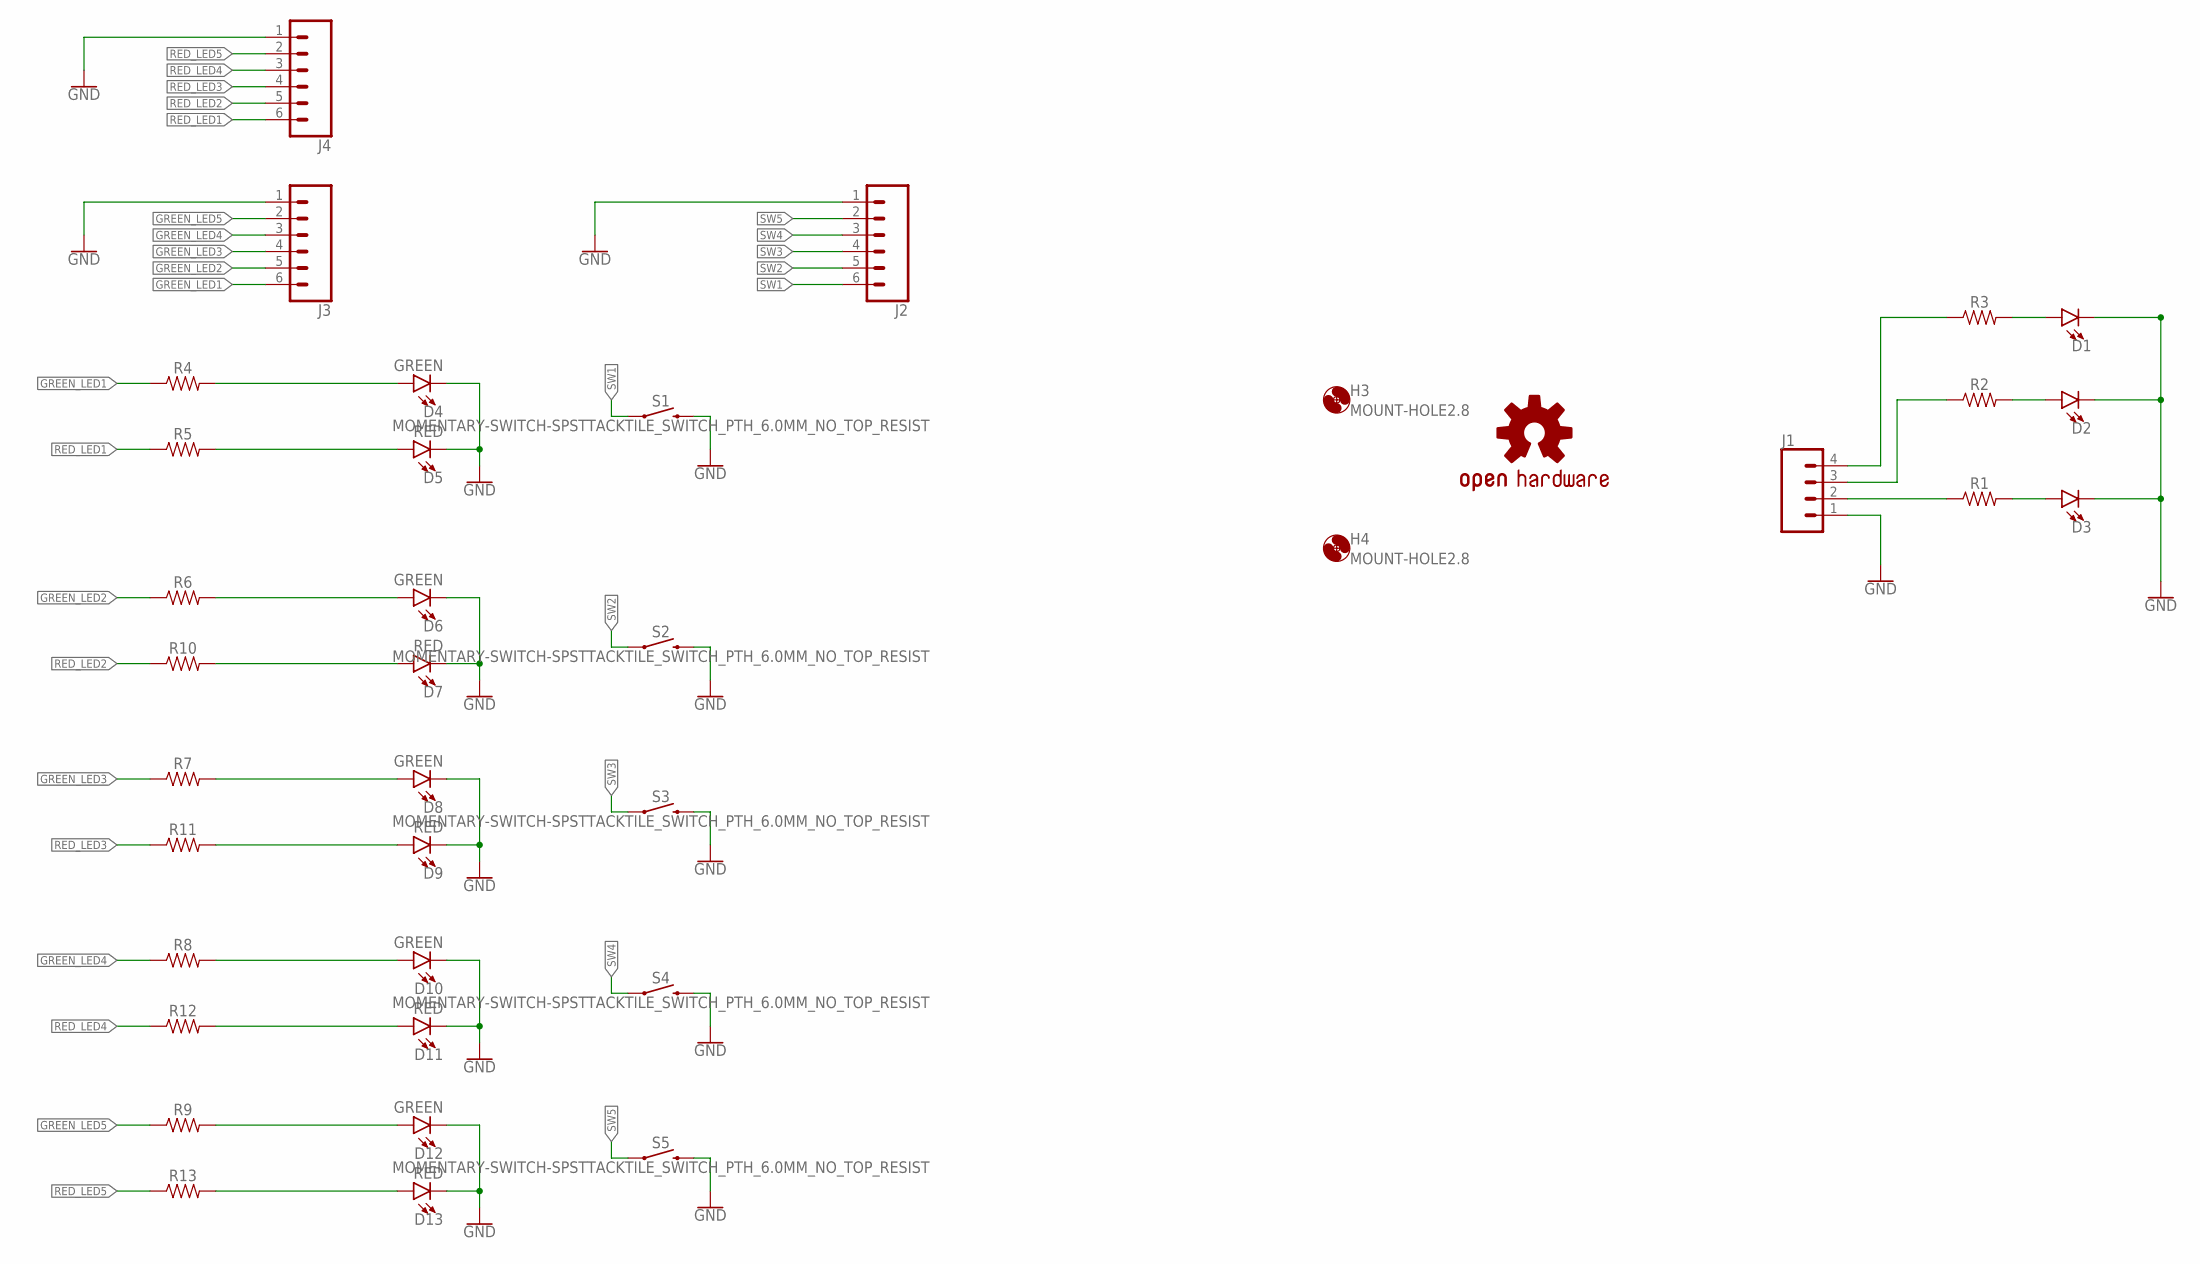
[picture p164: schematic McPiFace-Status-V1.sch]

Parts:
D1, D2, D3: LED1206-BOTTOM-1.6MM; LED-1206-BOTTOM-1.6MM
D4, D6, D8, D10, D12: GREEN; LED-1206
D5, D7, D9, D11, D13: RED; LED-1206
H3, H4: MOUNT-HOLE2.8; 2,8
J1: CONN_04SMD2; 1X04_1MM_RA
J2, J3, J4: CONN_06SMD-1MM; 1X06-1MM
LOGO1: OSHW-LOGOL; OSHW-LOGO-L
R1, R2, R3: 1206
R4, R5, R6, R7, R8, R9, R10, R11, R12, R13: 0805
S1, S2, S3, S4, S5: MOMENTARY-SWITCH-SPSTTACKTILE_SWITCH_PTH_6.0MM_NO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; TACTILE_SWITCH_PTH_6.0MM_NO_TOP_RESIST

Connections:
GND: D1.C, D2.C, D3.C, D4.C, D5.C, D6.C, D7.C, D8.C, D9.C, D10.C, D11.C, D12.C, D13.C, J1.1, J2.1, J3.1, J4.1, S1.3 (2), S2.3 (2), S3.3 (2), S4.3 (2), S5.3 (2)
GREEN_LED1: J3.6, R4.1
GREEN_LED2: J3.5, R6.1
GREEN_LED3: J3.4, R7.1
GREEN_LED4: J3.3, R8.1
GREEN_LED5: J3.2, R9.1
unnamed: D4.A, R4.2
unnamed: D1.A, R3.2
unnamed: D2.A, R2.2
unnamed: D3.A, R1.2
unnamed: J1.2, R1.1
unnamed: J1.3, R2.1
unnamed: J1.4, R3.1
unnamed: D6.A, R6.2
unnamed: D12.A, R9.2
unnamed: D10.A, R8.2
unnamed: D8.A, R7.2
unnamed: D5.A, R5.2
unnamed: D7.A, R10.2
unnamed: D9.A, R11.2
unnamed: D11.A, R12.2
unnamed: D13.A, R13.2
RED_LED1: J4.6, R5.1
RED_LED2: J4.5, R10.1
RED_LED3: J4.4, R11.1
RED_LED4: J4.3, R12.1
RED_LED5: J4.2, R13.1
SW1: J2.6, S1.1
SW2: J2.5, S2.1
SW3: J2.4, S3.1
SW4: J2.3, S4.1
SW5: J2.2, S5.1

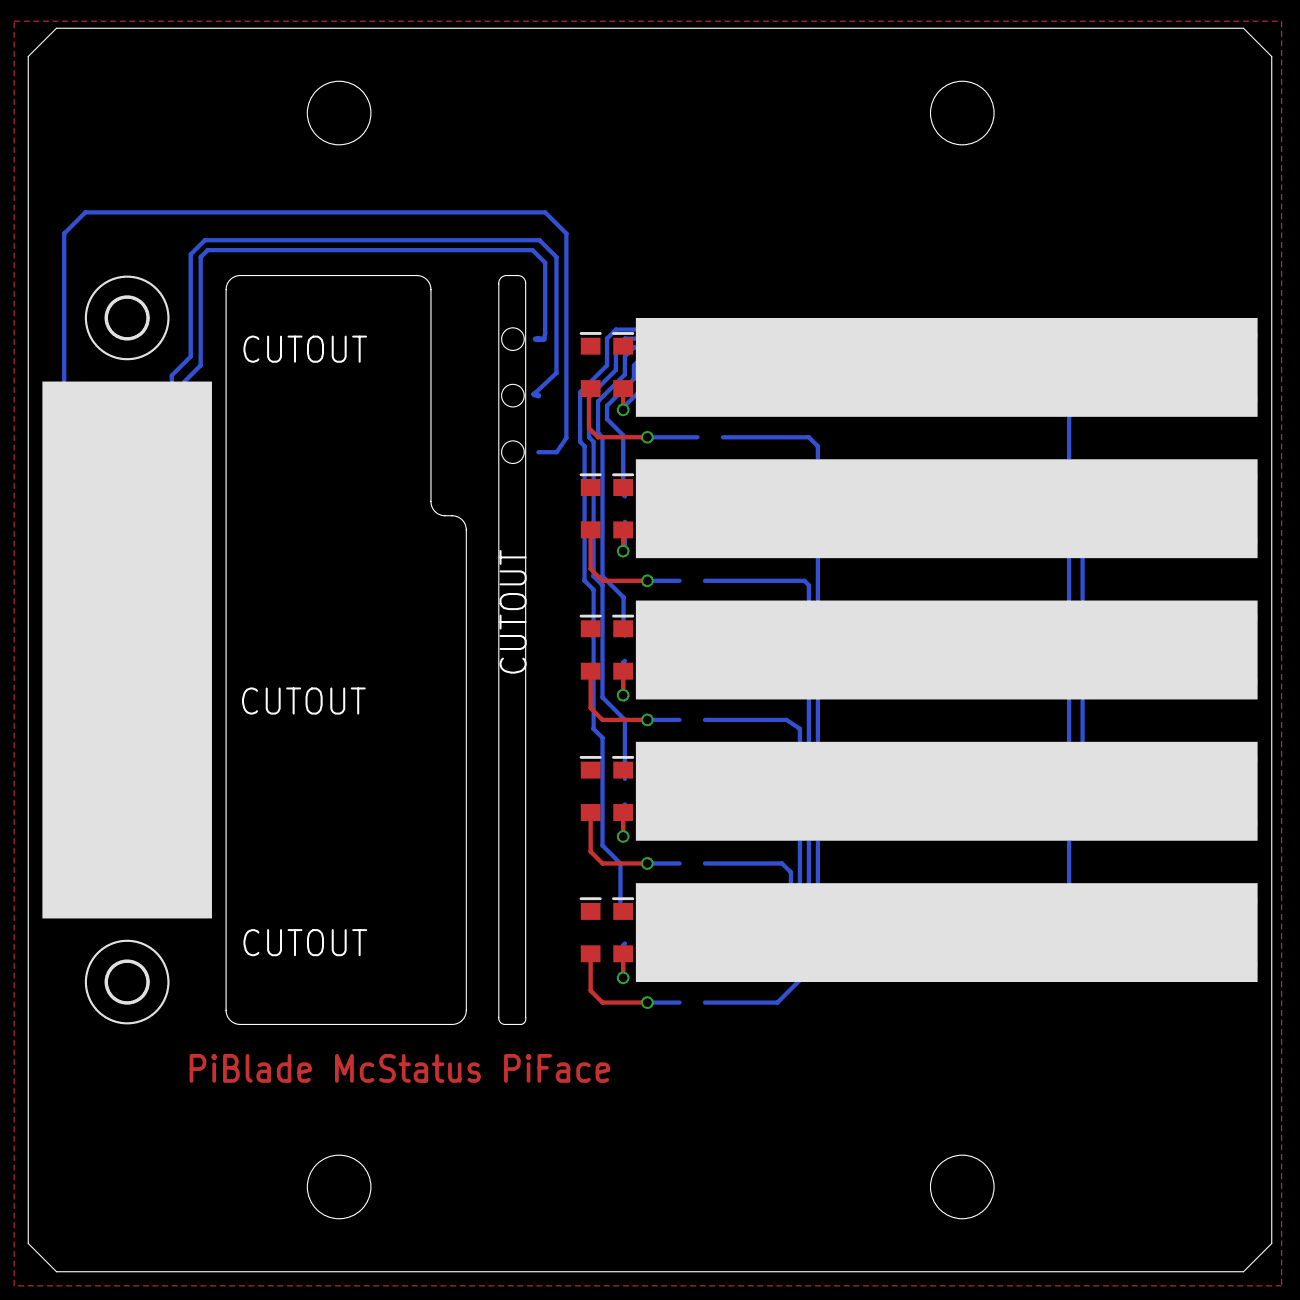
[picture p165: board McPiFace-Status-V1.brd from above]

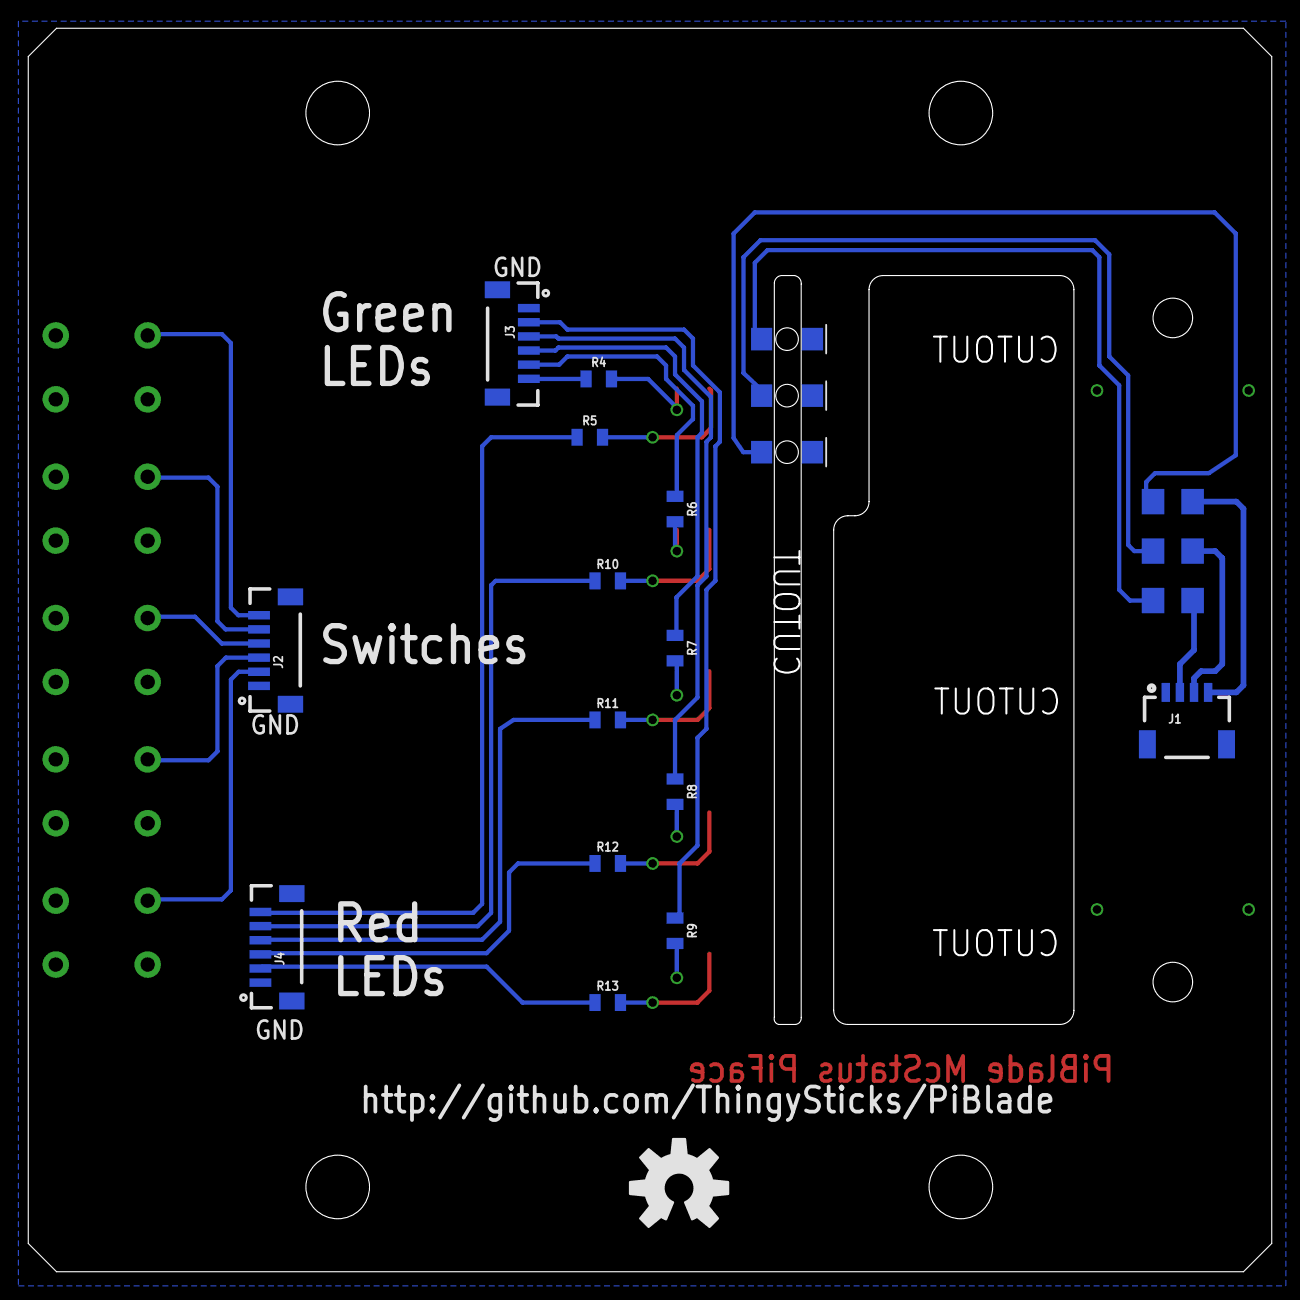
[picture p166: board McPiFace-Status-V1.brd from below]

Board: 2 copper layers, 88.0 x 88.0 mm, 38 parts (21 on the bottom side), 32 nets.
